svenpetersen1965/PET-Diagnostic-Clip/CBM8296_Harness/CBM8296 Diagnostic J4 Breakout Board/Rev. 0/text/210_cover_sheet.docx

Project Documentation

Commodore CBM8296 Diagnostic: J4 Breakout Board

Project number: 210

Revision: 0

Date: 16.05.2023

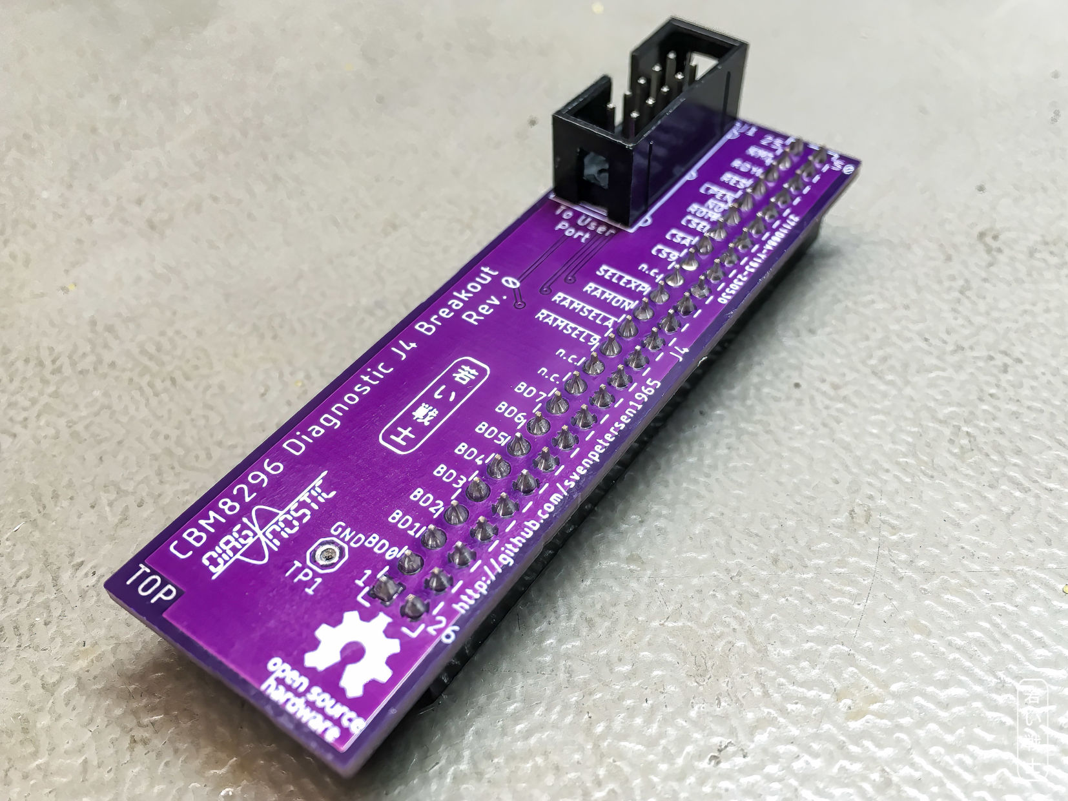
[picture p43: figure]
