svenpetersen1965/PET-Diagnostic-Clip/CBM8296_Harness/CBM8296 Diagnostic Keyboard Dongle/Rev. 0/text/212_cover_sheet.docx

Project Documentation

Commodore CBM8296 Diagnostic: Keyboard Dongle

Project number: 212

Revision: 0

Date: 16.05.2023

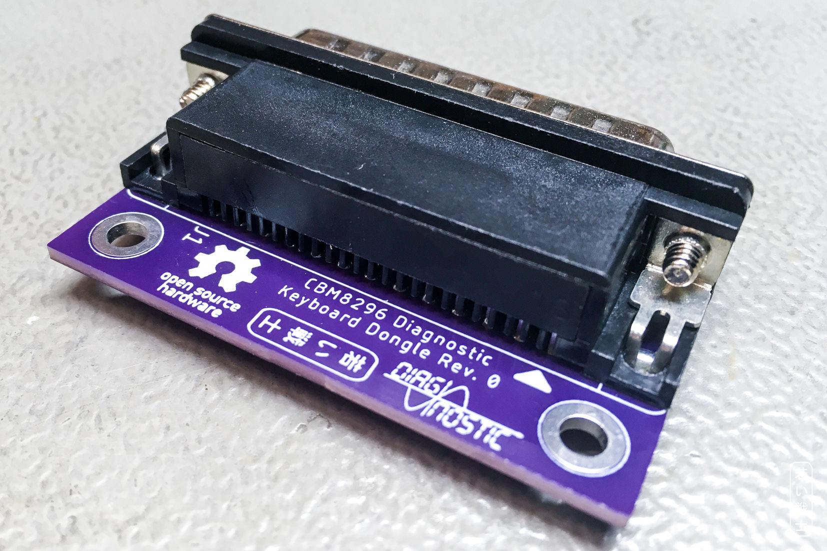
[picture p90: figure]
