svenpetersen1965/PET-Diagnostic-Clip/CBM8296_Harness/CBM8296 Diagnostic Cassette Dongle/Rev. 0/text/211_cover_sheet.docx

Project Documentation

Commodore CBM8296 Diagnostic: Cassette Dongle

Project number: 211

Revision: 0

Date: 16.05.2023

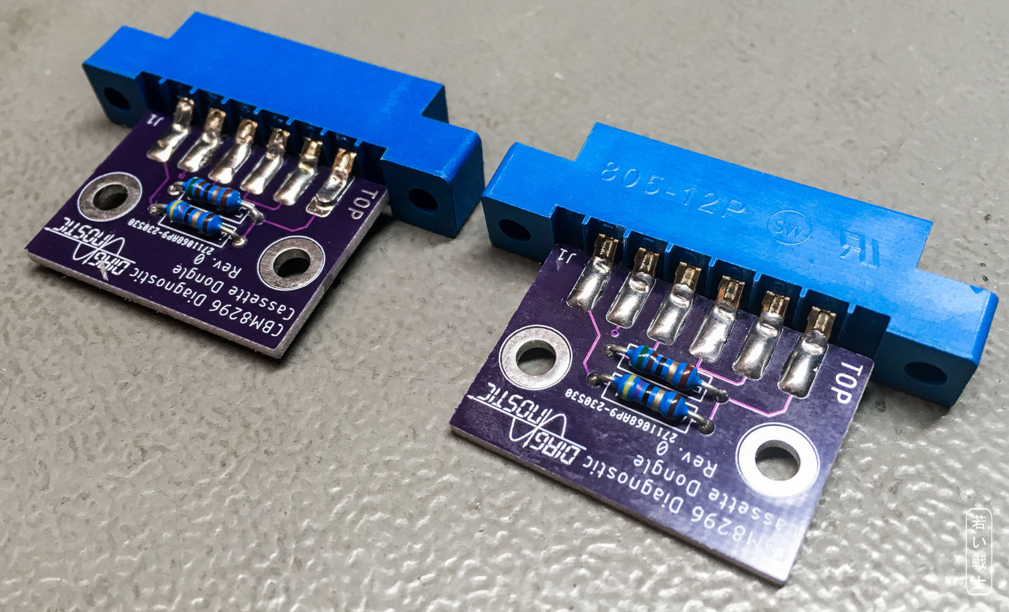
[picture p91: figure]
