svenpetersen1965/PET-Diagnostic-Clip/CBM8296_Harness/CBM8296 Diagnostic J4 Breakout Board/Rev. 0/pictures/dimensions.png

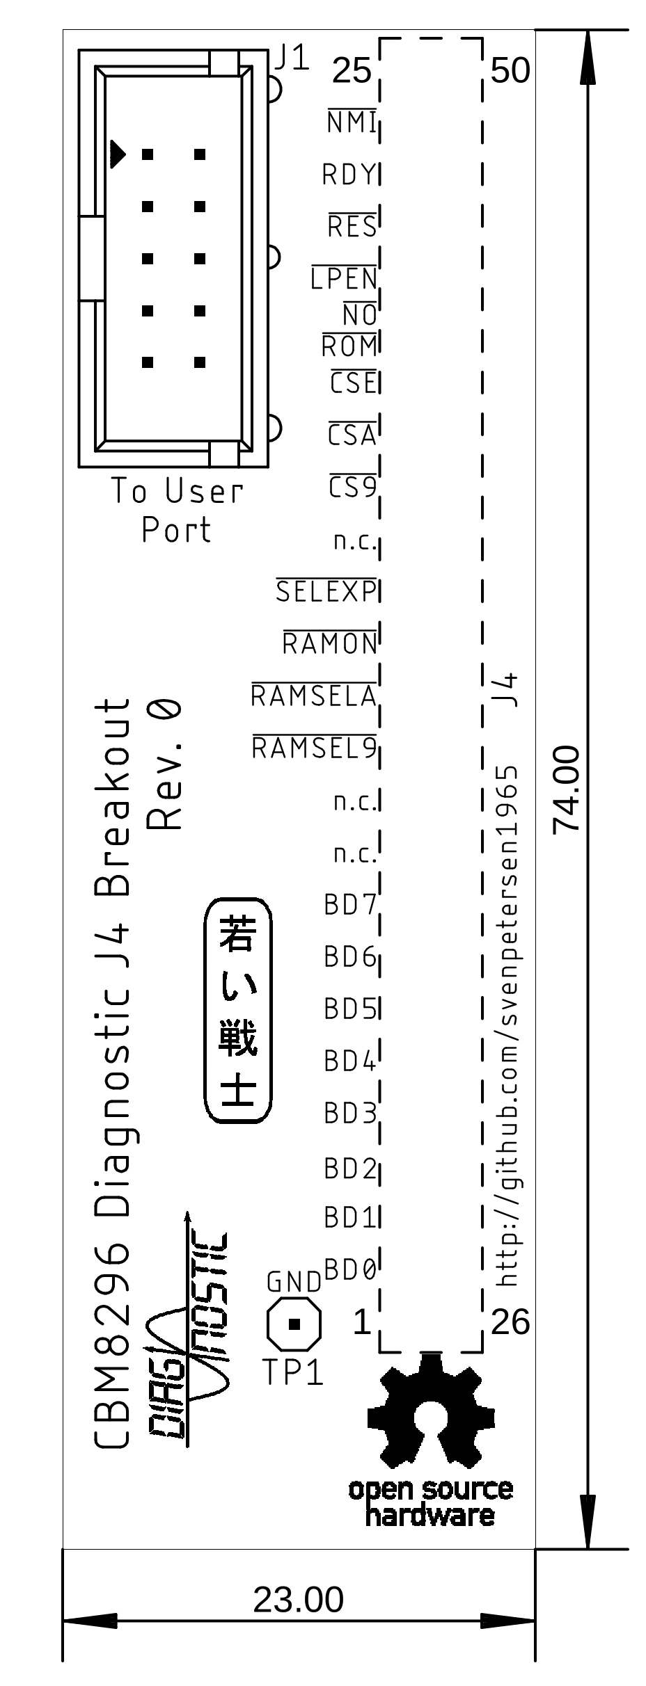
CBM8296_Harness/CBM8296 Diagnostic J4 Breakout Board/Rev. 0/pictures/dimensions.png
