svenpetersen1965/PET-Diagnostic-Clip/Diagnostic Software/40_col_diagnostic_v2.0.BIN.png

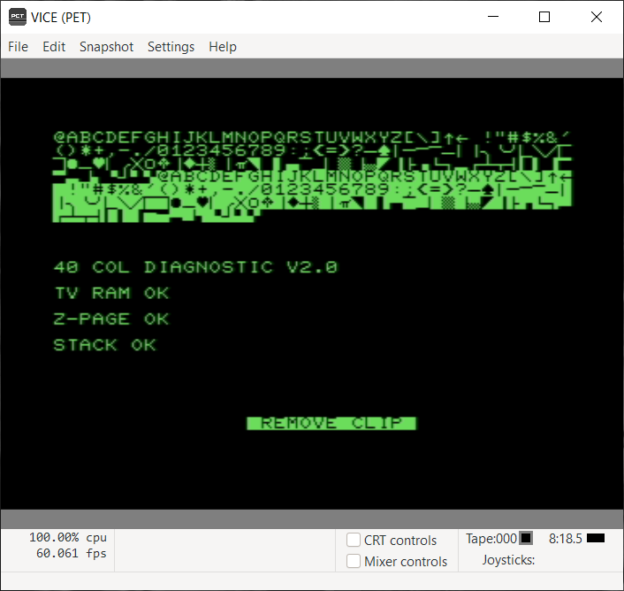
Diagnostic Software/40_col_diagnostic_v2.0.BIN.png
