svenpetersen1965/PET-Diagnostic-Clip/Diagnostic Software/80_col_diagnostic_v1.1.bin.png

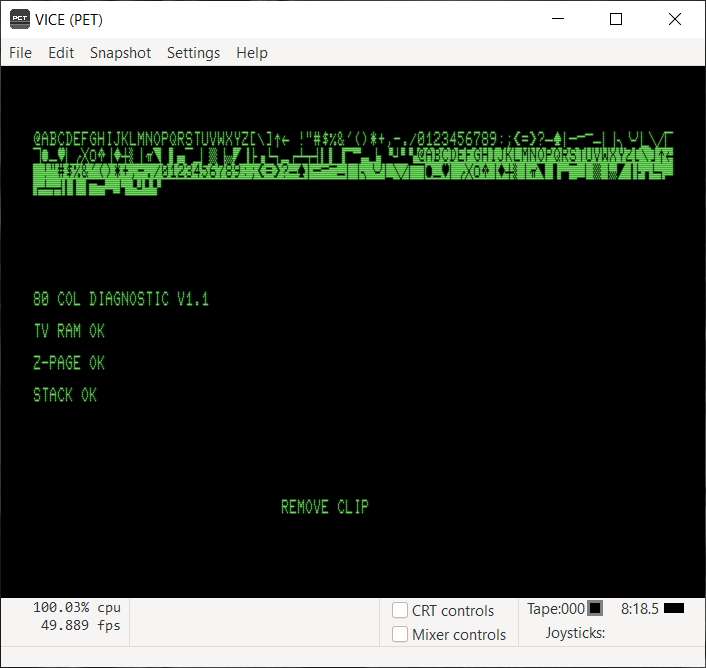
Diagnostic Software/80_col_diagnostic_v1.1.bin.png
