svenpetersen1965/PET-Diagnostic-Clip/Diagnostic Software/901447-30_diagnostic_320350g.bin.png

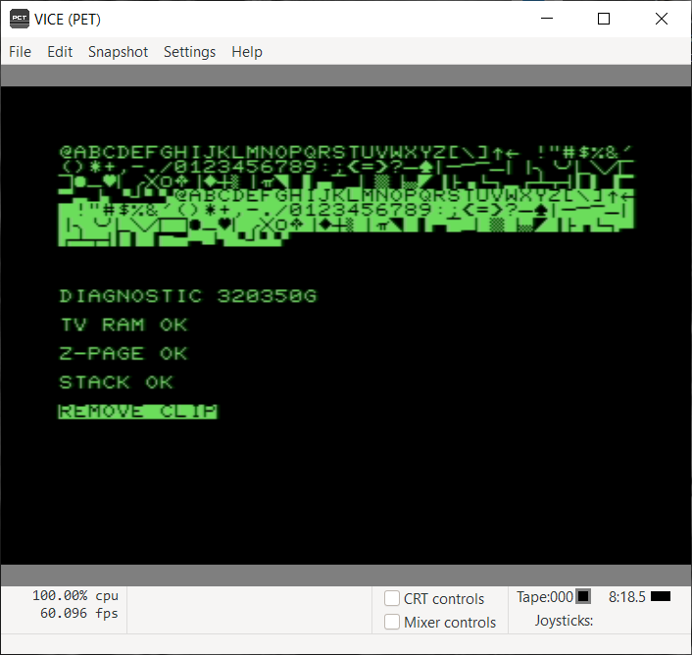
Diagnostic Software/901447-30_diagnostic_320350g.bin.png
