svenpetersen1965/PET-Diagnostic-Clip/PET-Diagnostic_Keyboard_PCB/Rev. 0/Pictures/Keyboard Connector.png

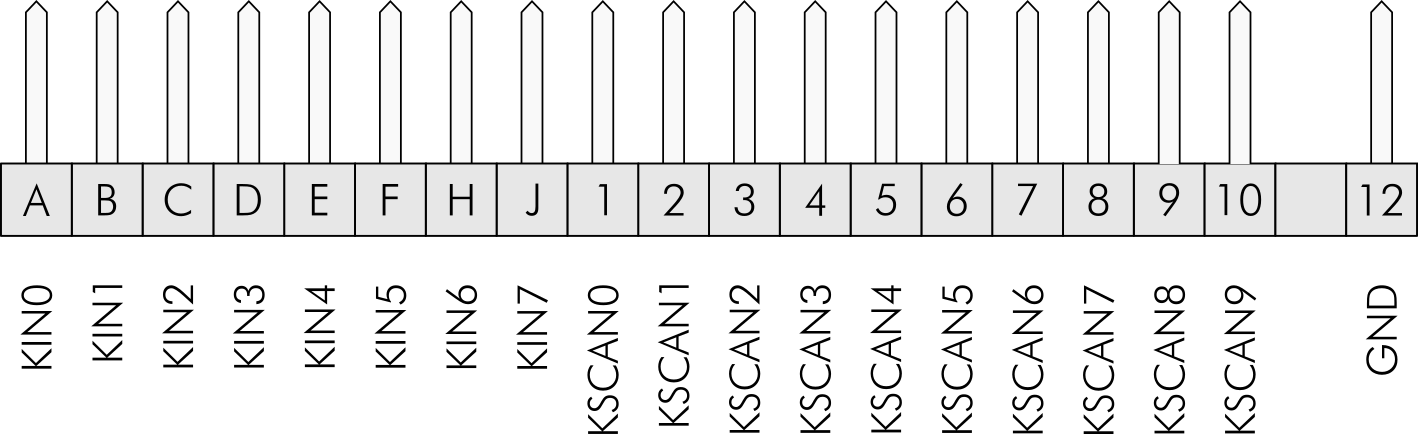
PET-Diagnostic_Keyboard_PCB/Rev. 0/Pictures/Keyboard Connector.png
