svenpetersen1965/PET-Diagnostic-Clip/PET_Diagnostic_Clip/case/Rev. 3/Label/clip_label.png

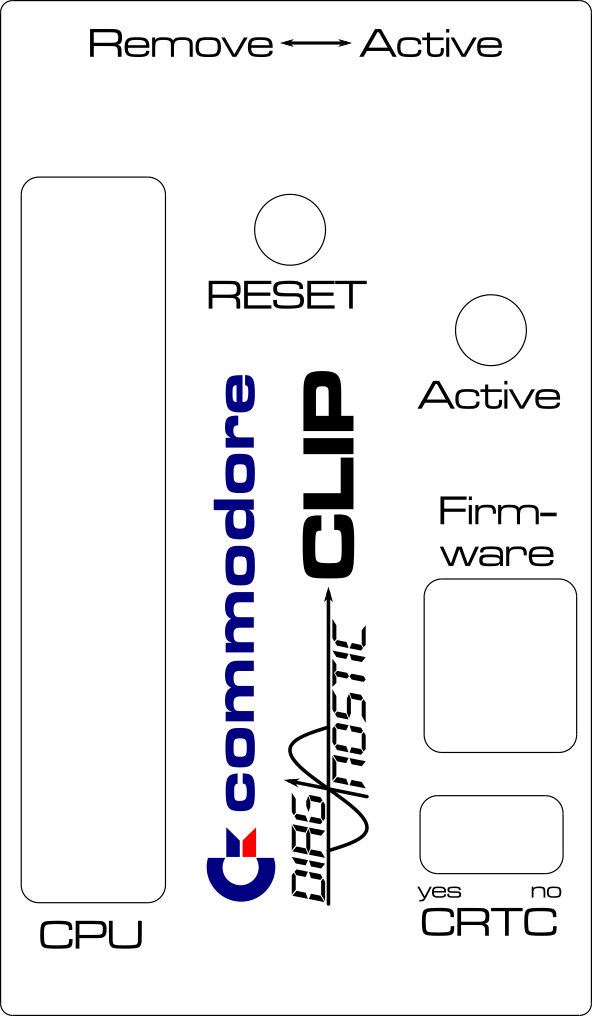
PET_Diagnostic_Clip/case/Rev. 3/Label/clip_label.png
