svenpetersen1965/PET-Diagnostic-Clip/PET_Diagnostic_Clip/Rev. 0/Pictures/0340_-_CPUada_Clip.JPG

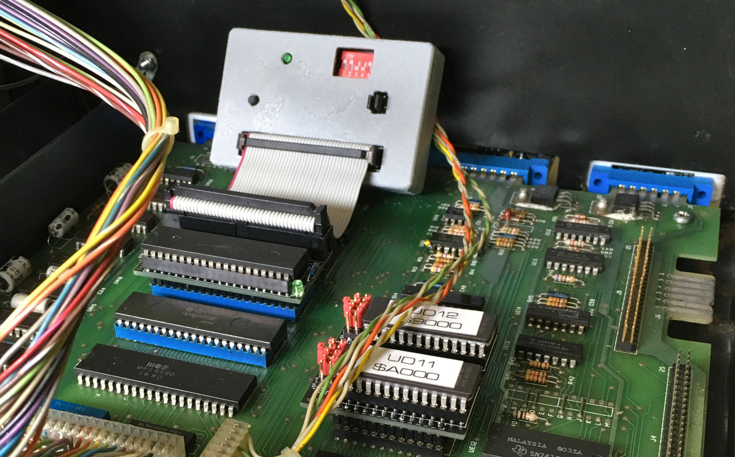
PET_Diagnostic_Clip/Rev. 0/Pictures/0340_-_CPUada_Clip.JPG
