svenpetersen1965/PET-Diagnostic-Clip/PET_Diagnostic_Clip/Rev. 0/Pictures/3843_-_Diag_Clip_PCB_v0.JPG

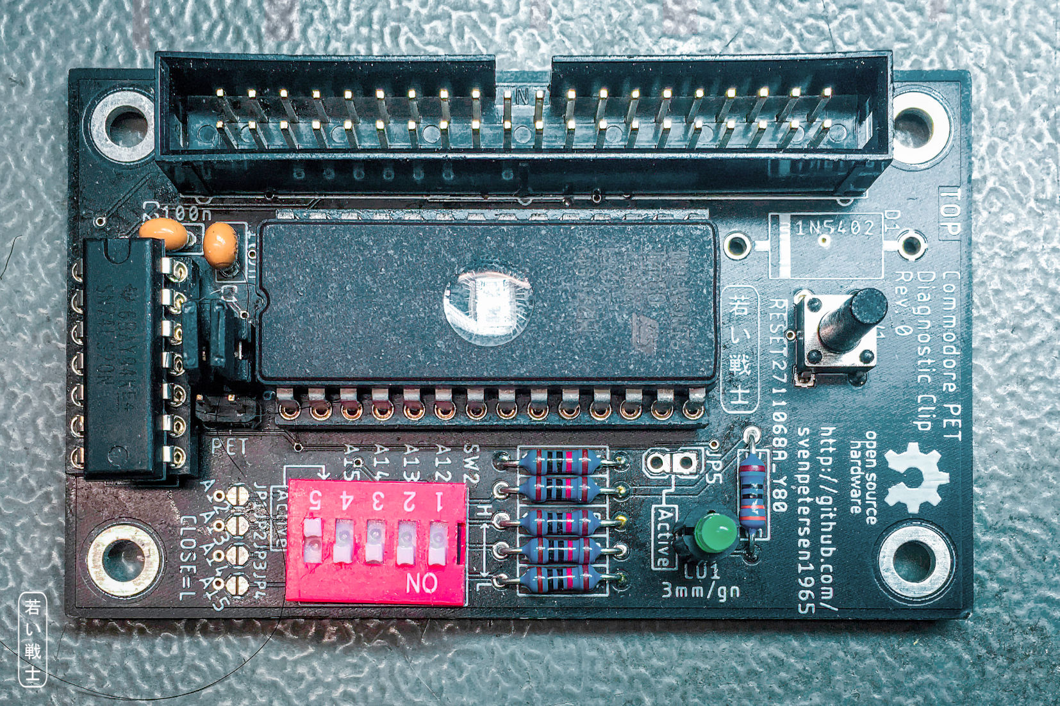
PET_Diagnostic_Clip/Rev. 0/Pictures/3843_-_Diag_Clip_PCB_v0.JPG
