svenpetersen1965/PET-Diagnostic-Clip/PET_Diagnostic_Clip/Rev. 0/Pictures/7300_-_cbm_diag_pcbs.JPG

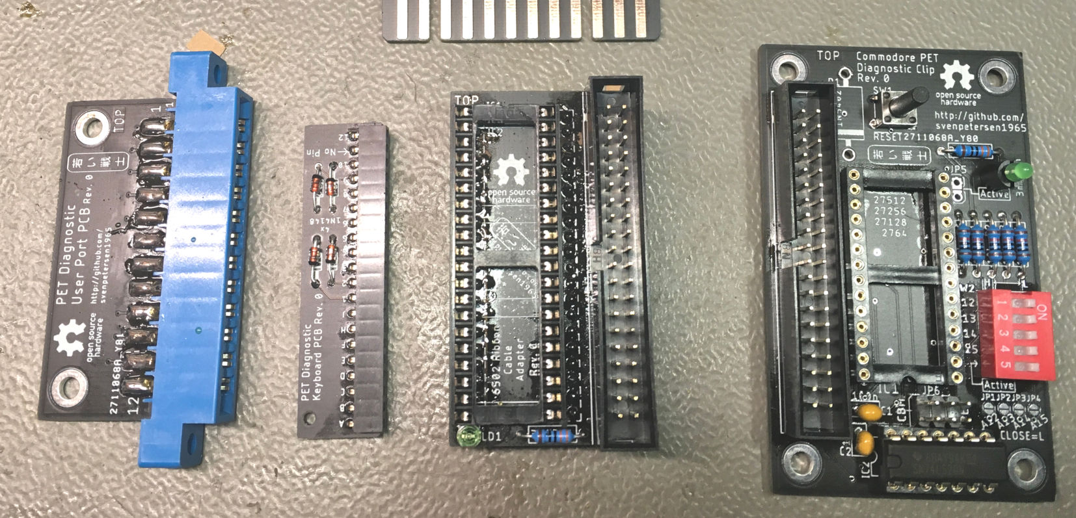
PET_Diagnostic_Clip/Rev. 0/Pictures/7300_-_cbm_diag_pcbs.JPG
