svenpetersen1965/PET-Diagnostic-Clip/PET_Diagnostic_Clip/Rev. 0/Pictures/7304_-_clip_kb_up.JPG

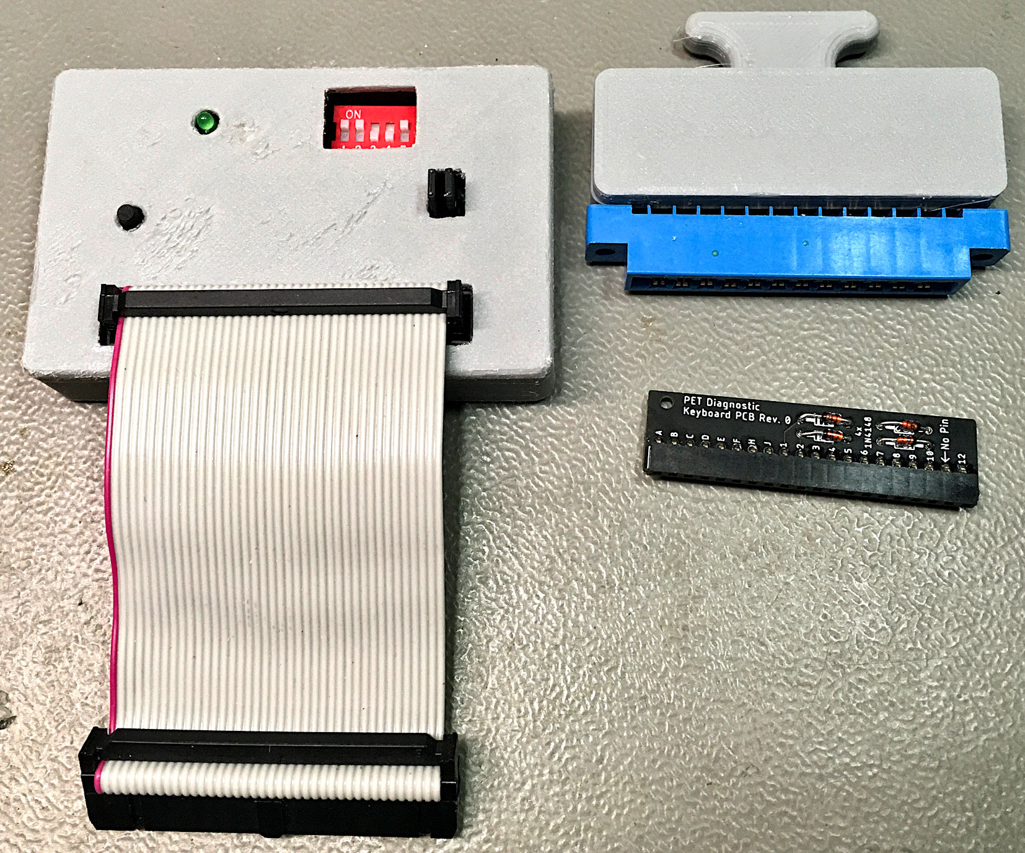
PET_Diagnostic_Clip/Rev. 0/Pictures/7304_-_clip_kb_up.JPG
