svenpetersen1965/PET-Diagnostic-Clip/PET_Diagnostic_Clip/Rev. 0/Pictures/dimensions.png

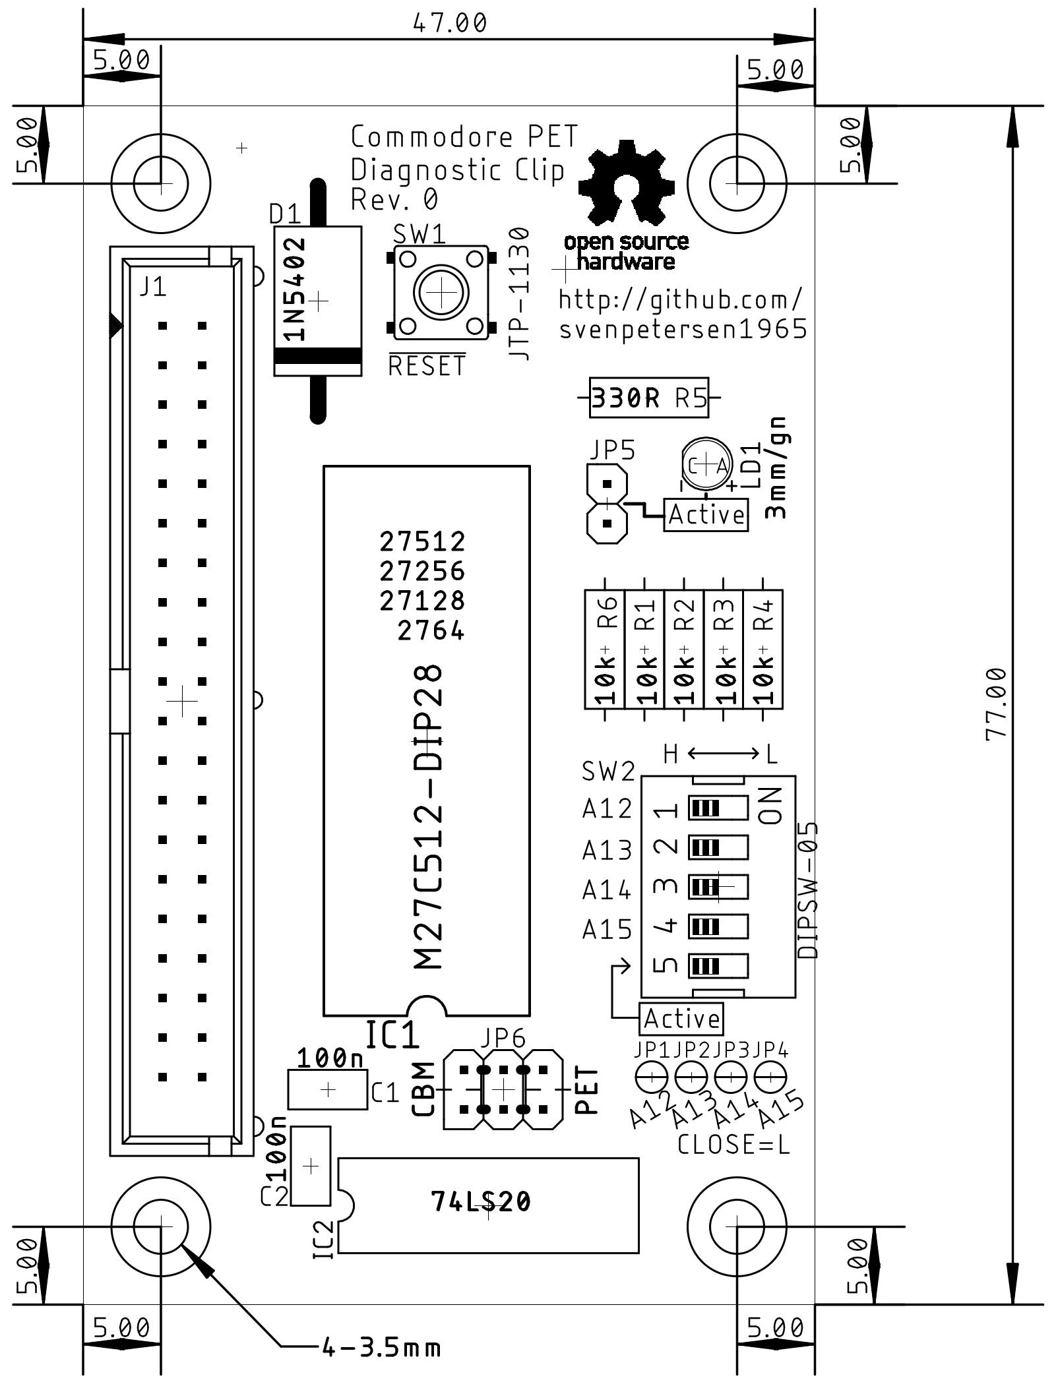
PET_Diagnostic_Clip/Rev. 0/Pictures/dimensions.png
