svenpetersen1965/PET-Diagnostic-Clip/PET_Diagnostic_Clip/Rev. 1/Pictures/0342_-_Diag_80cl_v1_1.JPG

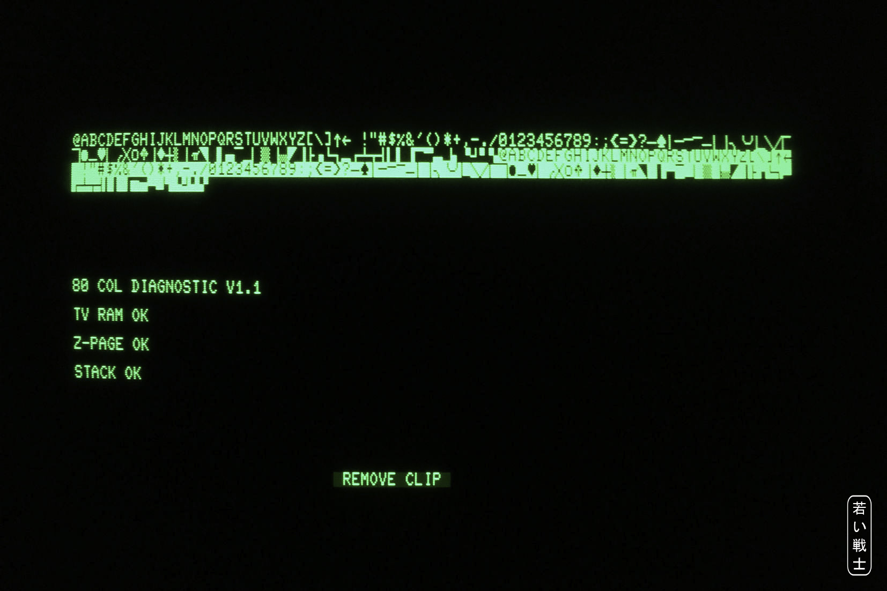
PET_Diagnostic_Clip/Rev. 1/Pictures/0342_-_Diag_80cl_v1_1.JPG
