svenpetersen1965/PET-Diagnostic-Clip/PET_Diagnostic_Clip/Rev. 1/Pictures/0711_-_Clip_rev1.JPG

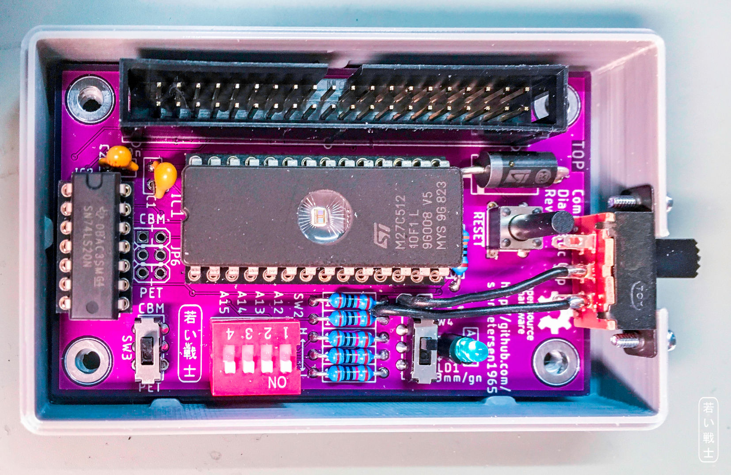
PET_Diagnostic_Clip/Rev. 1/Pictures/0711_-_Clip_rev1.JPG
