svenpetersen1965/PET-Diagnostic-Clip/PET_Diagnostic_Clip/Rev. 1/Pictures/0712_-_clip_rev.1.JPG

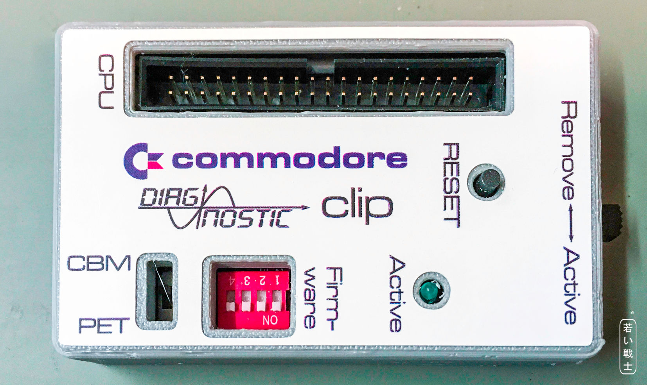
PET_Diagnostic_Clip/Rev. 1/Pictures/0712_-_clip_rev.1.JPG
