svenpetersen1965/PET-Diagnostic-Clip/PET_Diagnostic_Clip/Rev. 1/Pictures/0728_-_clip_complete.JPG

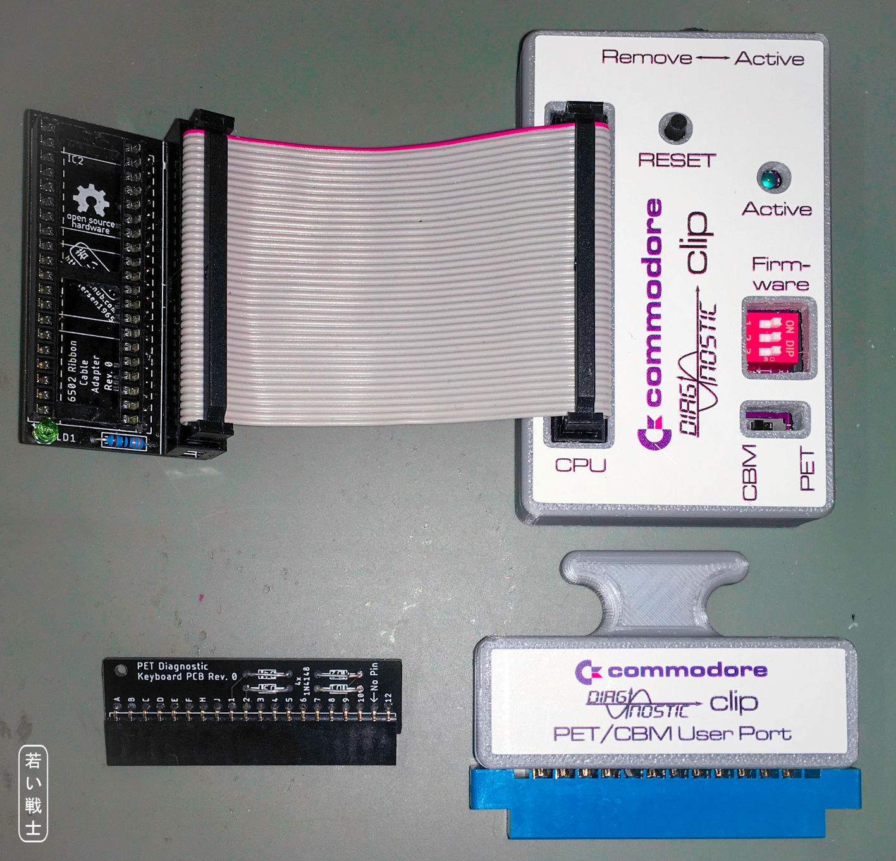
PET_Diagnostic_Clip/Rev. 1/Pictures/0728_-_clip_complete.JPG
