svenpetersen1965/PET-Diagnostic-Clip/PET_Diagnostic_Clip/Rev. 1/Pictures/3514_-_diag_80col_8032_loop.JPG

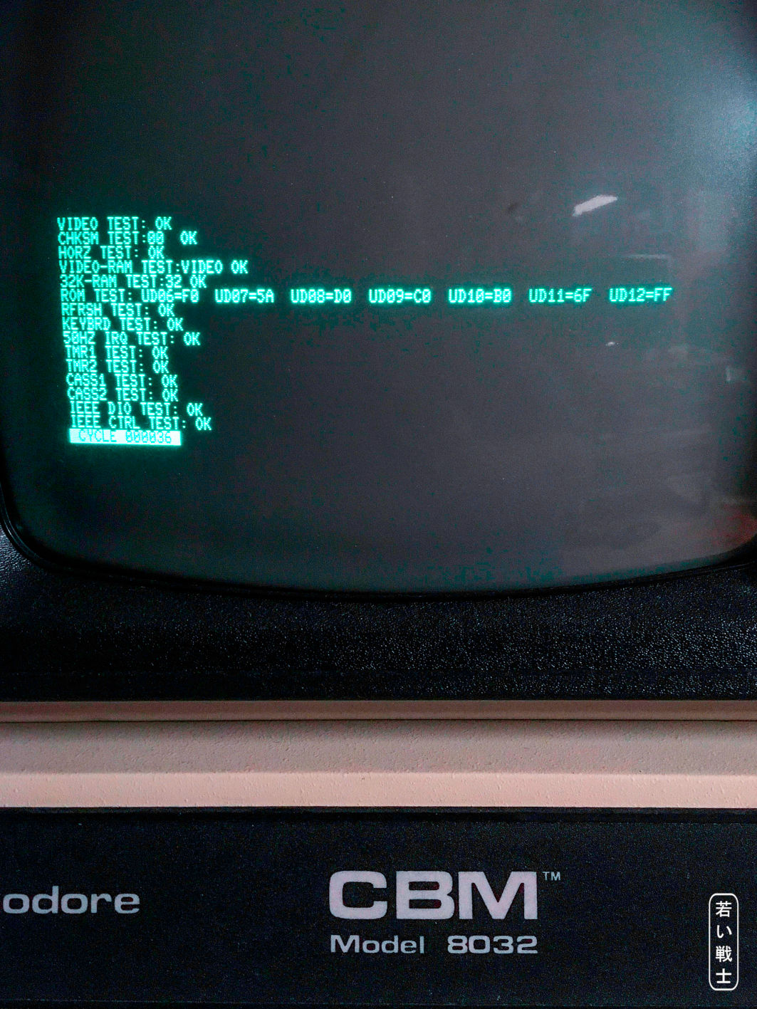
PET_Diagnostic_Clip/Rev. 1/Pictures/3514_-_diag_80col_8032_loop.JPG
