svenpetersen1965/PET-Diagnostic-Clip/PET_Diagnostic_Clip/Rev. 2/Pictures/3821_-_clipv2_open.JPG

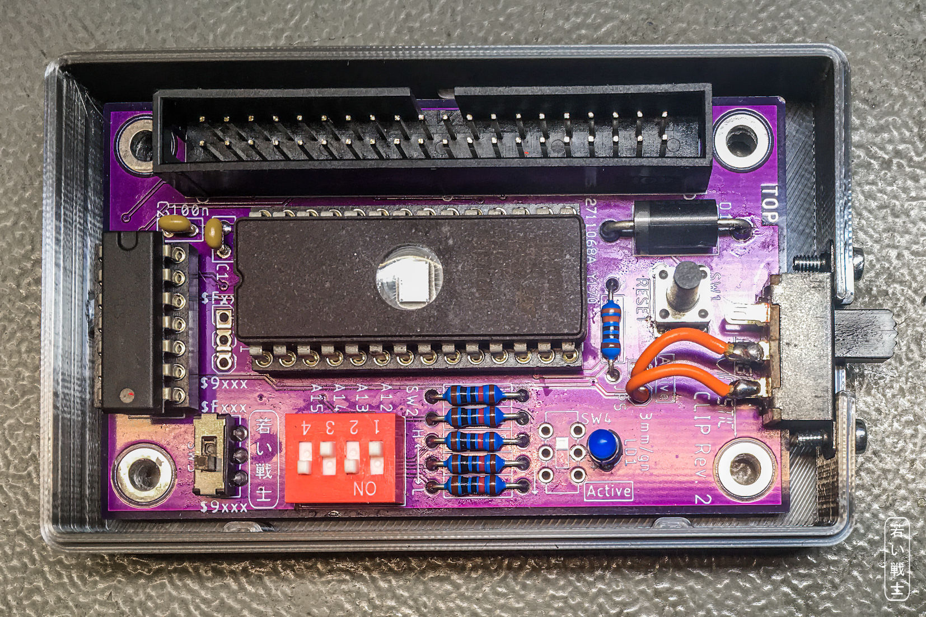
PET_Diagnostic_Clip/Rev. 2/Pictures/3821_-_clipv2_open.JPG
