svenpetersen1965/PET-Diagnostic-Clip/PET_Diagnostic_Clip/Rev. 3/Pictures/2621_-_clip_v3.JPG

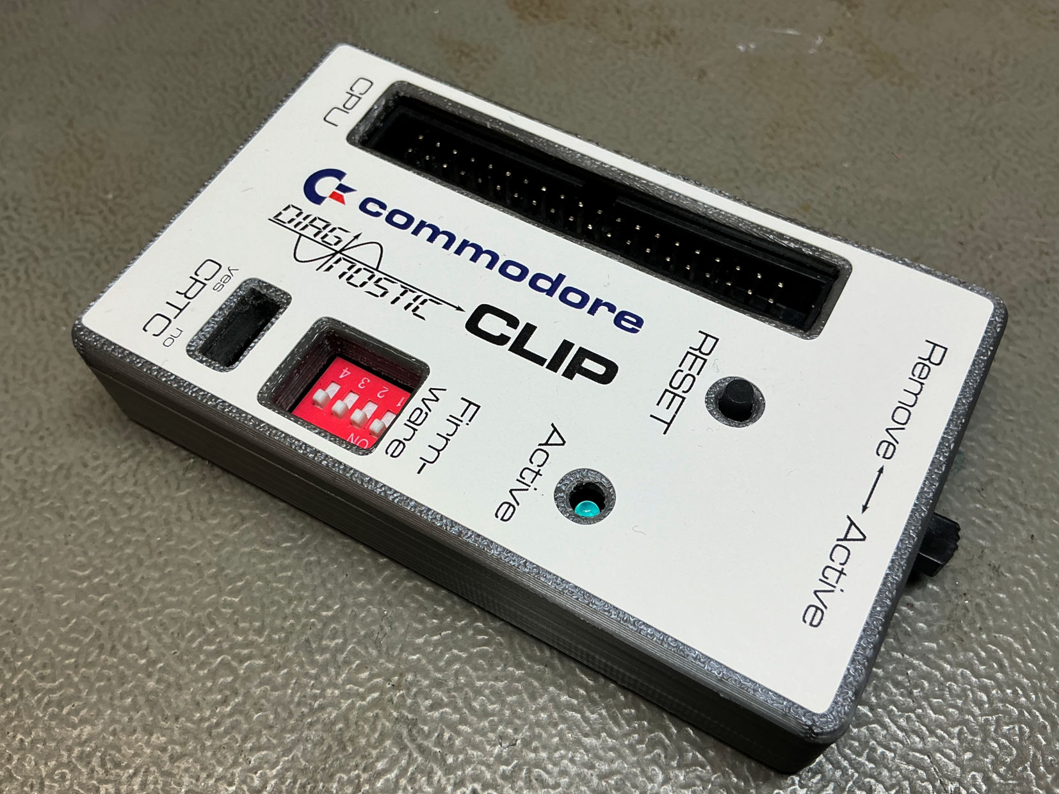
PET_Diagnostic_Clip/Rev. 3/Pictures/2621_-_clip_v3.JPG
