svenpetersen1965/PET-Diagnostic-Clip/PET_Diagnostic_Clip/Rev. 3/Pictures/4428_-_3016_diag320350g_start.JPG

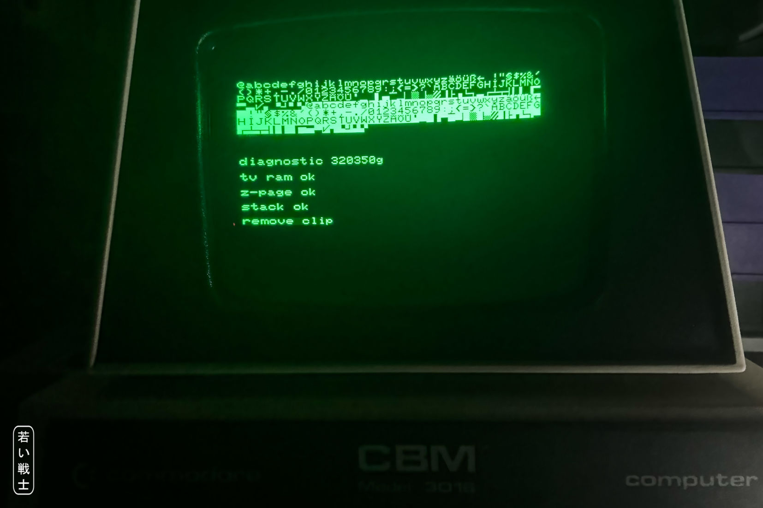
PET_Diagnostic_Clip/Rev. 3/Pictures/4428_-_3016_diag320350g_start.JPG
