svenpetersen1965/PET-Diagnostic-Clip/PET_Diagnostic_Clip/Rev. 3/Pictures/4429_-_3016_diag320350g_loop1.JPG

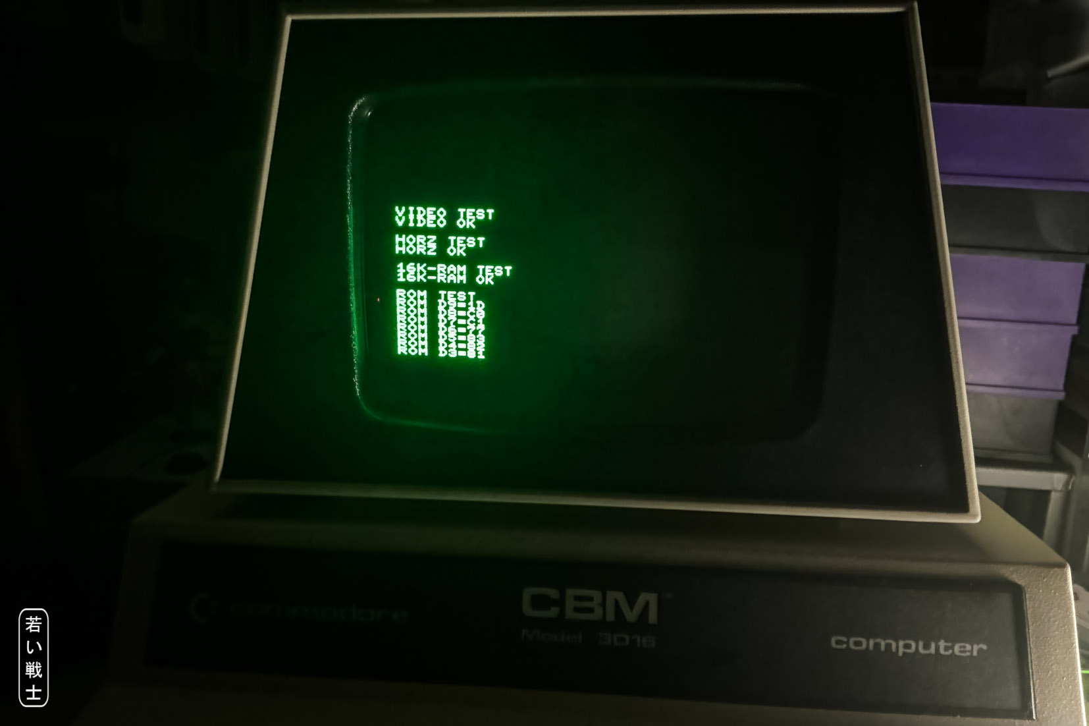
PET_Diagnostic_Clip/Rev. 3/Pictures/4429_-_3016_diag320350g_loop1.JPG
