svenpetersen1965/PET-Diagnostic-Clip/PET-Diagnostic_Keyboard_PCB/Rev. 0/Excel/PETDiag_KBDongle_calc_v0_0.xlsx

Commodore PET Diagnostic Clip: Keyboard Dongle Rev. 0
Calculation (of 13.12.2022) Rev. 0.0
Pos. | Qty | Value | €/ea | € | Comment
1 | 1 | 166-2-01-00 | 1.00 € | 1.00 € | 2 layer, Cu 35µ, HASL, 53.0mm x 14.0mm, 1.6mm FR4
2 | 4 | 1N4148 | 0.03 € | 0.12 € | Diode 1N4148
3 | 1 | BL1-85AXX-20U | 0.50 € | 0.50 € | e.g. MPE Garry, Reichelt BL 1x20W8 2,54
4 |  |  | total | 1.62 €
