svenpetersen1965/PET-Diagnostic-Clip/PET_Diagnostic_User_Port_PCB/Rev. 0/Excel/PET_Diag_UP.csv

Qty | Value | Device | Package | Parts | Description
2 |  | BOHR3,5 | BOHR3,5 | DRL1, DRL2
1 | OPEN_SOURCE_HW | OPEN_SOURCE_HW | OPENHW | U$13
1 | PET-USERPORT | PET-USERPORT | USERPORT | J1
