svenpetersen1965/PET-Diagnostic-Clip/PET_Diagnostic_User_Port_PCB/Rev. 0/Excel/PETDiag_UPDongle_calc_v0_0.xlsx

Commodore PET Diagnostic Clip: User Port Dongle Rev. 0
Calculation of 13.12.2022 Rev. 0.0
Pos. | Qty | Value | €/ea | € | Comment
1 | 1 | 165-2-01-00 | 1.00 € | 1.00 € | 2 layer, Cu 35µ, HASL, 54.0mm x 20.0mm, 1.6mm FR4
2 | 1 | 2x12, 3.96mm pitch | 3.00 € | 3.00 € | edge connector, C64 user port, Ali Express: Series 805
3 |  |  | Total | 4.00 €
