svenpetersen1965/PET-Diagnostic-Clip/6502_Ribbon_Cable_Adapter/Rev. 0/Excel/PETDiag_6502Ada_calc_v0_0.xlsx

Commodore PET Diagnostic Clip: 6502 Ribbon Cable Adapter Rev. 0
Calculation Rev. 0.0
Pos. | Qty | Value | Spalte1 | Spalte2 | Comment
1 | 1 | 162-2-01-00 | 1.00 € | 1.00 € | 2 layer, Cu 35µ, HASL, 58.8mm x 32.0mm, 1.6mm FR4
2 | 1 | 2x20 box header, 2.54mm pitch | 0.23 € | 0.23 € | 2x20, box pin header or standard pin header, e.g. reichelt.de WSL 40G
3 | 1 | 330R | 0.10 € | 0.10 € | 1/4W, 5%
4 | 1 | 3mm/gn | 0.15 € | 0.15 € | standard LED 3mm/green
5 | 1 | 6502PINS | 2.60 € | 2.60 € | Precision round pin header, e.G. bkl-electronic.de Art.-Nr. 10120540, Reichelt BKL 10120540
6 | 2 | DIP40 socket | 0.69 € | 1.38 € | Socket for 6502
7 | 2 | IDC Socket | 0.27 € | 0.54 €
8 | 1 | 10cm ribbon cable, 40p, 1.27mm | 0.23 € | 0.23 €
 |  |  | total | 6.23 €
