svenpetersen1965/PET-Diagnostic-Clip/PET_Diagnostic_Clip/Rev. 1/Excel/PETDiag_Clip_calc_v1_0.xlsx

Commodore PET Diagnostic: Diagnostic Clip Rev. 1
Calculation (13.12.2022) Rev. 1.0
Pos. | Qty | Value | €/ea | € | Comment
1 | 1 | 163-2-01-01 | 1.00 € | 1.00 € | 2 layer, Cu 35µ, HASL, 77.0mm x 47.0mm, 1.6mm FR4
2 | 1 | external DPDT switch wired up | 0.45 € | 0.45 € | Reichelt.de: T217 or AliExpress SS22F25-G7 + 10cm AWG24 cable
3 | 1 | 2x20 box header, 2.54mm pitch | 0.23 € | 0.23 € | 2x20, box pin header or standard pin header, e.g. reichelt.de WSL 40G
4 | 2 | 100n/50V | 0.10 € | 0.20 € | cer. cap, 2.5mm pitch
5 | 5 | 10k | 0.10 € | 0.50 € | 1/4W, 5%
6 | 1 | 1N5402 | 0.08 € | 0.08 € | 5V TVS diode. ST Micro. E.g. Reichelt: 1N 5908, tme.eu: 1N5908
7 | 1 | 330R | 0.10 € | 0.10 € | 1/4W, 5%
8 | 1 | 3mm/gn | 0.15 € | 0.15 € | standard LED 3mm/green
9 | 1 | 74LS20 | 1.06 € | 1.06 € | e.G. RENESAS, e.G. Reichelt LS 20
10 | 1 | DIPSW-04 | 0.35 € | 0.35 € | Standard DIP-Switch with 4 switches (switch side facing up) The DIP-Switch can be replaced with a 2 switch DIP Switch and hardwire switch 3 and 4. Reichelt NT 04 or NT 02
11 | 1 | mini slide switch, 2.54mm, DPDT, through hole | 0.15 € | 0.15 € | Ali Express, ebay, Amazon, search term "MSS22D18"
12 | 0 | mini slide switch, 2.54mm, DPDT, through hole | 0.15 € | 0.00 € | do not place
13 | 1 | JTP-1130 | 0.16 € | 0.16 € | standard TACT switch 6mm x 6mm, height = 13mm
14 | 0 | JUMPER2X3 | 0.00 € | 0.00 € | do not place
15 | 1 | M27C512-DIP28 | 6.70 € | 6.70 € | M27C512 EPROM (or M27C256 or M27C128)
 |  |  | total | 11.13 €
