svenpetersen1965/PET-Diagnostic-Clip/PET_Diagnostic_Clip/case/Rev. 1/stl/Diag_clip_top_shell.stl

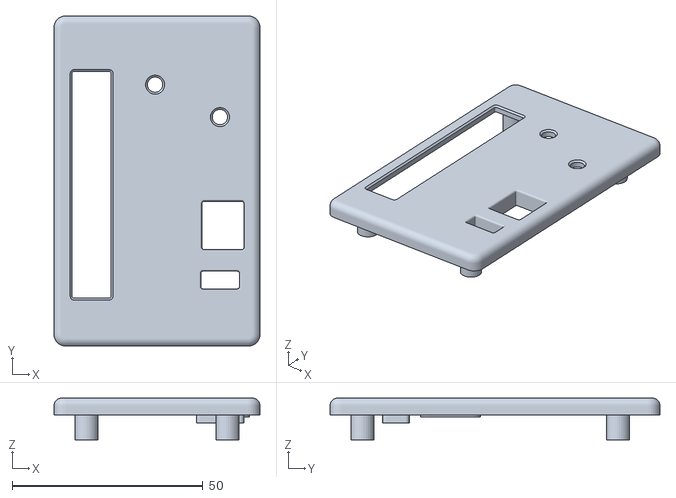
[picture p128: CAD file, 2023-02-27]
PET_Diagnostic_Clip/case/Rev. 1/stl/Diag_clip_top_shell.stl
54.0 x 86.5 x 11.0
