svenpetersen1965/PET-Diagnostic-Clip/PET_Diagnostic_Clip/Rev. 0/dxf/PET_Diag_Clip.dxf

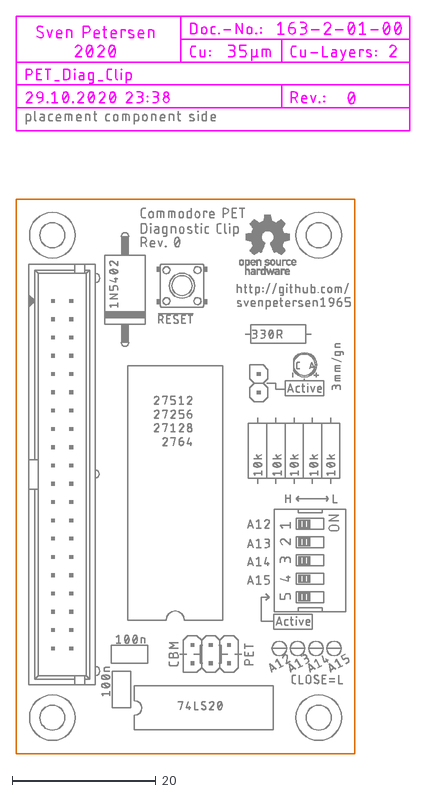
[picture p130: CAD file, 2023-02-27]
PET_Diagnostic_Clip/Rev. 0/dxf/PET_Diag_Clip.dxf
54.6 x 102.4
