svenpetersen1965/PET-Diagnostic-Clip/PET_Diagnostic_Clip/Rev. 1/dxf/PET_Diag_Clip.dxf

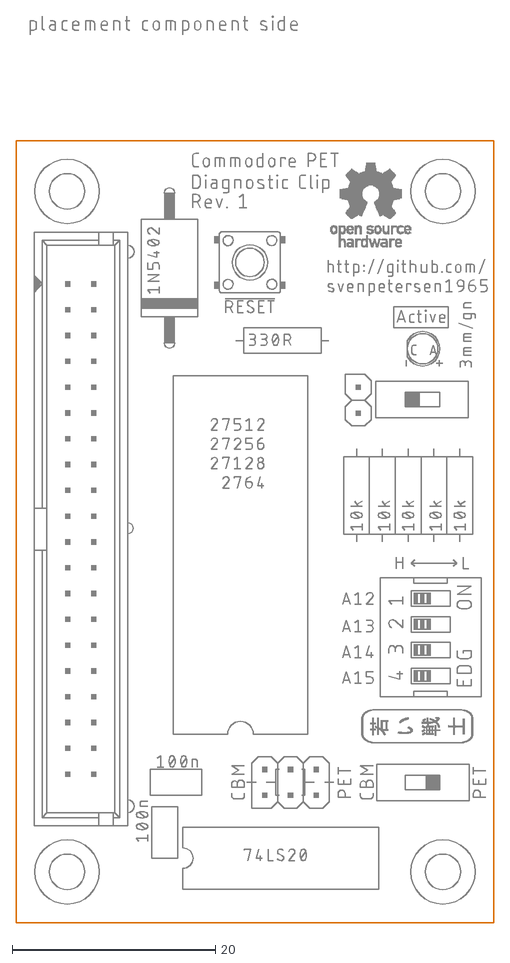
[picture p131: CAD file, 2023-02-27]
PET_Diagnostic_Clip/Rev. 1/dxf/PET_Diag_Clip.dxf
47.0 x 89.2
