svenpetersen1965/PET-Diagnostic-Clip/PET_Diagnostic_Clip/Rev. 3/dxf/PET_Diag_Clip.dxf

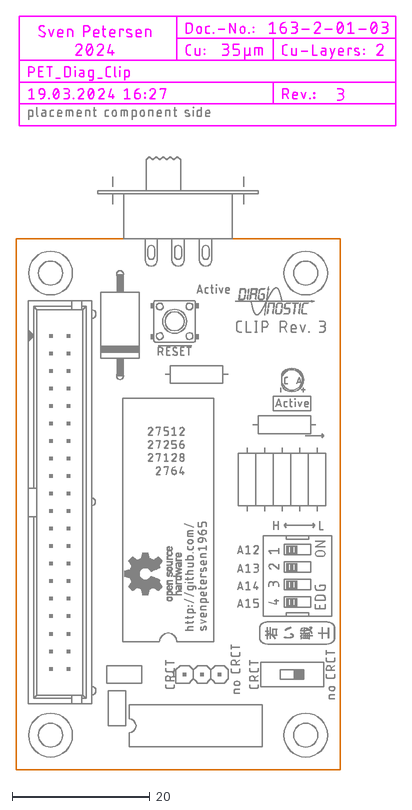
[picture p133: CAD file, 2026-01-05]
PET_Diagnostic_Clip/Rev. 3/dxf/PET_Diag_Clip.dxf
55.1 x 109.2
