svenpetersen1965/PET-Diagnostic-Clip/PET_Diagnostic_User_Port_PCB/case/stl/PETDiag_UP_bottom_shell.stl

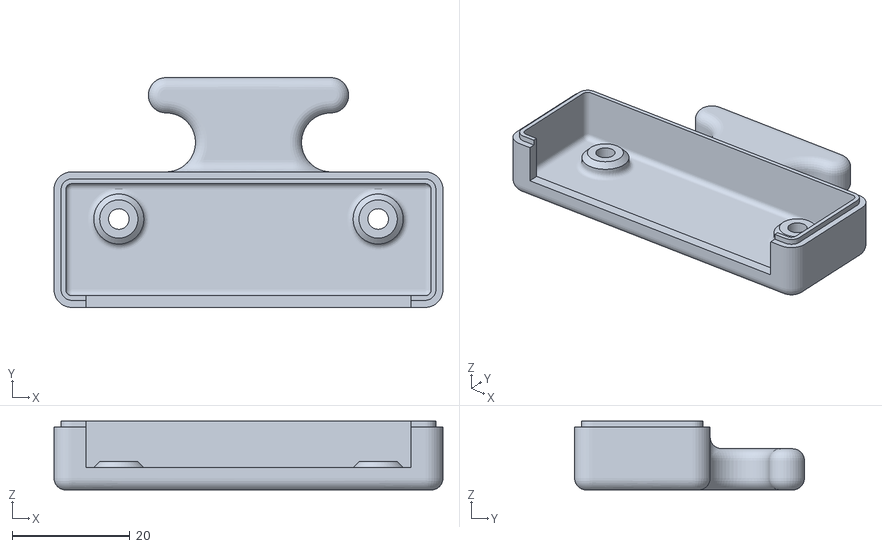
[picture p134: CAD file, 2023-02-27]
PET_Diagnostic_User_Port_PCB/case/stl/PETDiag_UP_bottom_shell.stl
66.0 x 39.0 x 11.7
