svenpetersen1965/PET-Diagnostic-Clip/PET_Diagnostic_User_Port_PCB/Rev. 0/dxf/PET_Diag_UP.dxf

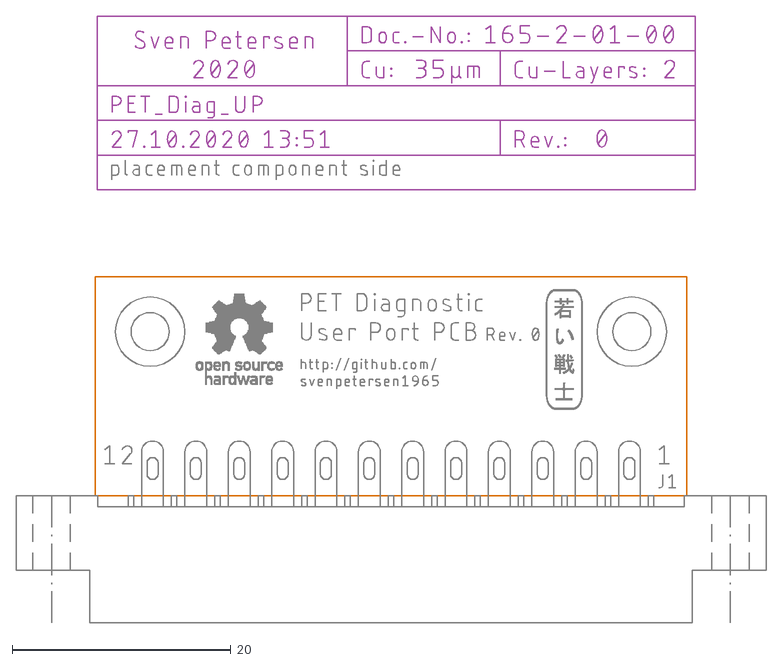
[picture p135: CAD file, 2023-02-27]
PET_Diagnostic_User_Port_PCB/Rev. 0/dxf/PET_Diag_UP.dxf
68.5 x 55.4
