svenpetersen1965/PET-Diagnostic-Clip/CBM8296_Harness/CBM8296 Diagnostic Cassette Dongle/3D printed case/Rev. 0/STL/8296_CP_top_shell.stl

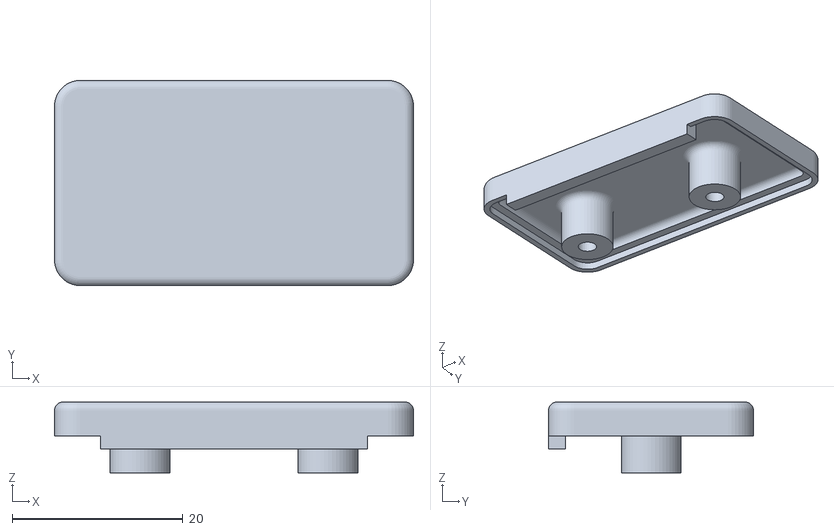
[picture p136: CAD file, 2023-06-11]
CBM8296_Harness/CBM8296 Diagnostic Cassette Dongle/3D printed case/Rev. 0/STL/8296_CP_top_shell.stl
42.0 x 24.0 x 8.30
