svenpetersen1965/PET-Diagnostic-Clip/CBM8296_Harness/CBM8296 Diagnostic Keyboard Dongle/3D printed case/Rev. 0/STL/8296KB_bottom_shell.stl

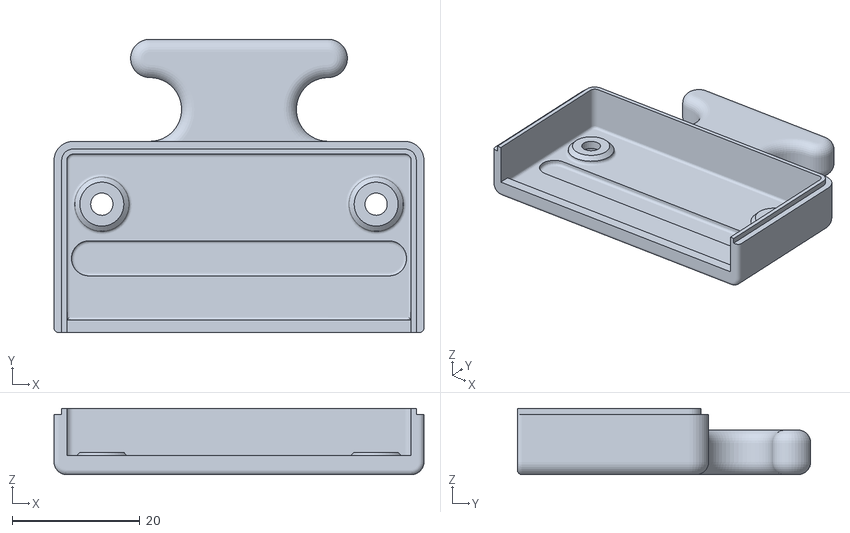
[picture p137: CAD file, 2023-06-11]
CBM8296_Harness/CBM8296 Diagnostic Keyboard Dongle/3D printed case/Rev. 0/STL/8296KB_bottom_shell.stl
58.0 x 46.0 x 10.4
