svenpetersen1965/PET-Diagnostic-Clip/PET_Diagnostic_Clip/case/Rev. 0/stl/PETDiag_Clip_bottom_shell.stl

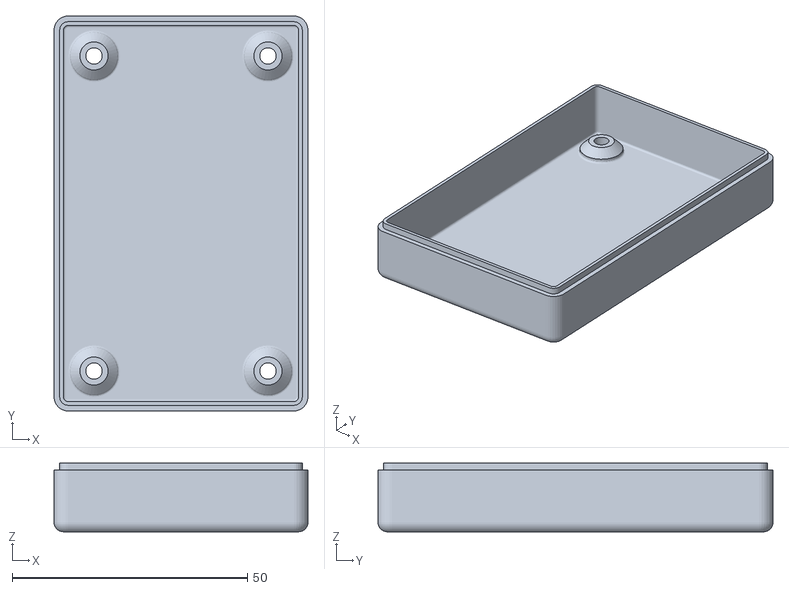
[picture p138: CAD file, 2023-02-27]
PET_Diagnostic_Clip/case/Rev. 0/stl/PETDiag_Clip_bottom_shell.stl
54.0 x 84.0 x 14.6
