svenpetersen1965/PET-Diagnostic-Clip/PET_Diagnostic_Clip/case/Rev. 3/stl/clip_top_shell.stl

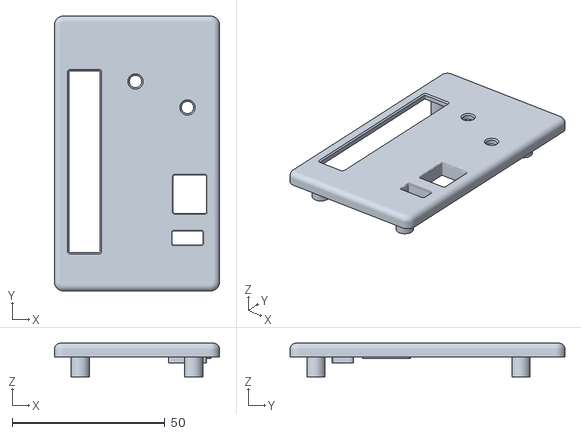
[picture p140: CAD file, 2026-01-05]
PET_Diagnostic_Clip/case/Rev. 3/stl/clip_top_shell.stl
54.0 x 89.9 x 11.0
