svenpetersen1965/PET-Diagnostic-Clip/PET_Diagnostic_User_Port_PCB/case/stl/PETDiag_UP_top_shell.stl

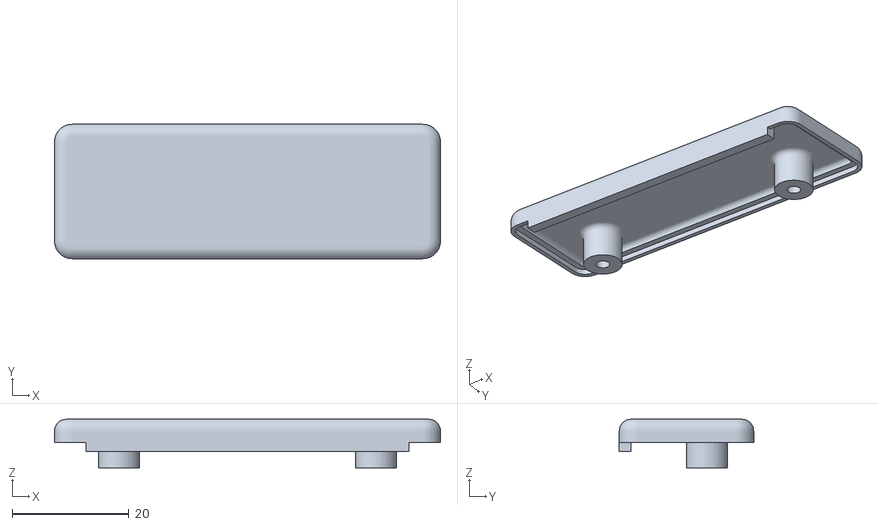
[picture p141: CAD file, 2023-02-27]
PET_Diagnostic_User_Port_PCB/case/stl/PETDiag_UP_top_shell.stl
66.0 x 23.0 x 8.30
