svenpetersen1965/PET-Diagnostic-Clip/CBM8296_Harness/CBM8296 Diagnostic Firmware/pictures/5140_-_Test on a CBM8032.JPG

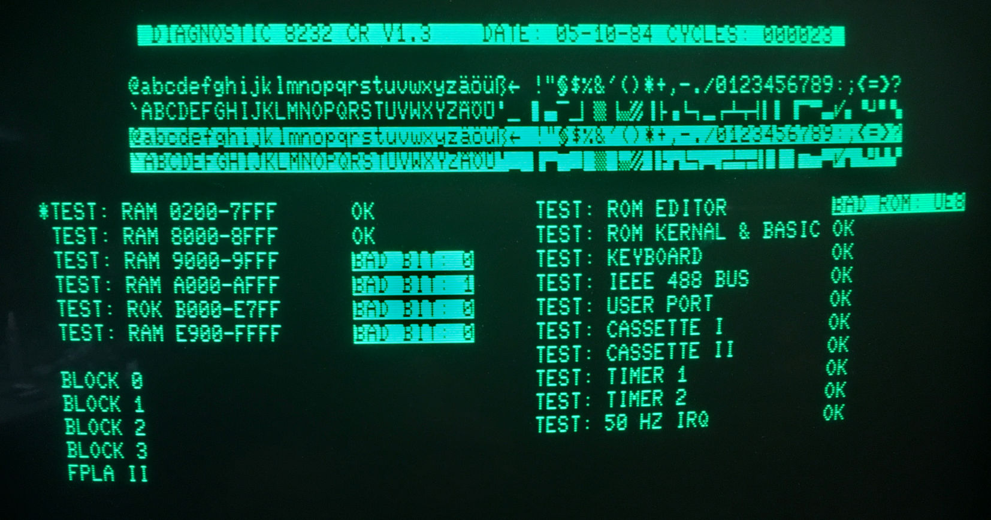
CBM8296_Harness/CBM8296 Diagnostic Firmware/pictures/5140_-_Test on a CBM8032.JPG
