svenpetersen1965/PET-Diagnostic-Clip/Diagnostic Software/PET_Tester/petester_noCRTC.bin.png

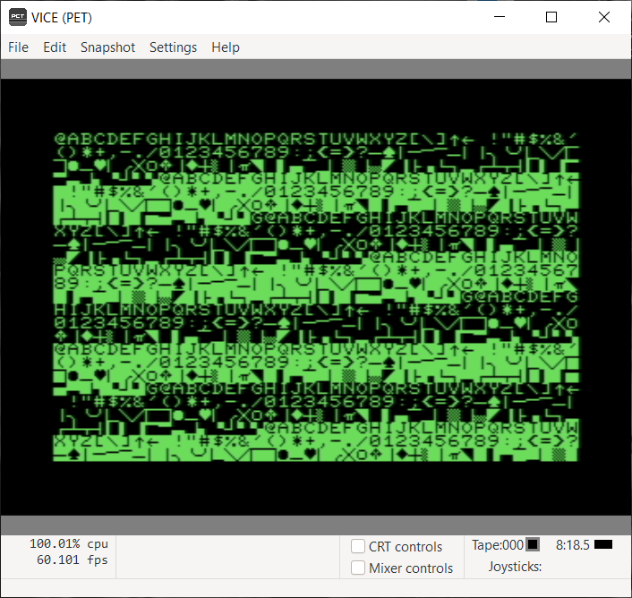
Diagnostic Software/PET_Tester/petester_noCRTC.bin.png
