svenpetersen1965/PET-Diagnostic-Clip/Diagnostic Software/PET_Tester/pettest2_40col_CRTC.bin.png

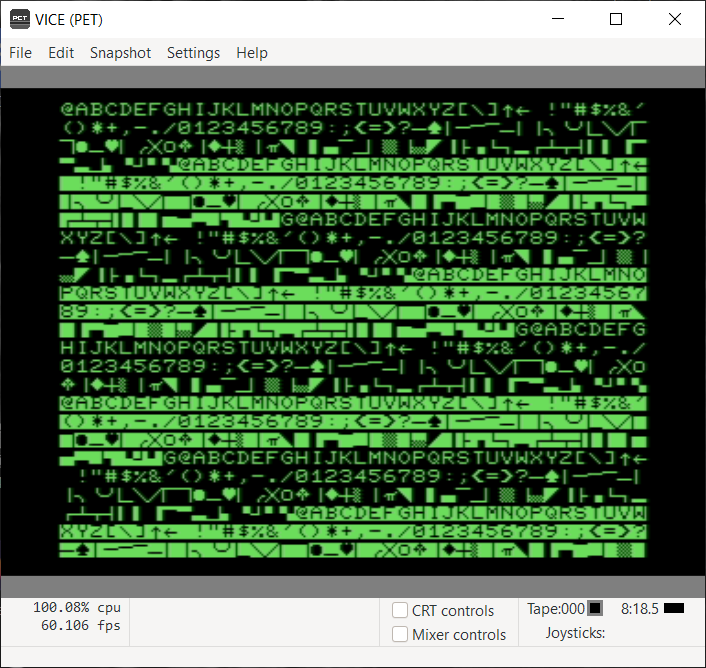
Diagnostic Software/PET_Tester/pettest2_40col_CRTC.bin.png
