svenpetersen1965/PET-Diagnostic-Clip/Diagnostic Software/PET_Tester/pettester8032.bin.png

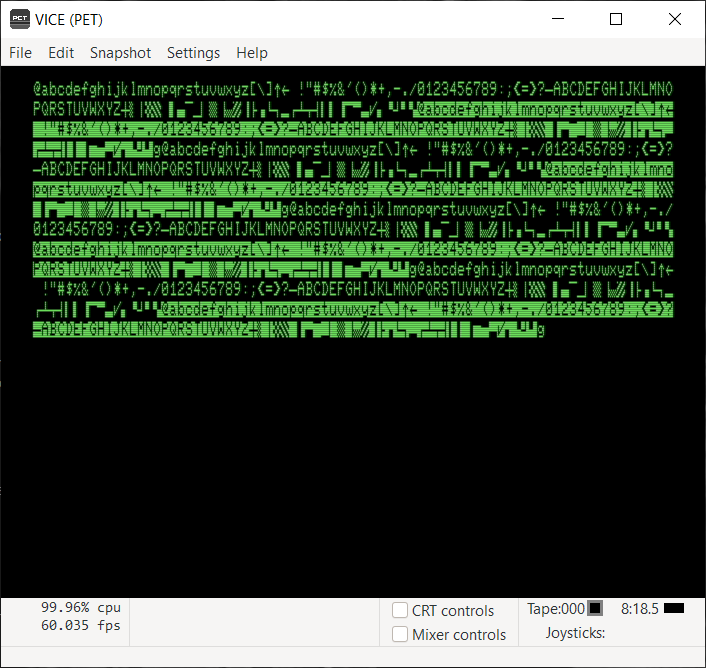
Diagnostic Software/PET_Tester/pettester8032.bin.png
