svenpetersen1965/PET-Diagnostic-Clip/PET_Diagnostic_Clip/Rev. 0/Pictures/0342_-_Test_page1.JPG

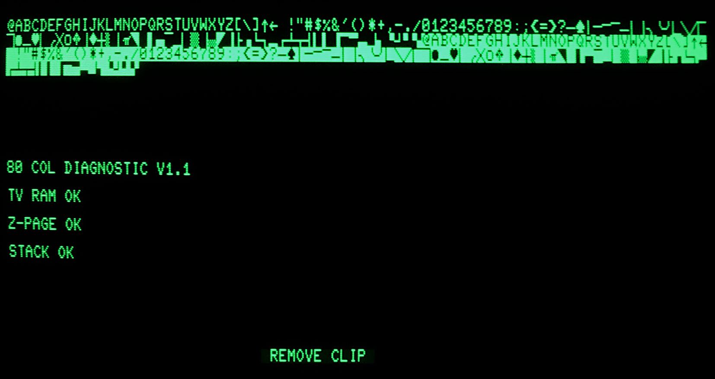
PET_Diagnostic_Clip/Rev. 0/Pictures/0342_-_Test_page1.JPG
