svenpetersen1965/PET-Diagnostic-Clip/PET_Diagnostic_Clip/Rev. 0/Pictures/0349_-_Test_page2.JPG

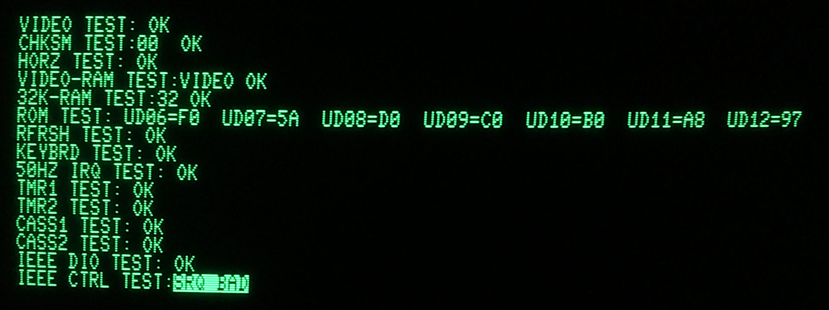
PET_Diagnostic_Clip/Rev. 0/Pictures/0349_-_Test_page2.JPG
