svenpetersen1965/PET-Diagnostic-Clip/CBM8296_Harness/CBM8296 Diagnostic User Port Dongle/Rev. 0/pdf/8296diag_UP_v0_prelim.pdf

# Project Documentation

## Commodore CBM8296 Diagnostic: User Port Dongle

## Project number: 209

## Revision: 0

## Date: 16.05.2023

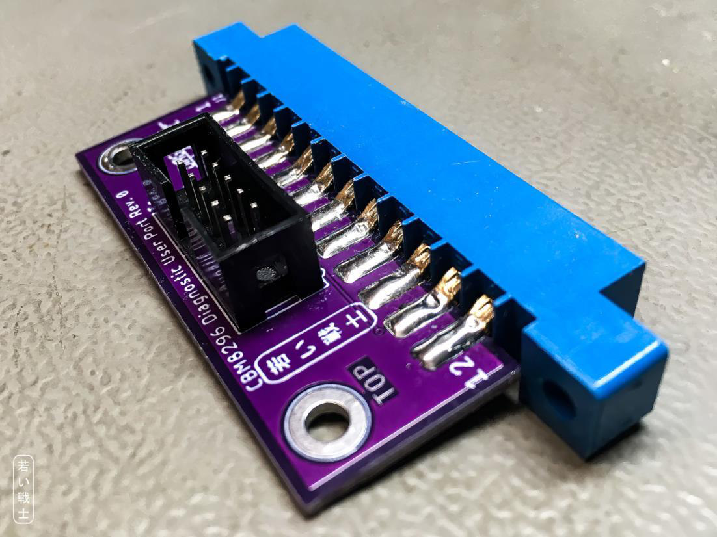
[picture p199: figure]

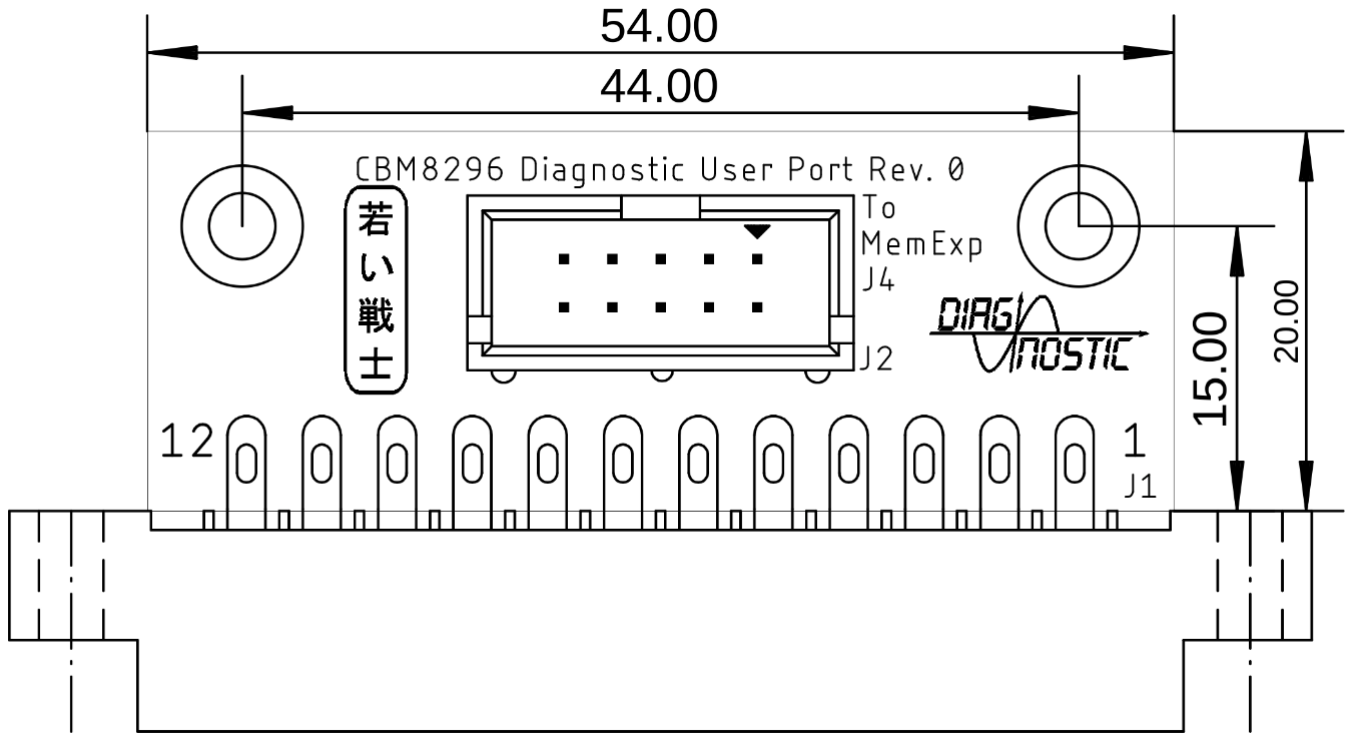
[picture p200: figure]

8296diag_UP_ModD.docx | | 11.06.2023 20:48
Drafted by Sven Petersen | Page 1 of 4 | Doc.-No.: 209-6-01-00

### Commodore CBM8296 Diagnostic: User Port Dongle Rev. 0

### Module Description

## Introduction

This User Port Dongle is part of the diagnostic clip set for the Commodore CBM8296. The original 324805-01 part incorporated a connector for the J4 memory expansion pin header. This dongle has a 2x5 box connector, which attaches to the J4 breakout board (project number 210) via a ribbon cable.

Figure 1: Dimensions of the User Port Dongle

## Connections

Connection Signals
B - M | CA1 - CB2
C - J4.13 | PA0 - RAMSELA
D - J4.14 | PA1 - RAMON
E - J4.12 | PA2 - RAMSEL9

## Soldering The Edge Connector

To provide a defined position of the edge connector, it is recommended to solder it flat on the bottom side of the PCB. Then bending the top solder latches towards the board on the top side, so that a part lays flat. A suitable tool for this is a screw driver or tweezers. Finally soldering the latches to the top solder pads while holding them down until the solder joint has cooled down. It is best to do this before any through hole component is installed.

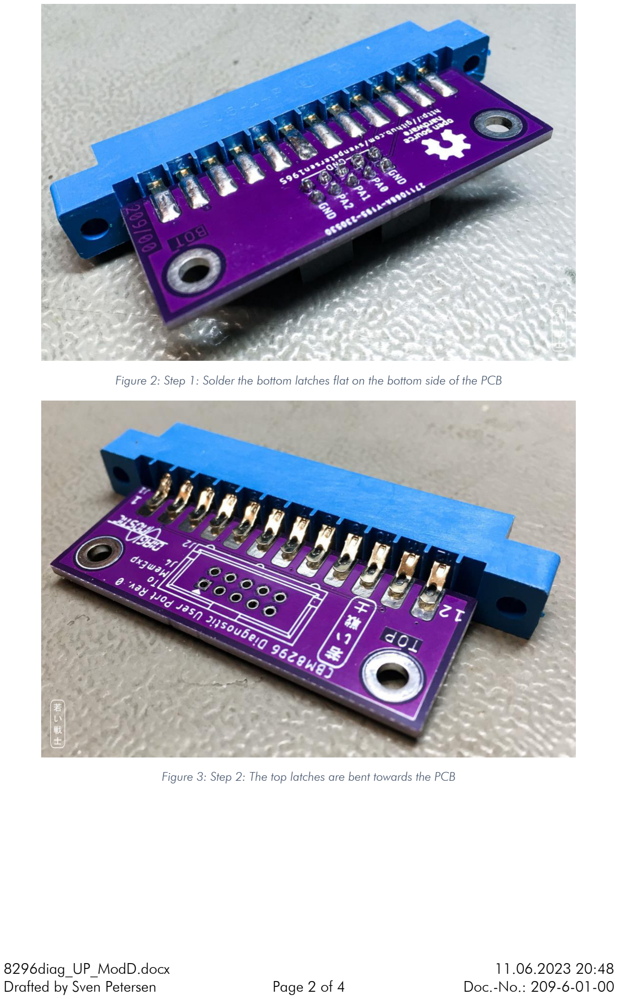
[picture p201: page 3]

8296diag_UP_ModD.docx | | 11.06.2023 20:48
Drafted by Sven Petersen | Page 2 of 4 | Doc.-No.: 209-6-01-00

Figure 2: Step 1: Solder the bottom latches flat on the bottom side of the PCB

Figure 3: Step 2: The top latches are bent towards the PCB

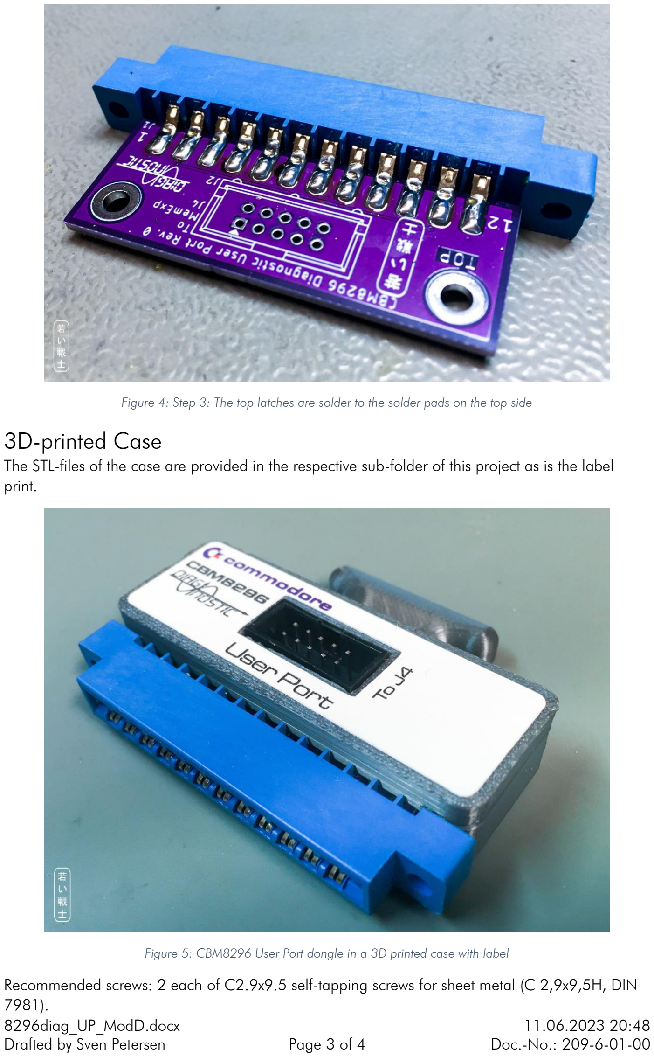
[picture p202: page 4]

8296diag_UP_ModD.docx | | 11.06.2023 20:48
Drafted by Sven Petersen | Page 3 of 4 | Doc.-No.: 209-6-01-00

Figure 4: Step 3: The top latches are solder to the solder pads on the top side

## 3D-printed Case

The STL-files of the case are provided in the respective sub-folder of this project as is the label print.

Figure 5: CBM8296 User Port dongle in a 3D printed case with label

Recommended screws: 2 each of C2.9x9.5 self-tapping screws for sheet metal (C 2,9x9,5H, DIN 7981).

8296diag_UP_ModD.docx | | 11.06.2023 20:48
Drafted by Sven Petersen | Page 4 of 4 | Doc.-No.: 209-6-01-00

## Revision History

### Rev. 0

- Prototype, not yet tested.

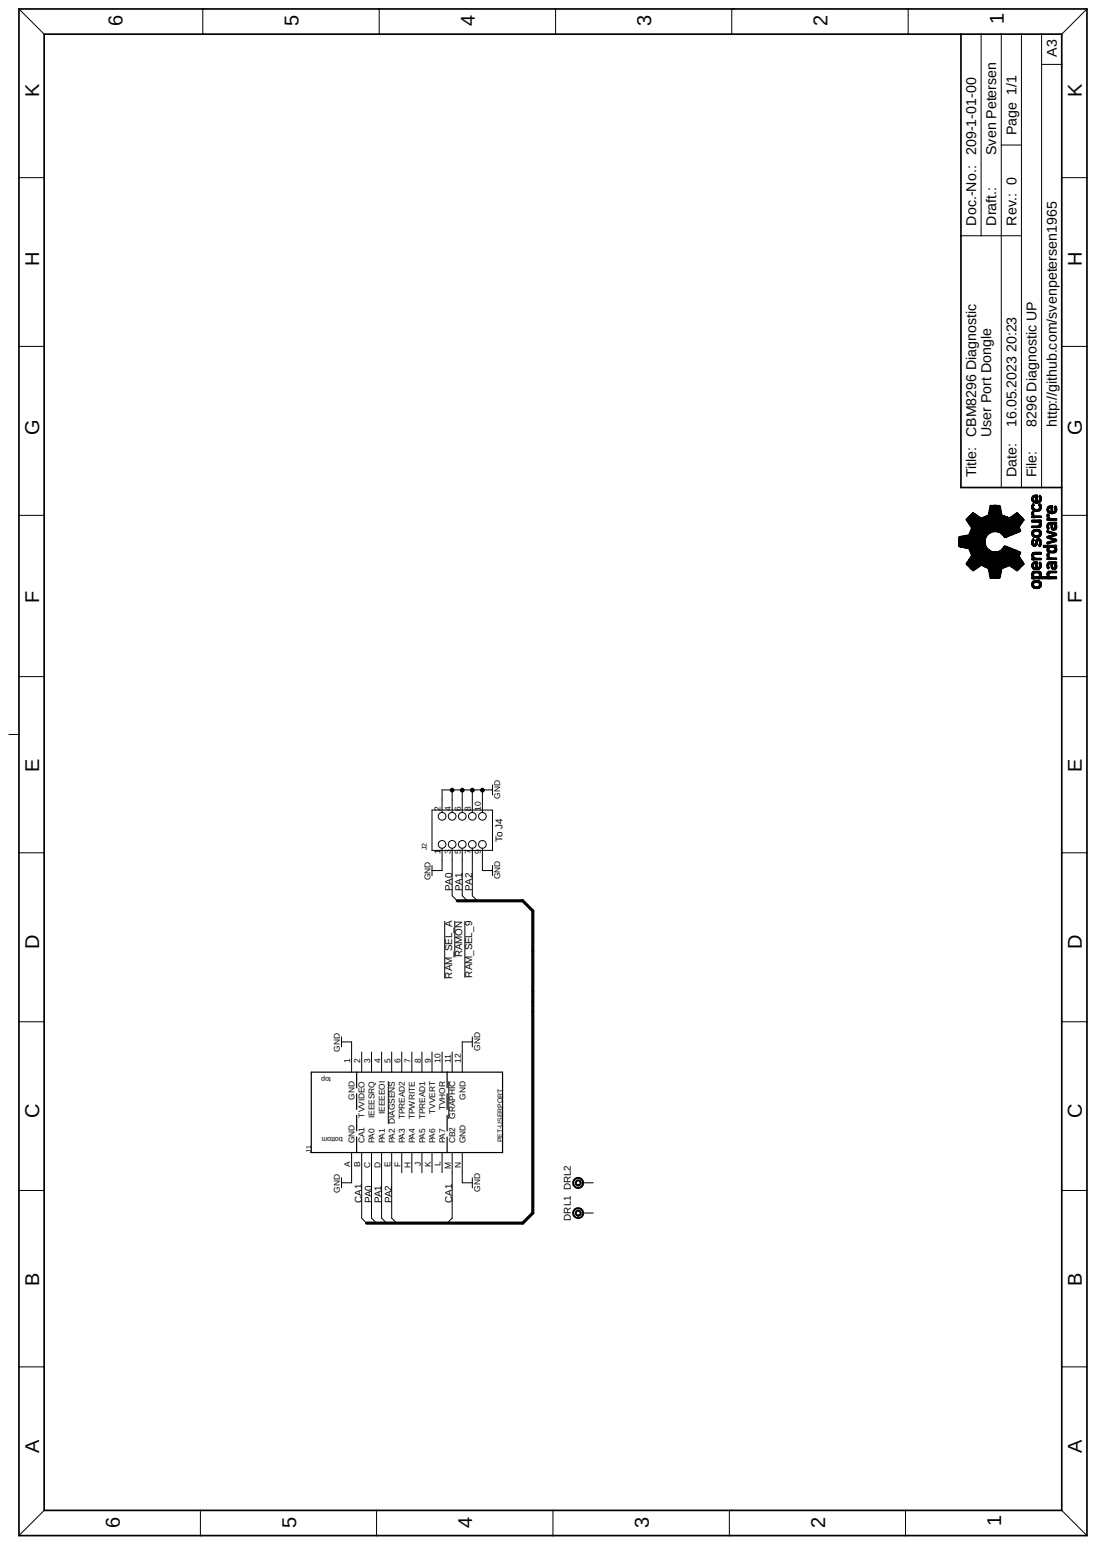
[picture p203: page 6]
PET-USERPORT; GND GND; GNDGND; GND; CBM8296 Diagnostic; Sven Petersen; RAM_SEL_A; RAMON; RAM_SEL_9; GND 1; TVVIDEO 2; IEEESRQ 3; IEEEEOI 4; TPREAD2 6; TPWRITE 7; TVVERT 9; TVHOR 10; DIAGSENS 5; GRAPHIC 11; GND 12; GND A CA1 B PA0 C; GND N; TPREAD1 8; DRL1 DRL2; Title:; Date:; Draft.:; Page; KHGFEDCBA; File:; Doc.-No.:; Rev.: 1/1 16.05.2023 20:23; 8296 Diagnostic UP

http://github.com/svenpetersen1965

User Port Dongle

## Sven Petersen 2023

209-2-01-00

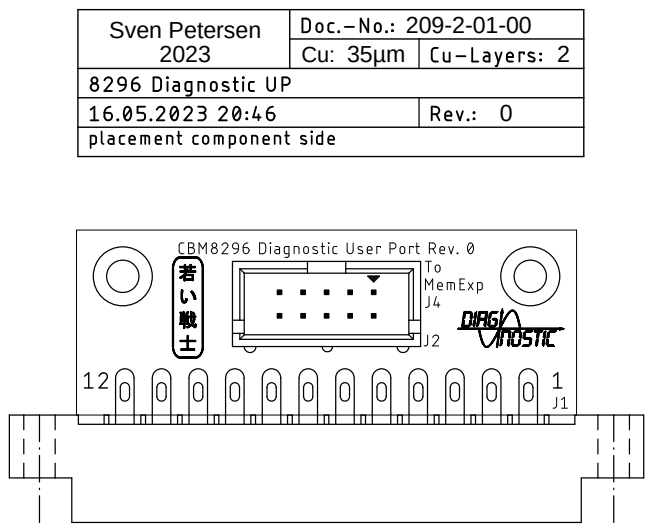
[picture p204: page 7]

2023

35µm | 2

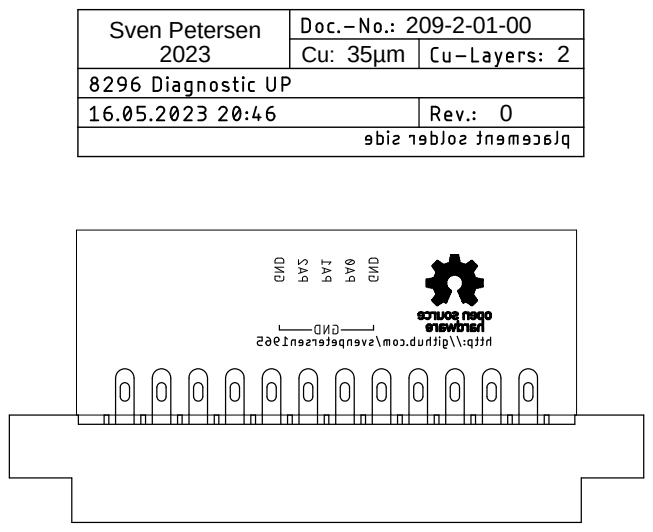
[picture p205: page 8]

2023

35µm | 2

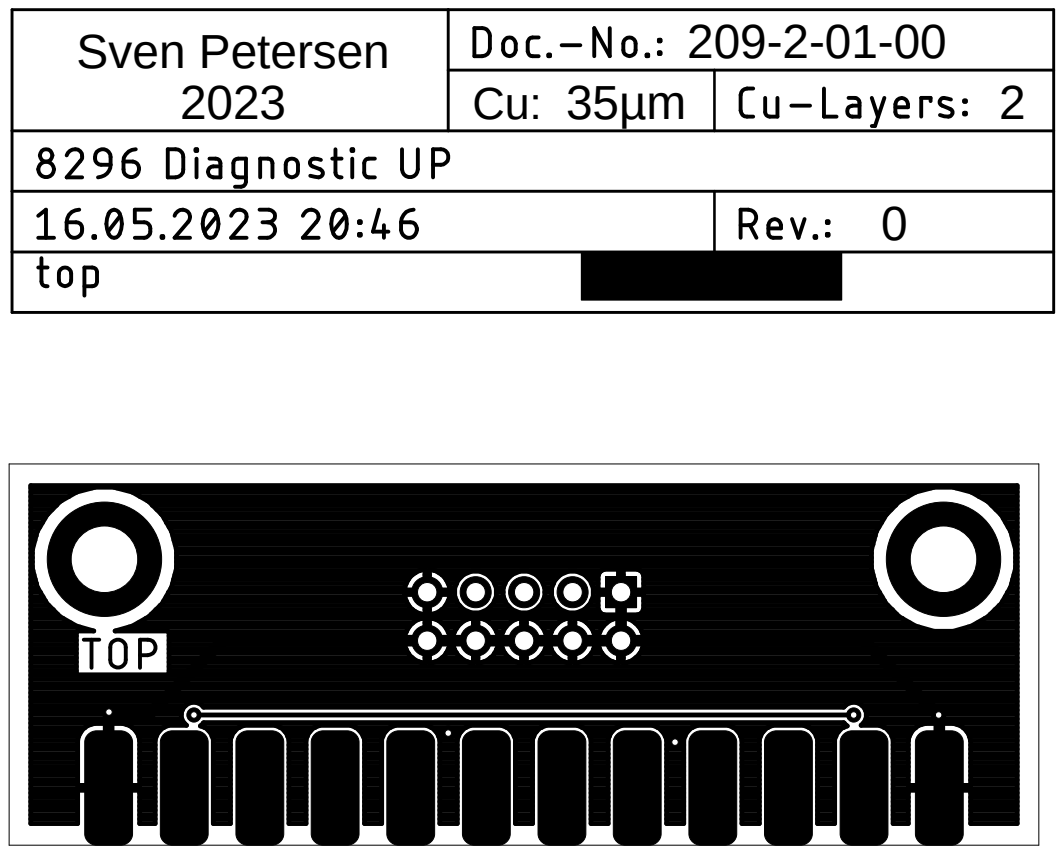
[picture p206: page 9]

2023

35µm | 2

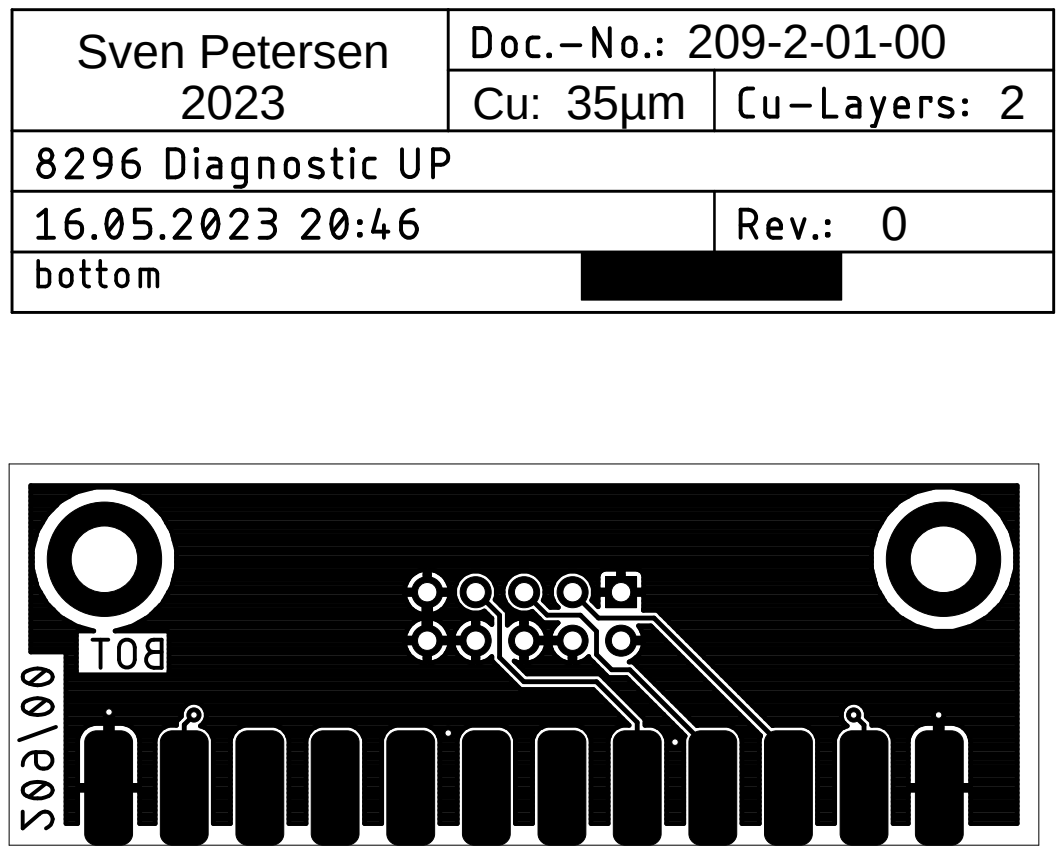
[picture p207: page 10]

2023

35µm | 2

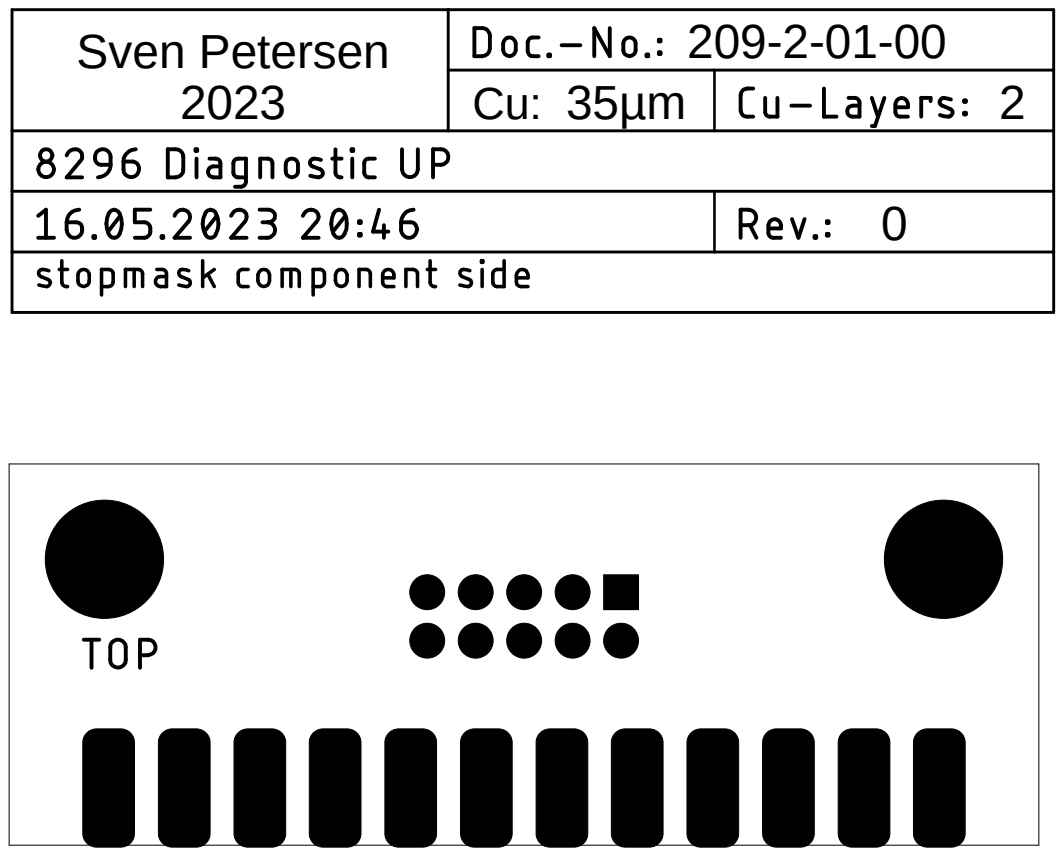
[picture p208: page 11]

2023

35µm | 2

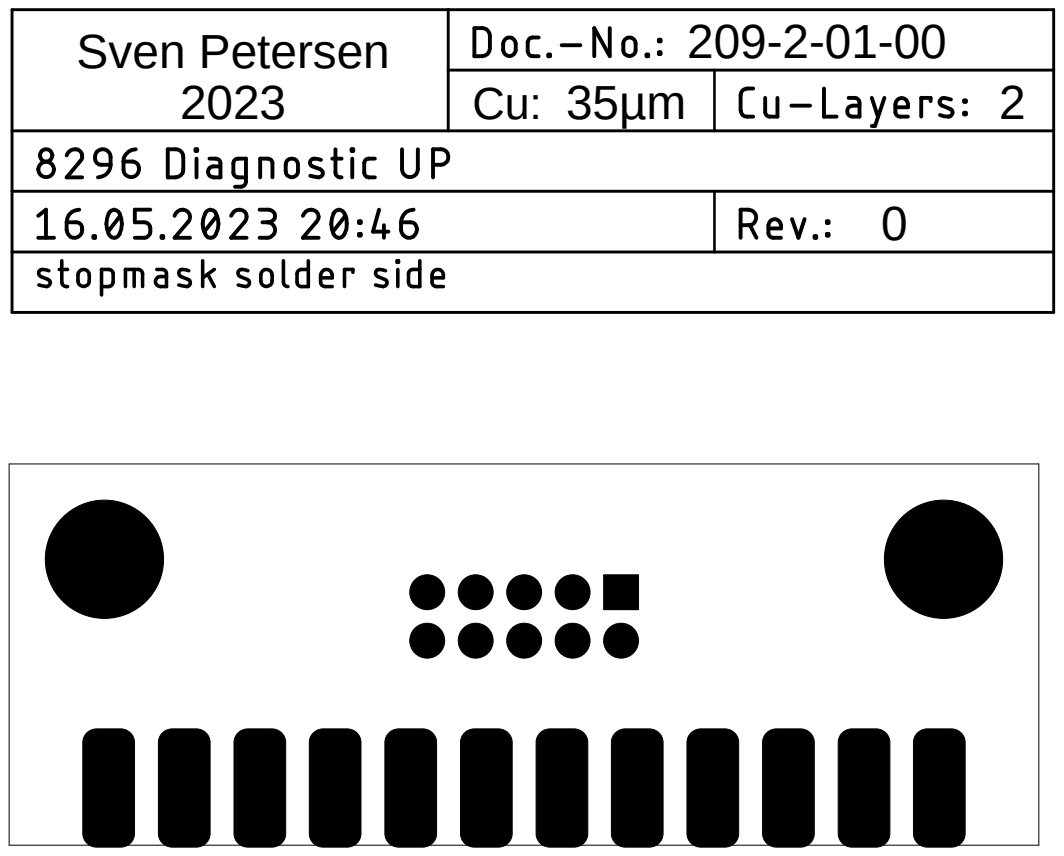
[picture p209: page 12]

54.00
44.00

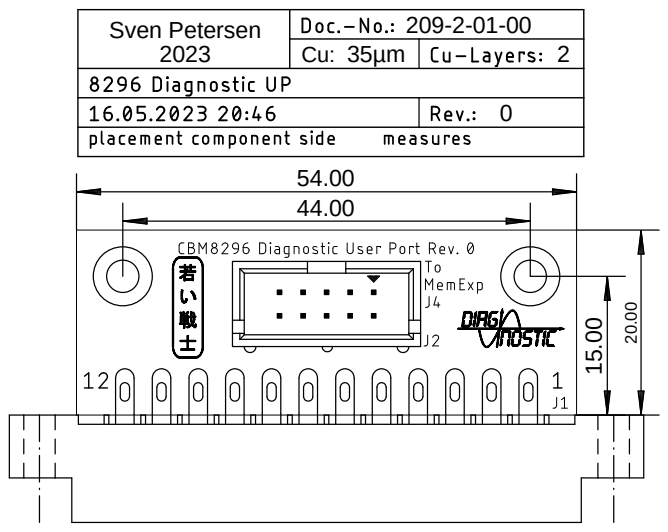
[picture p210: page 13]

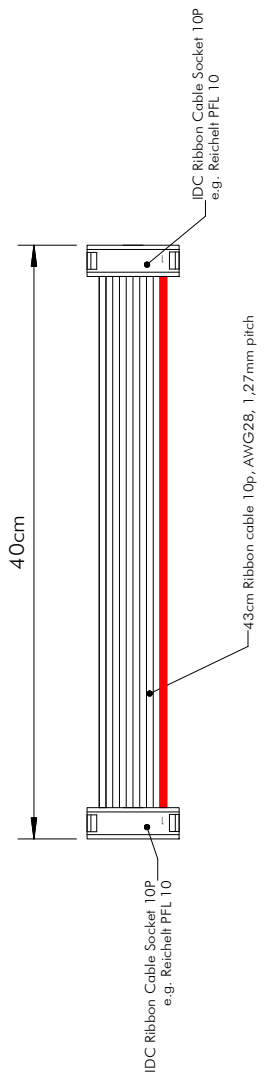
[picture p211: page 14]
e.g. Reichelt PFL 10; UP-J4.SKF; User Port - J4; File:; Titel:; Doc.-No.: 209-3-01-00; Date: 18.05.2023 12:42; Diagnostic 586220; Harness; Rev.: 0

Draft.: Sven Petersen

IDC Ribbon Cable Socket 10P

Breakout Board Cable

43cm Ribbon cable 10p, AWG28, 1,27mm pitch

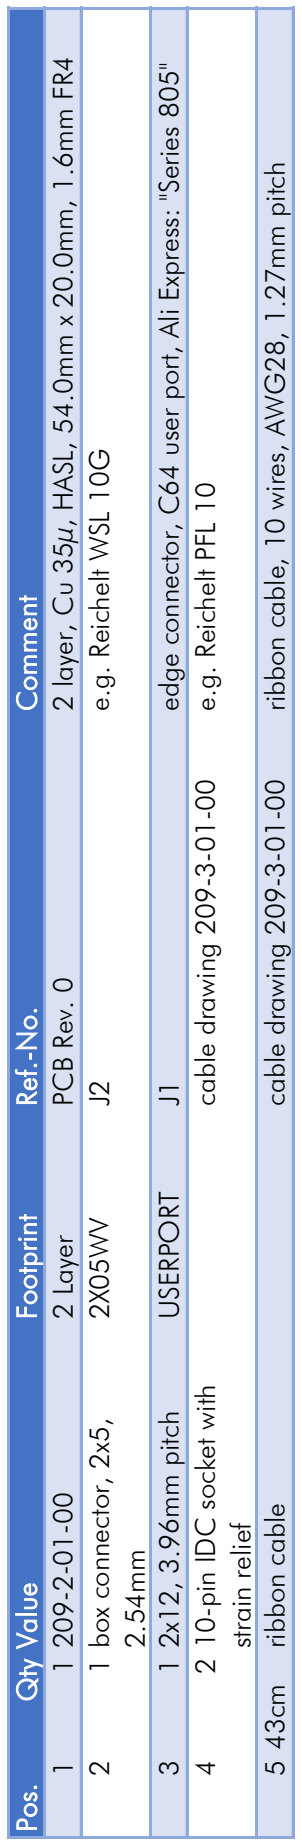
[picture p212: figure]
2 1 box connector, 2x5,; 2X05WV J2 e.g. Reichelt WSL 10G; 4 2 10-pin IDC socket with; strain relief

Pos. Qty Value Footprint Ref.-No. Comment

1 1 209-2-01-00 2 Layer PCB Rev. 0 2 layer, Cu 35µ, HASL, 54.0mm x 20.0mm, 1.6mm FR4 3 1 2x12, 3.96mm pitch USERPORT J1 edge connector, C64 user port, Ali Express: "Series 805"

cable drawing 209-3-01-00 e.g. Reichelt PFL 10

5 43cm ribbon cable cable drawing 209-3-01-00 ribbon cable, 10 wires, AWG28, 1.27mm pitch

## Commodore CBM8296 Diagnostic: User Port Dongle Rev. 0

## Bill of Material Rev. 0.0

8296diag_UP_BOM_v0_0.xlsx

Drafted by Sven Petersen Page 1 of 1

18.05.2023 12:47
Doc.No.: 209-5-01-00.0
