svenpetersen1965/PET-Diagnostic-Clip/CBM8296_Harness/CBM8296 Diagnostic User Port Dongle/Rev. 0/pdf/UP-J4.pdf

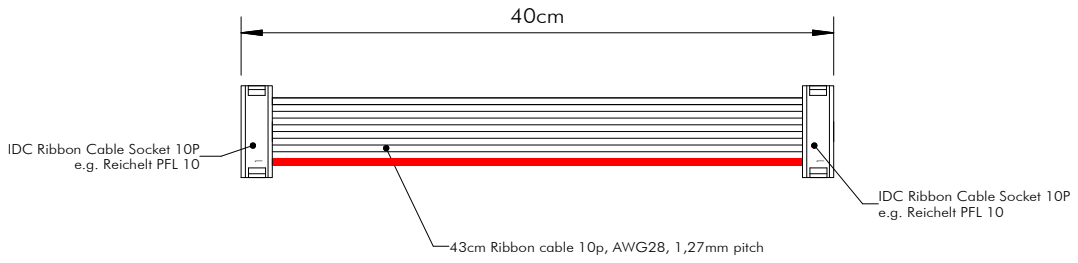
[picture p213: page 1]
e.g. Reichelt PFL 10; File:; Titel:; Doc.-No.: 209-3-01-00; Date: 18.05.2023 12:42; Diagnostic 586220 Harness

IDC Ribbon Cable Socket 10P

e.g. Reichelt PFL 10

43cm Ribbon cable 10p, AWG28, 1,27mm pitch

User Port - J4
Breakout Board Cable

Draft.: Sven Petersen
UP-J4.SKF
Rev.: 0
