svenpetersen1965/PET-Diagnostic-Clip/CBM8296_Harness/CBM8296 Diagnostic Keyboard Dongle/Rev. 0/pdf/8296diag_KB_v0_prelim.pdf

# Project Documentation

## Commodore CBM8296 Diagnostic: Keyboard Dongle

## Project number: 212

## Revision: 0

## Date: 16.05.2023

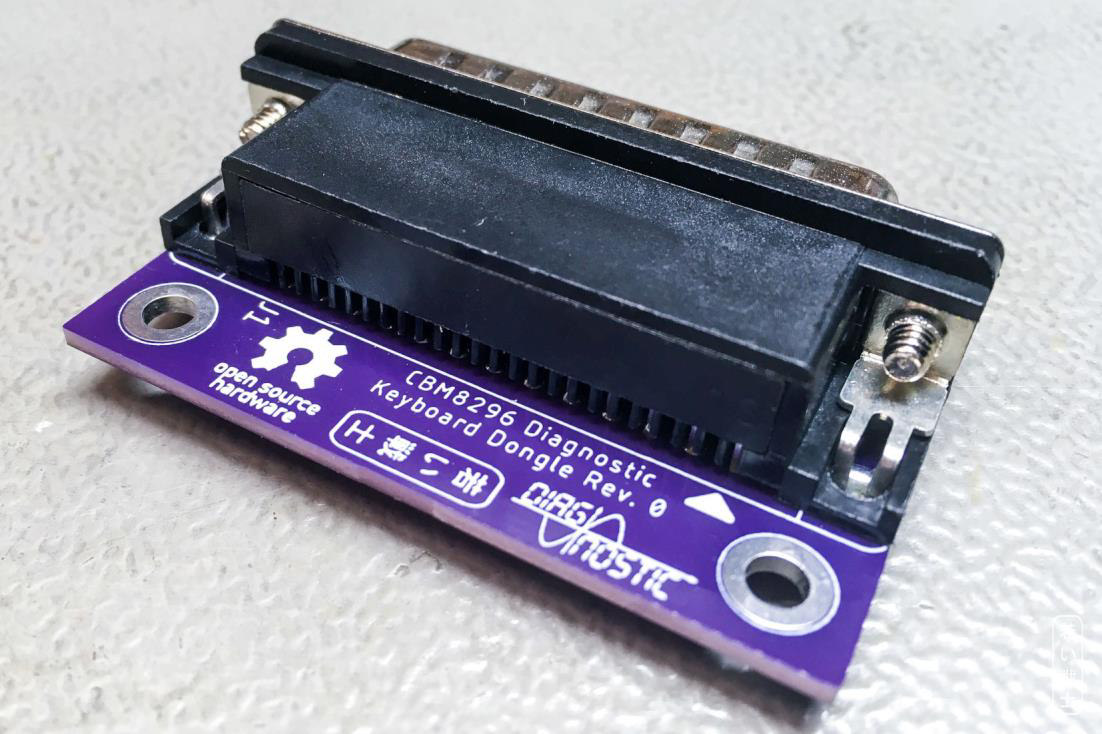
[picture p214: figure]

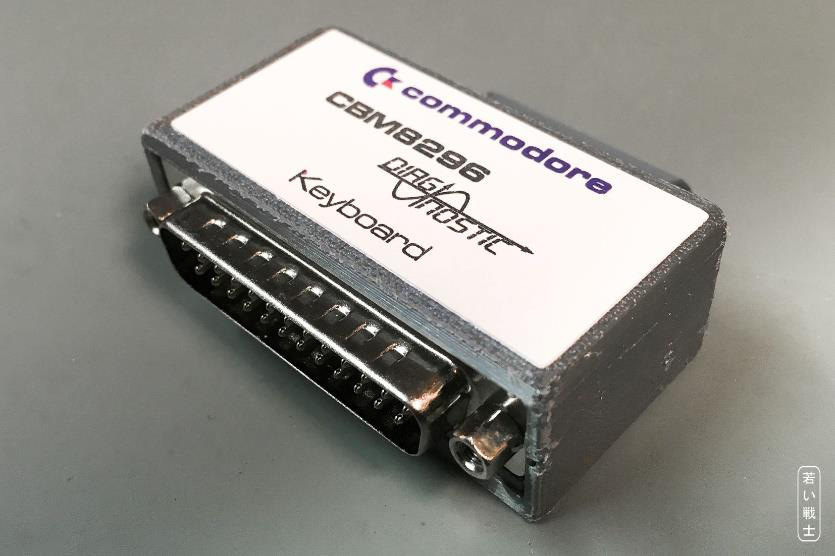
[picture p215: figure]

8296diag_KB_ModD.docx | | 11.06.2023 21:02
Drafted by Sven Petersen | Page 1 of 2 | Doc.-No.: 212-6-01-00

### Commodore CBM8296 Diagnostic: Keyboard Dongle Rev. 0

### Module Description

## Introduction

This Keyboard Dongle is part of the diagnostic clip set for the Commodore CBM8296. The original Commodore part number is 324803-01. The feedback signals are directly wired to a D-Sub connector (25 pins, male). This Keyboard Dongle is based on a PCB.

Figure 1: Dimensions of the Keyboard Dongle

## 3D-printed Case

The STL-files of the case are provided in the respective sub-folder of this project as is the label print.

Figure 2: CBM8296 User Port dongle in a 3D printed case with label

Recommended screws: 2 each of C2.9x6.5 self-tapping screws for sheet metal (C 2,9x6,5H, DIN 7981).

8296diag_KB_ModD.docx | | 11.06.2023 21:02
Drafted by Sven Petersen | Page 2 of 2 | Doc.-No.: 212-6-01-00

## Connections

Connection Signals
1-9-14 | DEC0 – DEC8 – KIN0
2-10-15 | DEC1 – DEC9 – KIN1
3-16 | DEC2 – KIN2
4-17 | DEC3 – KIN3
5-18 | DEC4 – KIN4
6-19 | DEC5 – KIN5
7-20 | DEC6 – KIN6
8-21 | DEC7 - KIN7

## Revision History

### Rev. 0

- Prototype, not yet tested.

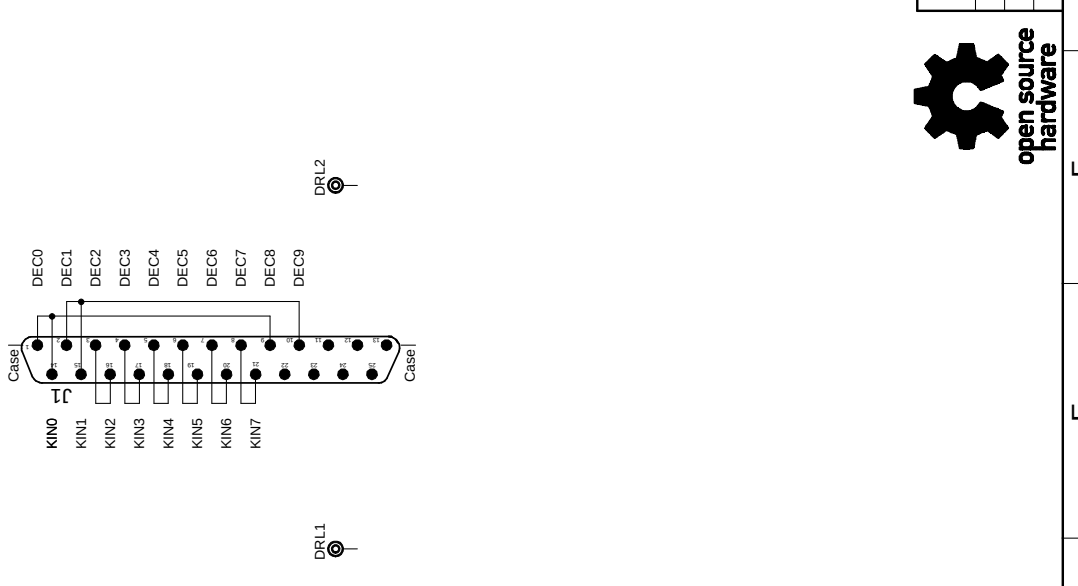
[picture p216: page 4]
CBM8296 Diagnostic; Keyboard Dongle; Sven Petersen; DEC0; DEC1; DEC2; DEC3; DEC4; DEC5; DEC6; DEC7; DEC8; DEC9; KIN0; KIN1; KIN2; KIN3; KIN4; KIN5; KIN6; KIN7; DRL1 DRL2; Title:; Date:; Draft.:; Page; KHGFEDCBA; File:; Doc.-No.:; Rev.: 1/1 19.05.2023 20:11; 8296_diag_KB; Case

http://github.com/svenpetersen1965

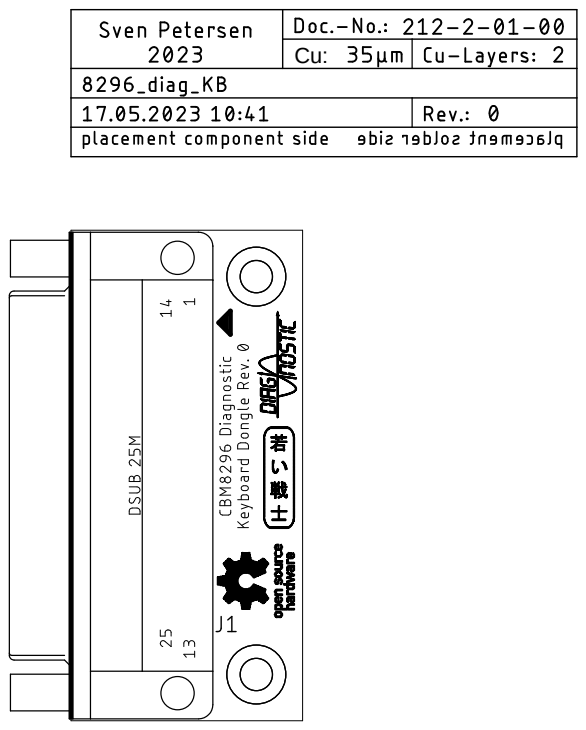
[picture p217: page 5]

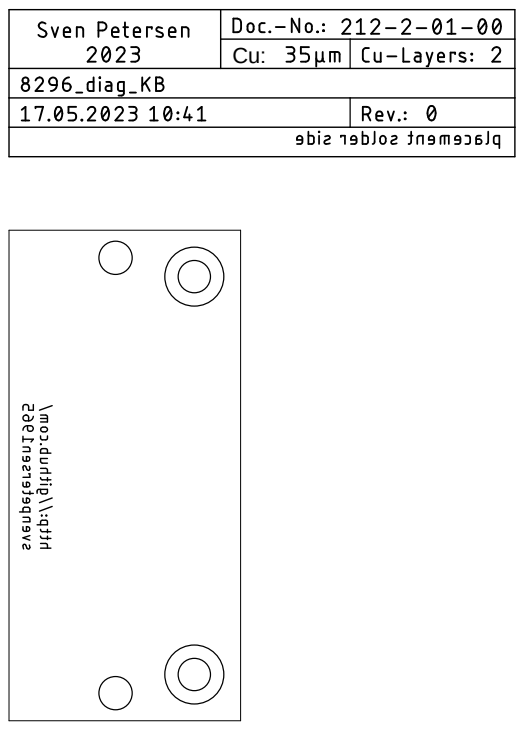
[picture p218: page 6]

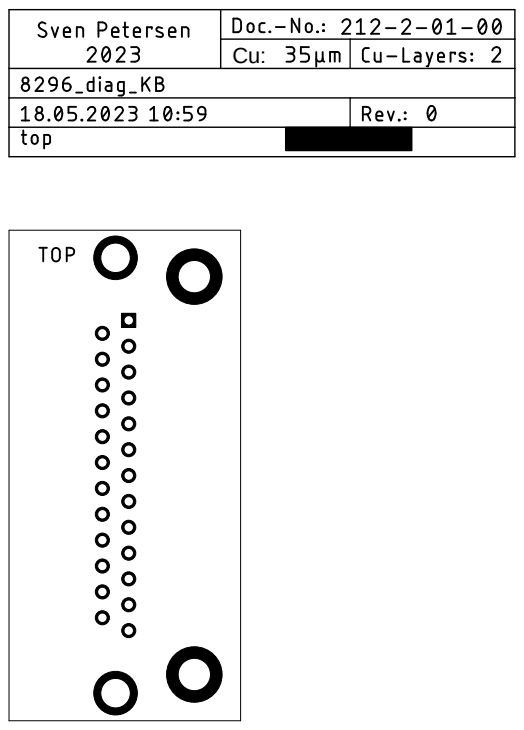
[picture p219: page 7]

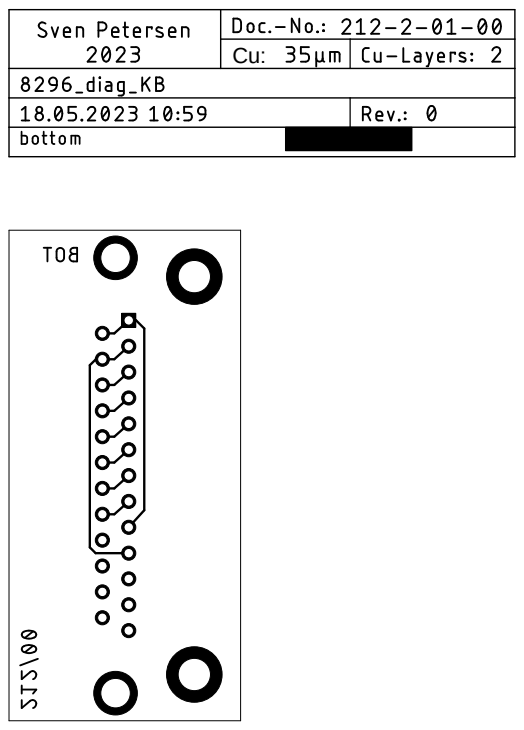
[picture p220: page 8]

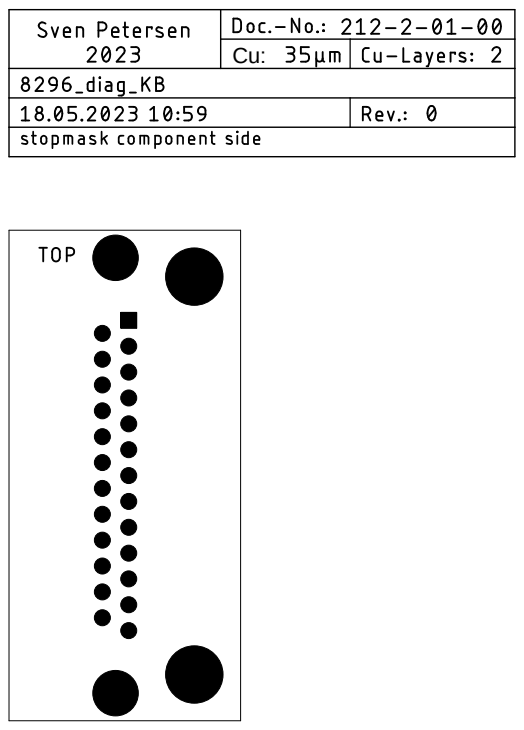
[picture p221: page 9]

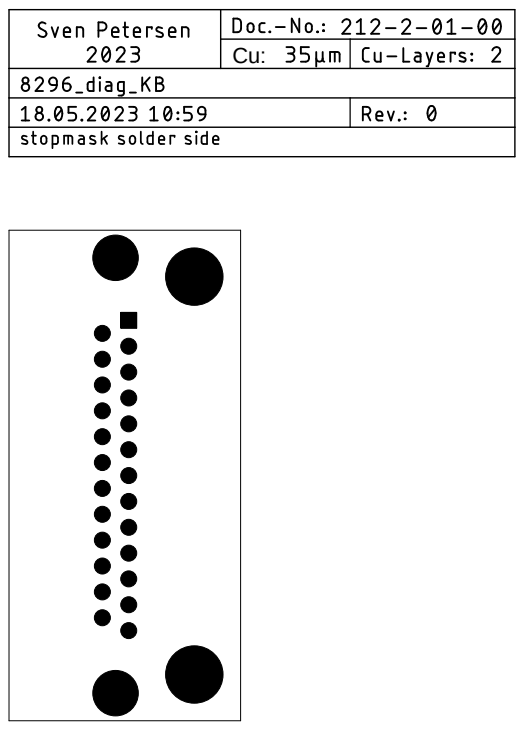
[picture p222: page 10]

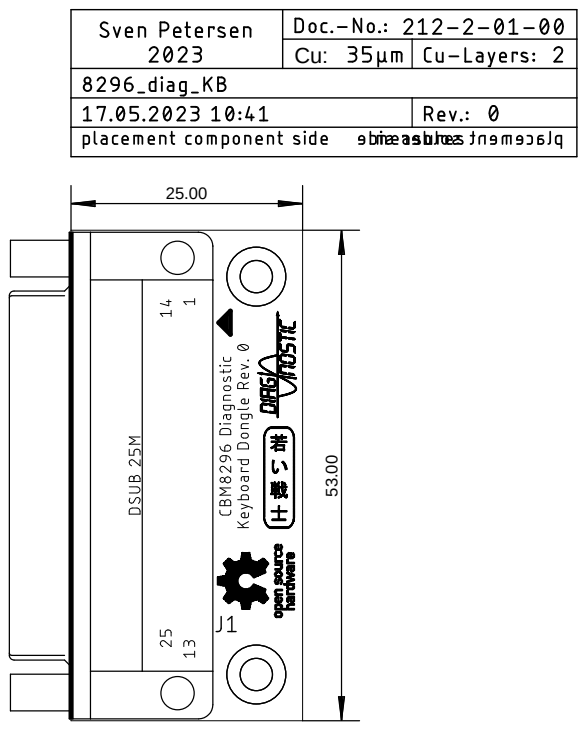
[picture p223: page 11]

Pos. Qty Value Footprint Ref.-No. Comment

1 1 212-2-01-00 2 Layer PCB Rev. 0 2 layer, Cu 35µ, HASL, 53.0 x 25.0, 1.6mm FR4

2 1 D-Sub 25 male, 90°, PCB,

European

D25M90CLEU J1 e.g. Reichelt.de D-SUB ST 25EU

## Commodore CBM8296 Diagnostic: Keyboard Dongle Rev. 0

## Bill of Material Rev. 0.0

8296_KB_BOM_v0_0.xlsx

Drafted by Sven Petersen Page 1 of 1

19.05.2023 20:13
Doc.No.: 212-5-01-00.0
