svenpetersen1965/PET-Diagnostic-Clip/CBM8296_Harness/CBM8296 Diagnostic J4 Breakout Board/Rev. 0/pdf/8296diag_J4BrOut_v0_prelim.pdf

# Project Documentation

## Commodore CBM8296 Diagnostic: J4 Breakout Board

## Project number: 210

## Revision: 0

## Date: 16.05.2023

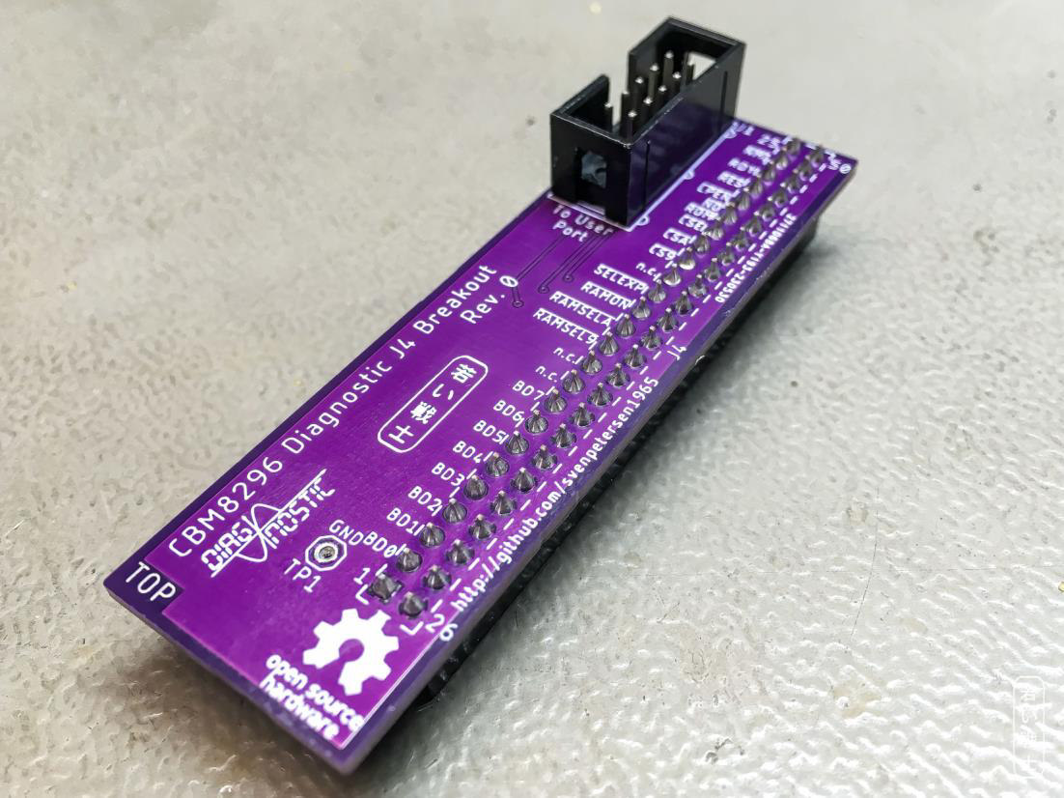
[picture p224: figure]

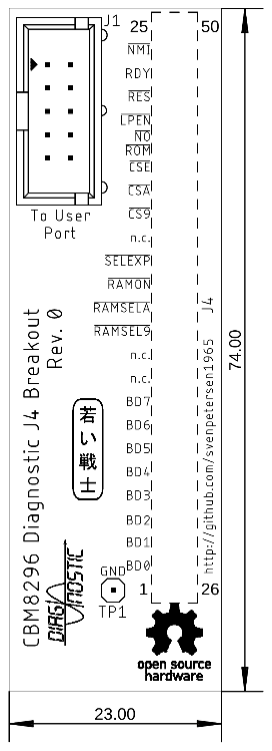
[picture p225: figure]

8296diag_J4BrOut_ModD.docx | | 11.06.2023 20:58
Drafted by Sven Petersen | Page 1 of 3 | Doc.-No.: 210-6-01-00

### Commodore CBM8296 Diagnostic: J4 Breakout Board Rev. 0

### Module Description

## Introduction

This J4 Breakout Board is part of the diagnostic clip set for the Commodore CBM8296. The original 324805-01 User Port Dongle incorporated a connector for the J4 memory expansion pin header. This breakout board has a 2x5 box connector, which attaches to the User Port Dongle (project number 209) of this diagnostic setup via a ribbon cable.

Figure 1: Dimensions of the J4 Breakout Board

TP1 is an optional test point, that could serve as a GND connection for measurements.

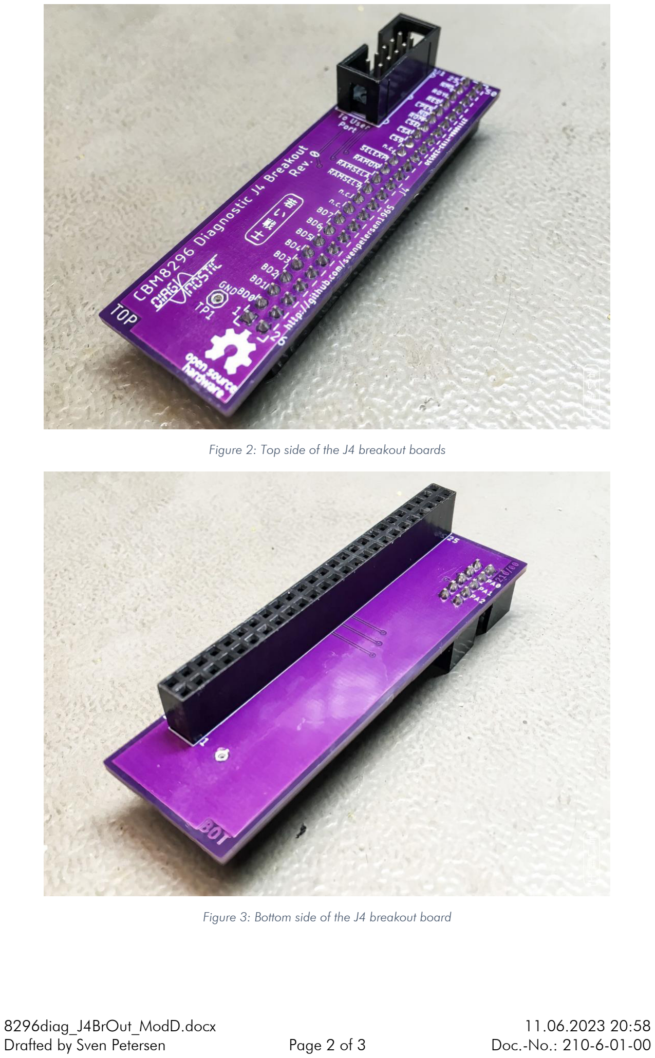
[picture p226: page 3]

8296diag_J4BrOut_ModD.docx | | 11.06.2023 20:58
Drafted by Sven Petersen | Page 2 of 3 | Doc.-No.: 210-6-01-00

Figure 2: Top side of the J4 breakout boards

Figure 3: Bottom side of the J4 breakout board

8296diag_J4BrOut_ModD.docx | | 11.06.2023 20:58
Drafted by Sven Petersen | Page 3 of 3 | Doc.-No.: 210-6-01-00

## Connections

Connection Signals
B - M | CA1 - CB2
C - J4.13 | PA0 - RAMSELA
D - J4.14 | PA1 - RAMON
E - J4.12 | PA2 - RAMSEL9

## Revision History

### Rev. 0

- Prototype, not yet tested.

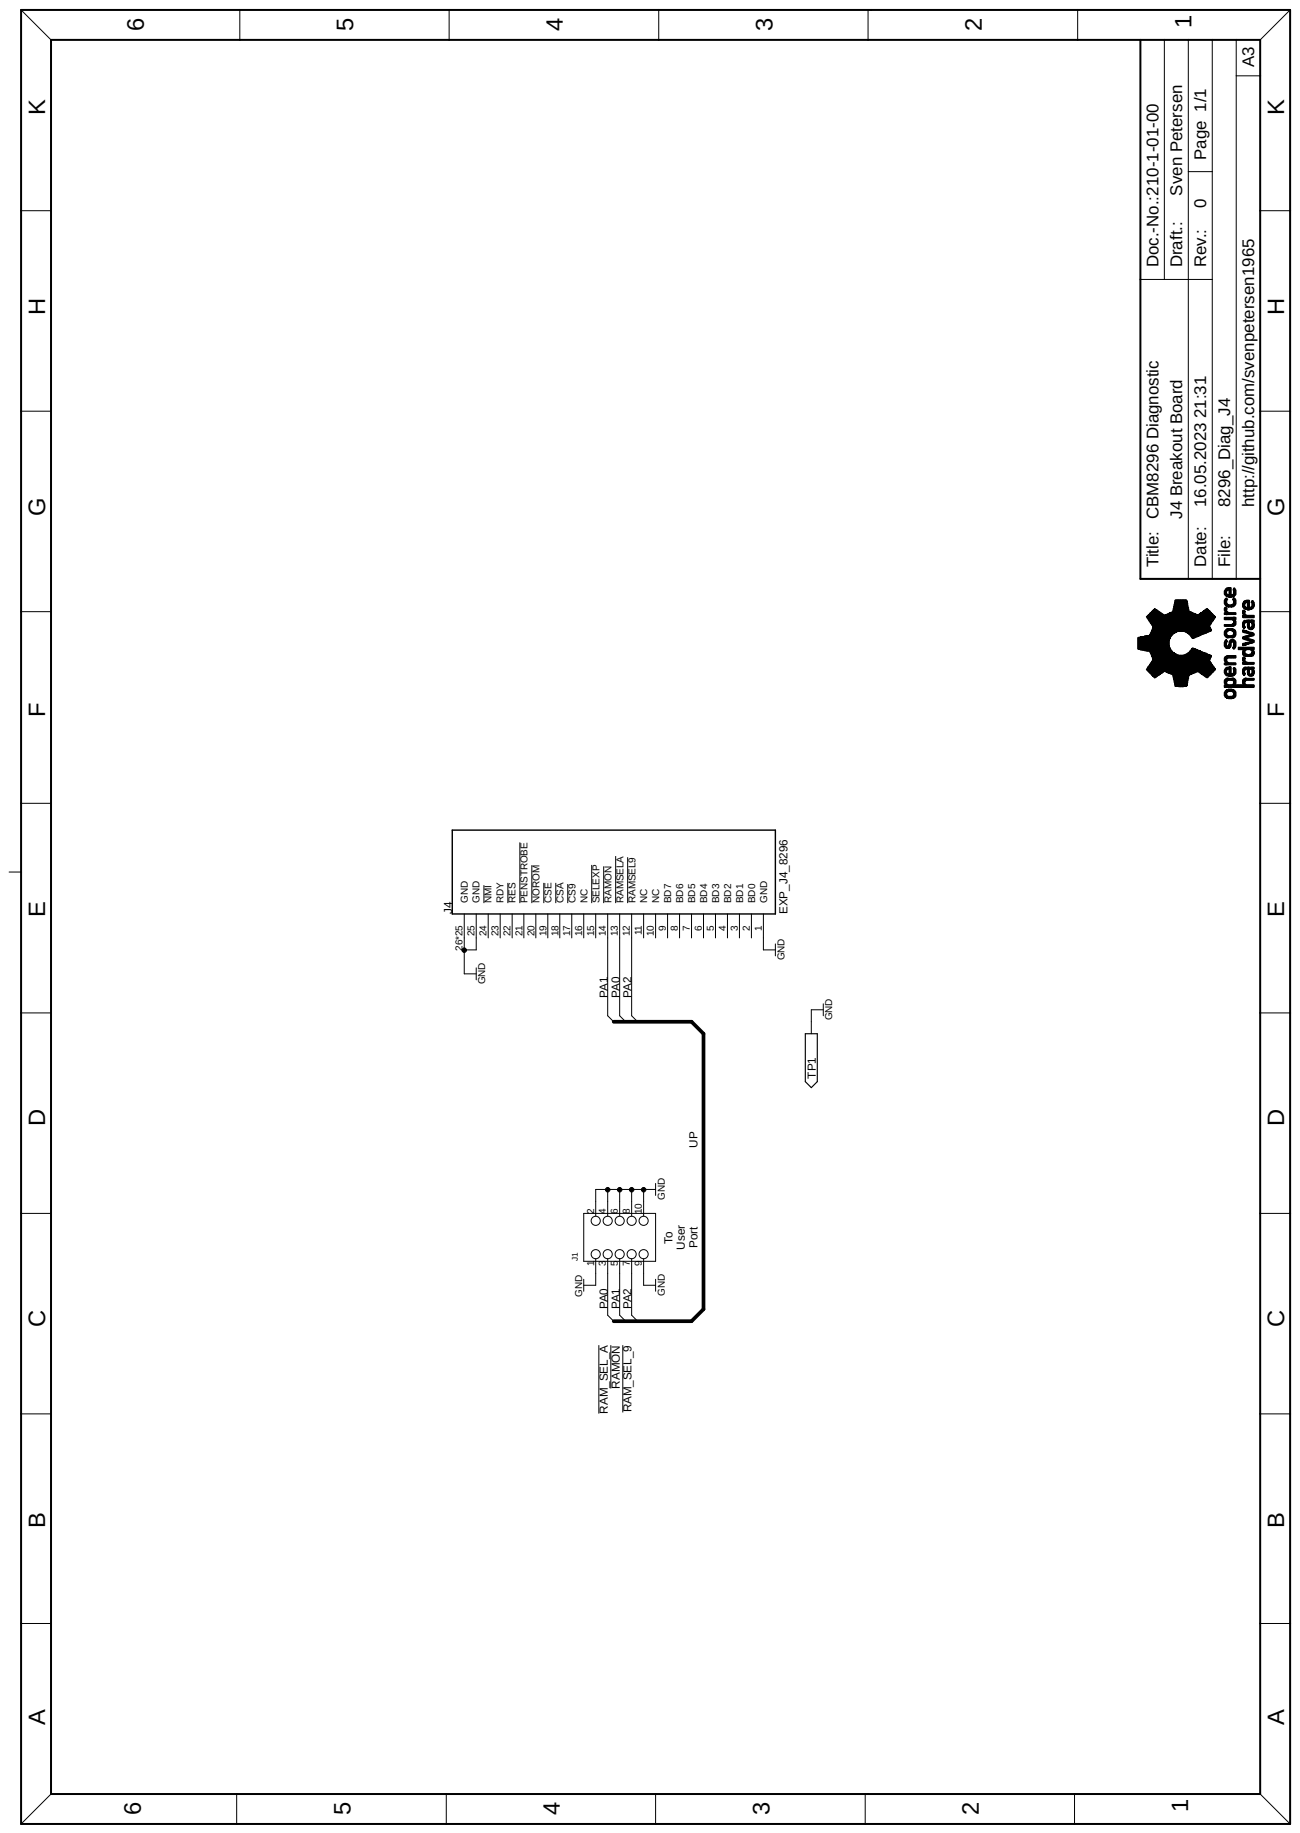
[picture p227: page 5]
GND; GND GND; CBM8296 Diagnostic; J4 Breakout Board; Sven Petersen; User; Port; RAM_SEL_A; RAMON; RAM_SEL_9; EXP_J4_8296; Title:; Date:; Draft.:; Page; KHGFEDCBA; File:; Doc.-No.:; Rev.: 1/1 16.05.2023 21:31; 8296_Diag_J4

http://github.com/svenpetersen1965

GND 1 BD0 2 BD1 3 BD2 4 BD3 5 BD4 6 BD5 7 BD6 8 BD7 9 NC 10 NC 11 RAMSEL9 12 RAMSELA 13 RAMON 14 SELEXP 15 NC 16 CS9 17 CSA 18 CSE 19 NOROM 20 PENSTROBE 21 RES 22 RDY 23 NMI 24 GND 25 GND 26*25

## Sven Petersen

2023

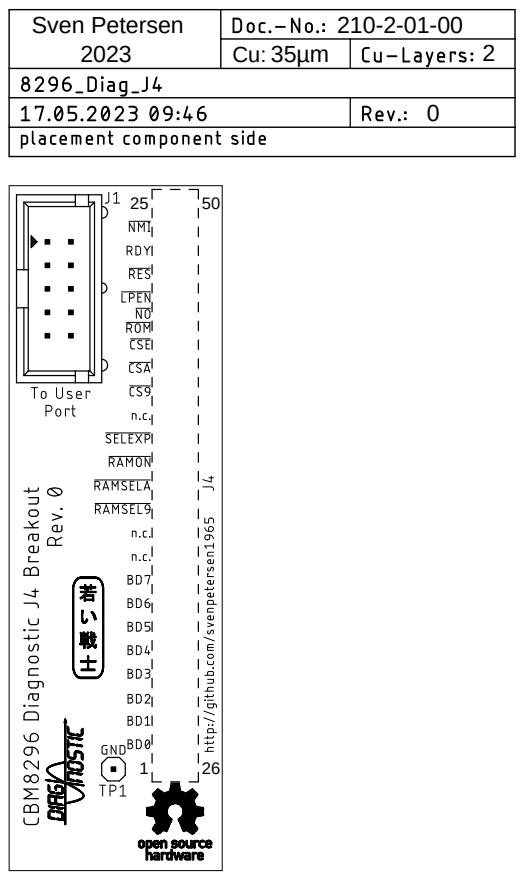
[picture p228: page 6]

2023

35µm | 2

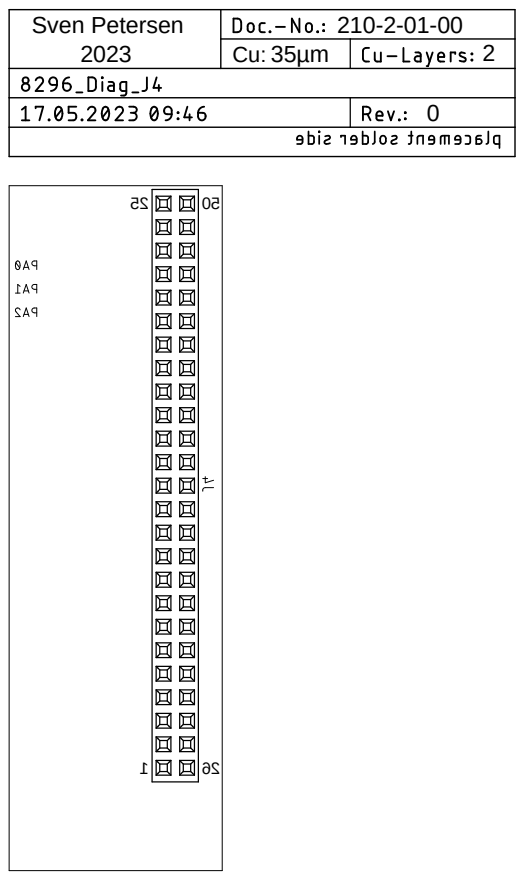
[picture p229: page 7]

2023

35µm | 2

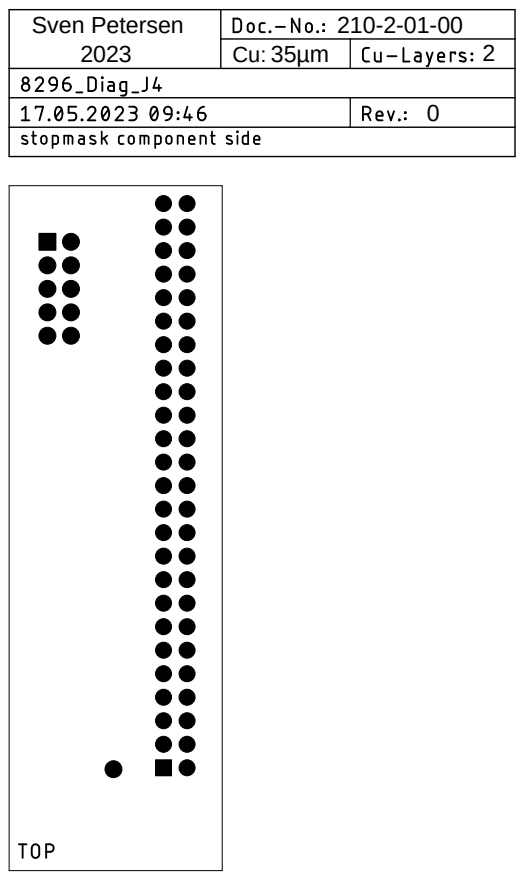
[picture p230: page 8]

2023

35µm | 2

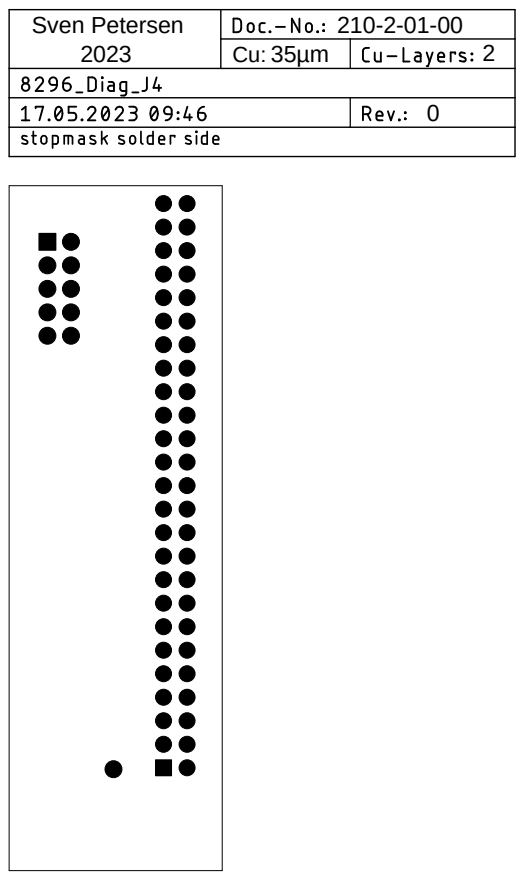
[picture p231: page 9]

2023

35µm | 2

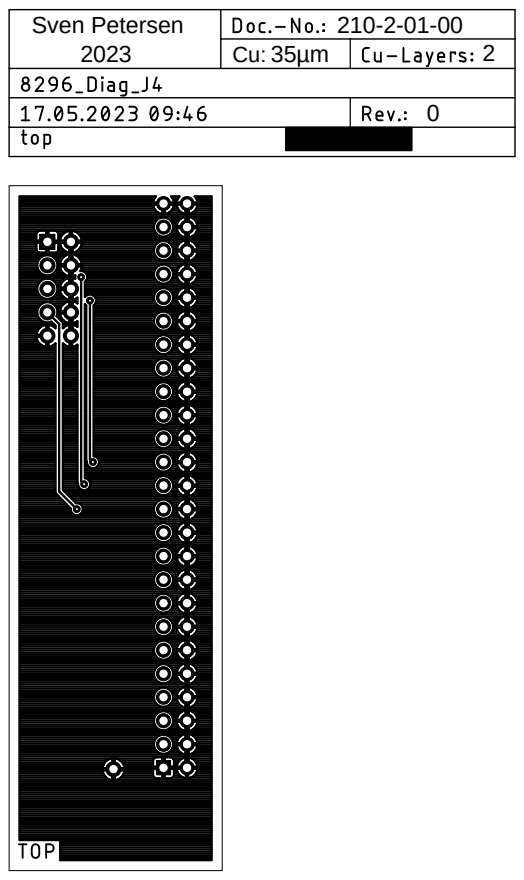
[picture p232: page 10]

2023

35µm | 2

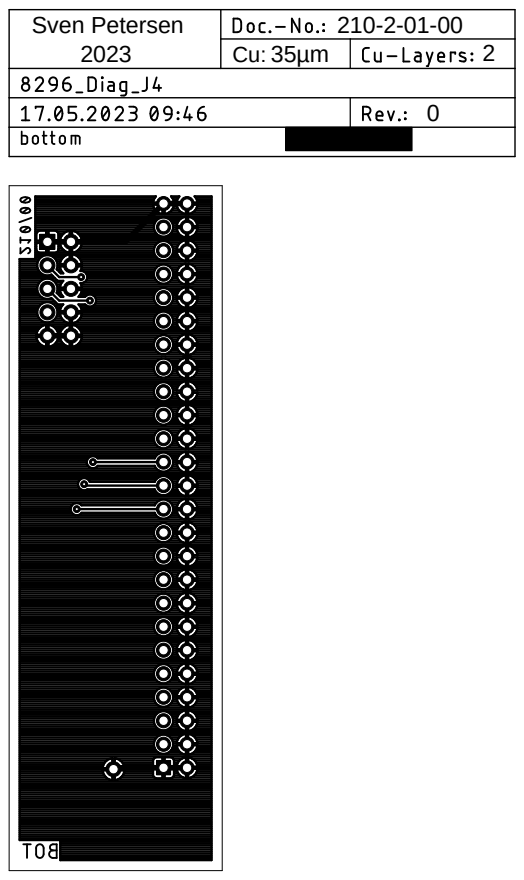
[picture p233: page 11]

2023

35µm | 2

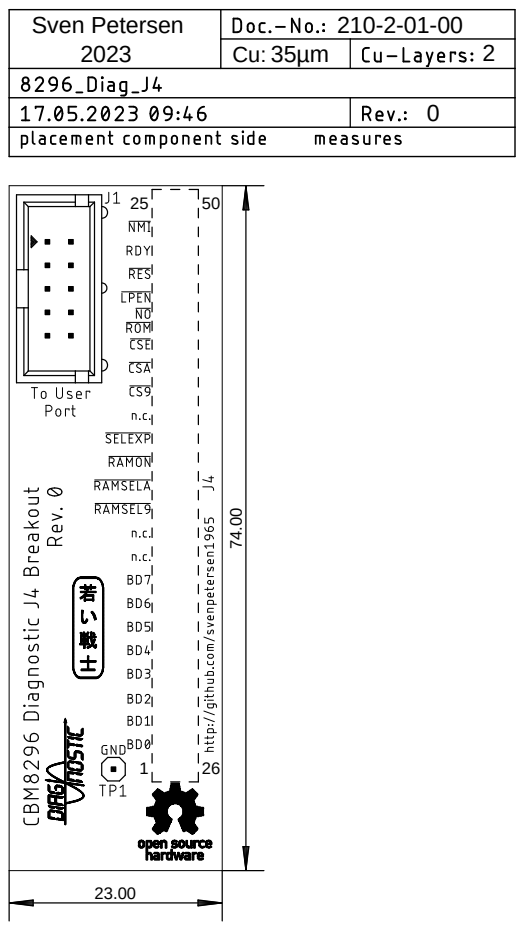
[picture p234: page 12]

Pos. Qty Value Footprint Ref.-No. Comment

1 1 210-2-01-00 2 Layer PCB Rev. 0 2 layer, Cu 35µ, HASL, 74.0 x 32.0, 1.6mm FR4

2 1 box connector, 2x5,

2.54mm

2X05WV J1 e.g. Reichelt WSL 10G

3 1 pin header, 1 pin 1X01 TP1 optional ground pin for debugging, e.g. Distrelec 300-93-

642 (RND 205-00622)

4 1 2x25 female, pitch

2.54mm

2x25 female J4 female socket connector for 0.65sq pins, 2x25 pins, pitch

2.54mm. E.g. MPE 094-2-050, e.g. Reichelt.de MPE 094-2-

050

## Commodore CBM8296 Diagnostic: J4 Breakout Board Rev. 0

## Bill of Material Rev. 0.0

8299diag_J4BrOut_BOM_v0_0.xlsx

Drafted by Sven Petersen Page 1 of 1

18.05.2023 12:05
Doc.No.: 210-5-01-00.0
