svenpetersen1965/PET-Diagnostic-Clip/CBM8296_Harness/CBM8296 Diagnostic Cassette Dongle/Rev. 0/pdf/8296diag_CP_v0_prelim.pdf

# Project Documentation

## Commodore CBM8296 Diagnostic: Cassette Dongle

## Project number: 211

## Revision: 0

## Date: 16.05.2023

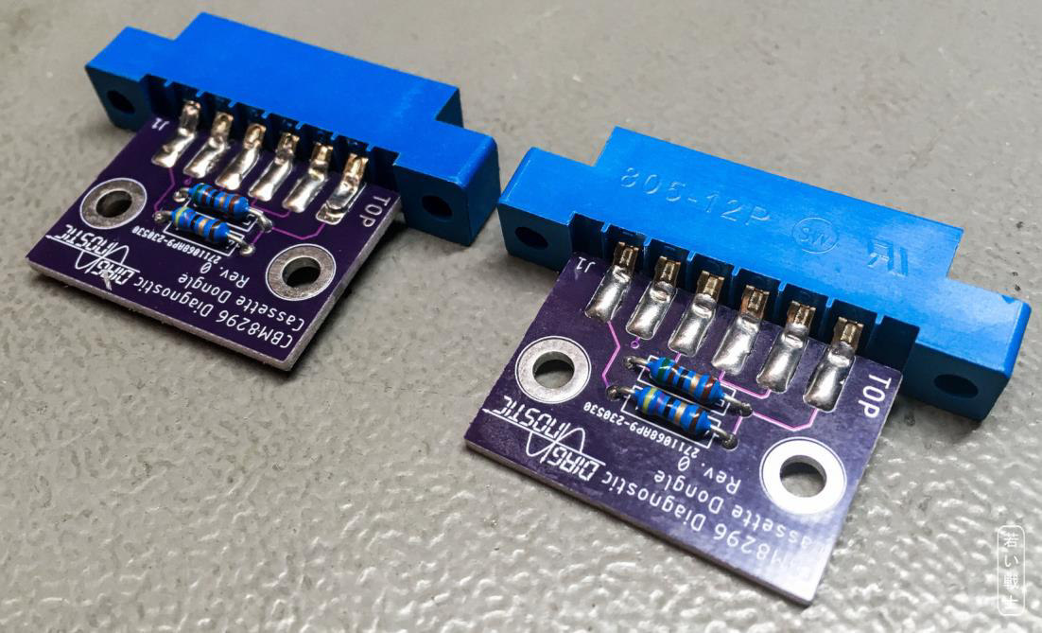
[picture p235: figure]


8296diag_CP_ModD.docx | | 11.06.2023 20:53
Drafted by Sven Petersen | Page 1 of 3 | Doc.-No.: 211-6-01-00

### Commodore CBM8296 Diagnostic: Cassette Dongle Rev. 0

### Module Description

## Introduction

This Cassette Dongle is part of the diagnostic clip set for the Commodore CBM8296. The original Commodore part number is 324804-01. The feedback signals are directly wired to an edge connector. This Cassette Dongle is based on a PCB.

The diagnostic setup requires two cassette dongles.

Figure 1: Dimensions of the Cassette Dongle

## Soldering The Edge Connector

To provide a defined position of the edge connector, it is recommended to solder it flat on the bottom side of the PCB. Then bending the top solder latches towards the board on the top side, so that a part lays flat. A suitable tool for this is a screw driver or tweezers. Finally soldering the latches to the top solder pads while holding them down until the solder joint has cooled down. It is best to do this before any through hole component is installed.

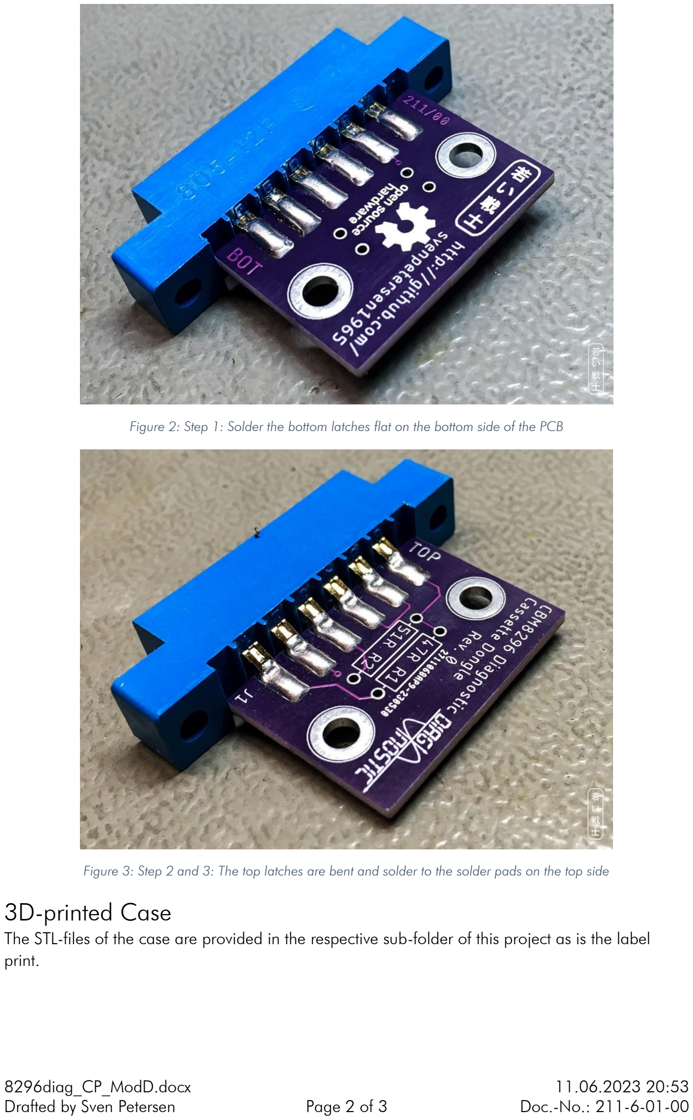
[picture p236: page 3]

8296diag_CP_ModD.docx | | 11.06.2023 20:53
Drafted by Sven Petersen | Page 2 of 3 | Doc.-No.: 211-6-01-00

Figure 2: Step 1: Solder the bottom latches flat on the bottom side of the PCB

Figure 3: Step 2 and 3: The top latches are bent and solder to the solder pads on the top side

## 3D-printed Case

The STL-files of the case are provided in the respective sub-folder of this project as is the label print.

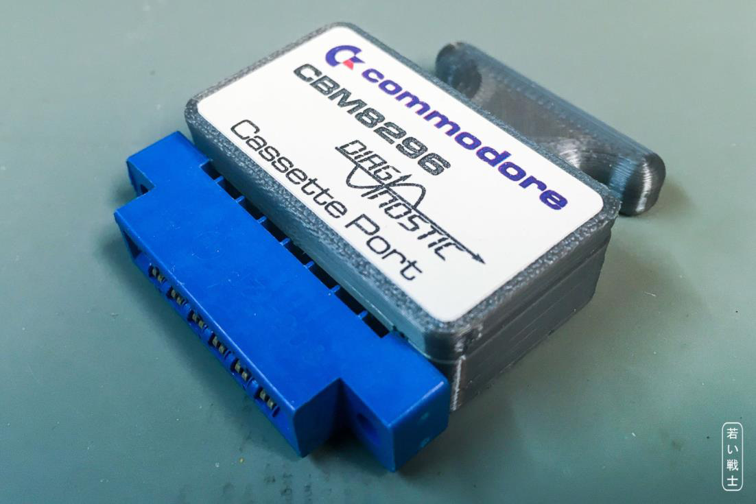
[picture p237: figure]

8296diag_CP_ModD.docx | | 11.06.2023 20:53
Drafted by Sven Petersen | Page 3 of 3 | Doc.-No.: 211-6-01-00

Figure 4: CBM8296 User Port dongle in a 3D printed case with label

Recommended screws: 2 each of C2.9x9.5 self-tapping screws for sheet metal (C 2,9x9,5H, DIN 7981).

## Connections

Connection | Signals
1 - (47Ω) - 6 | GND - SENSE
3 – (51Ω) - 6 | MOTOR - SENSE
4 - 5 | READ – WRITE

R1 and R2 serve as a voltage divider for the motor voltage (appr. 6V).

## Revision History

### Rev. 0

- Prototype, not yet tested.

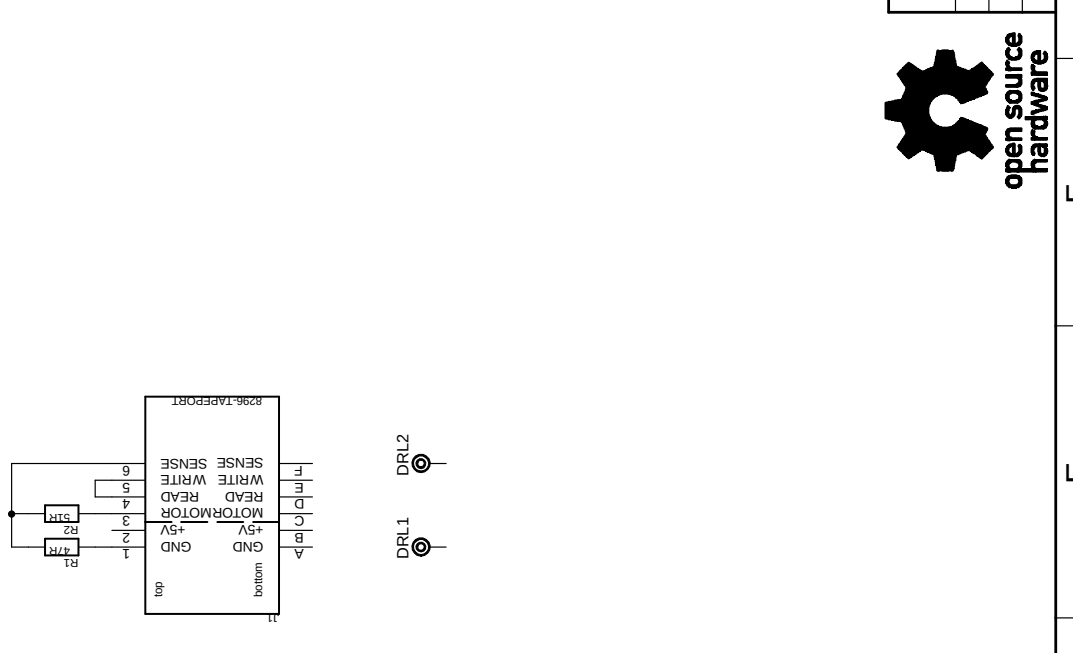
[picture p238: page 5]
CBM8296 Diagnostic; Sven Petersen; DRL1 DRL2; Title:; Date:; Draft.:; Page; KHGFEDCBA; File:; Doc.-No.:; Rev.: 1/1 17.05.2023 10:50; 8296 Diag CP; top; bottom

http://github.com/svenpetersen1965

Cassette Port Dongle

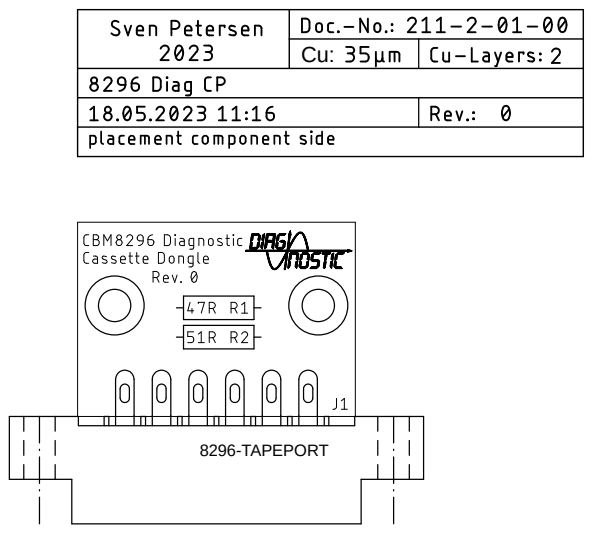
[picture p239: page 6]
8296-TAPEPORT

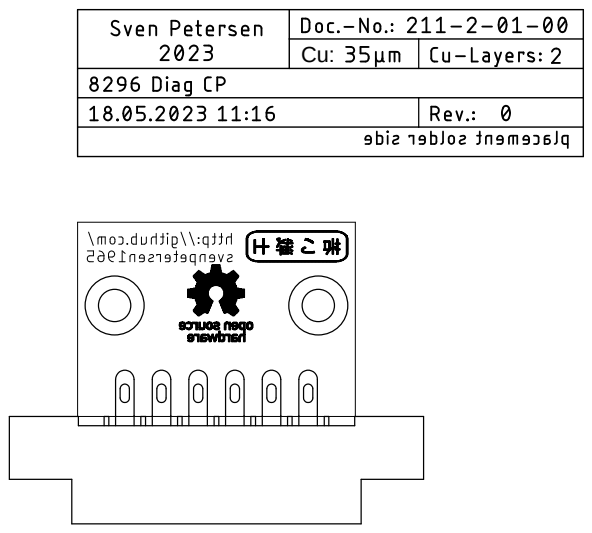
[picture p240: page 7]

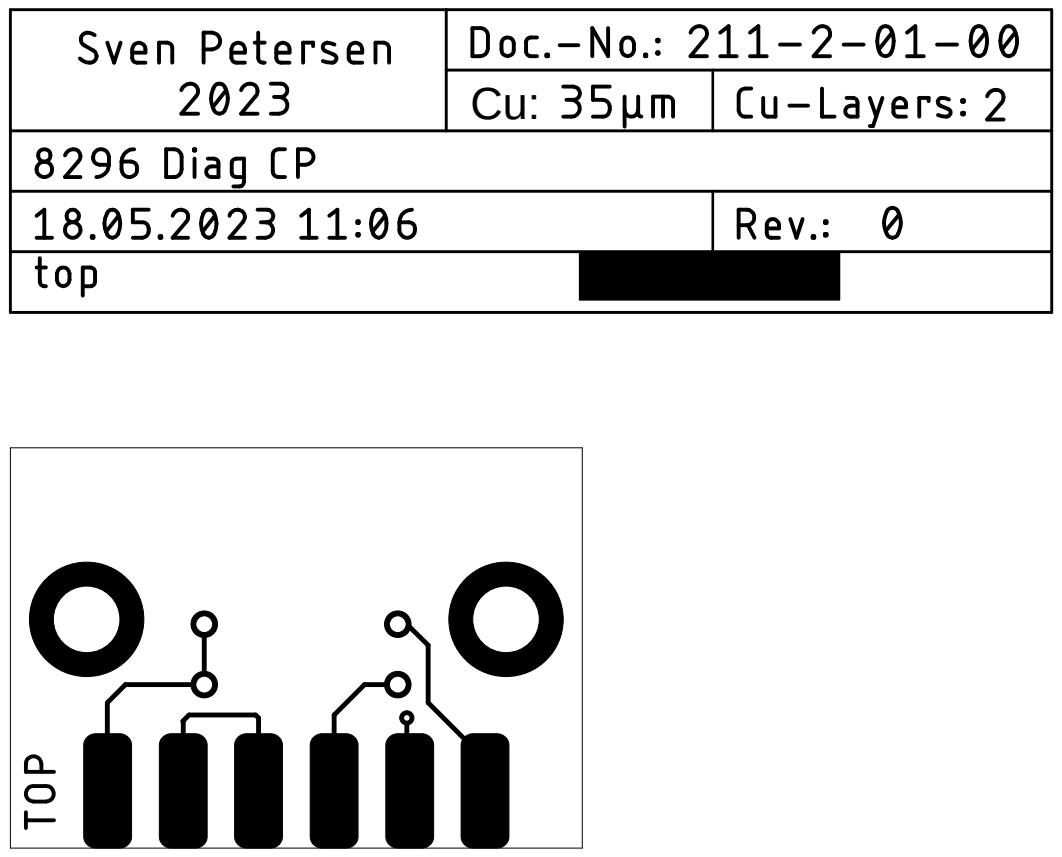
[picture p241: page 8]

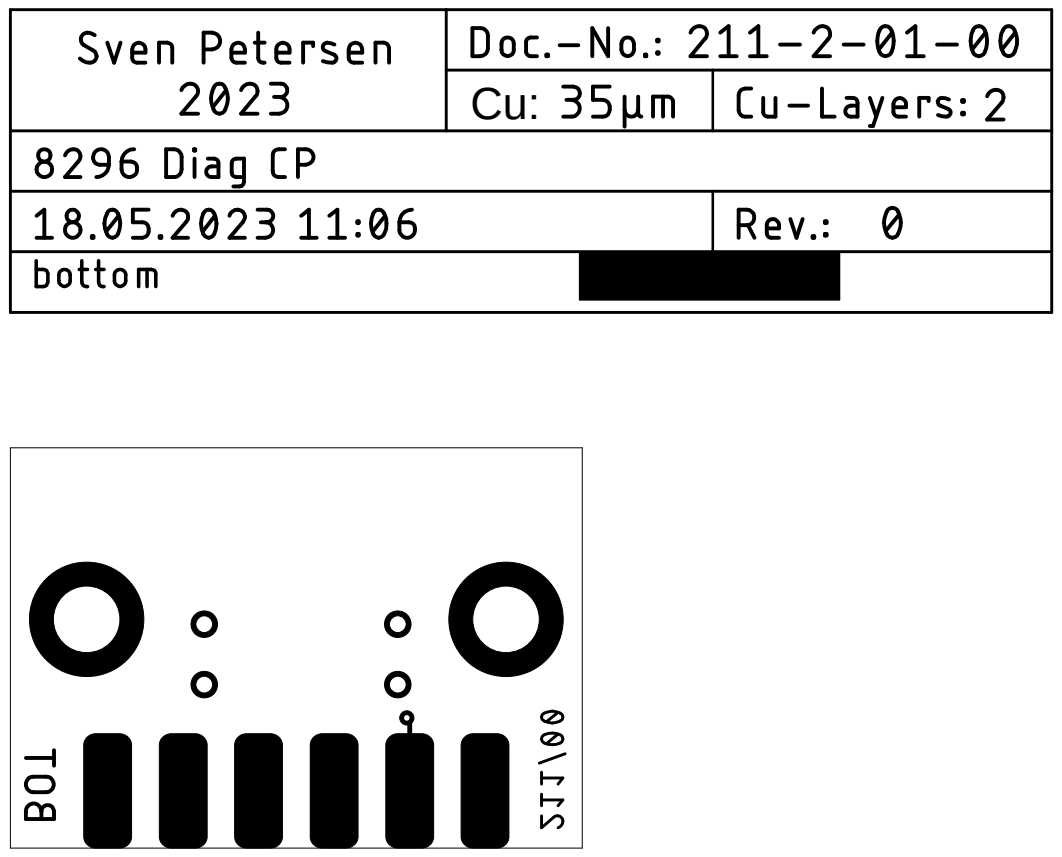
[picture p242: page 9]

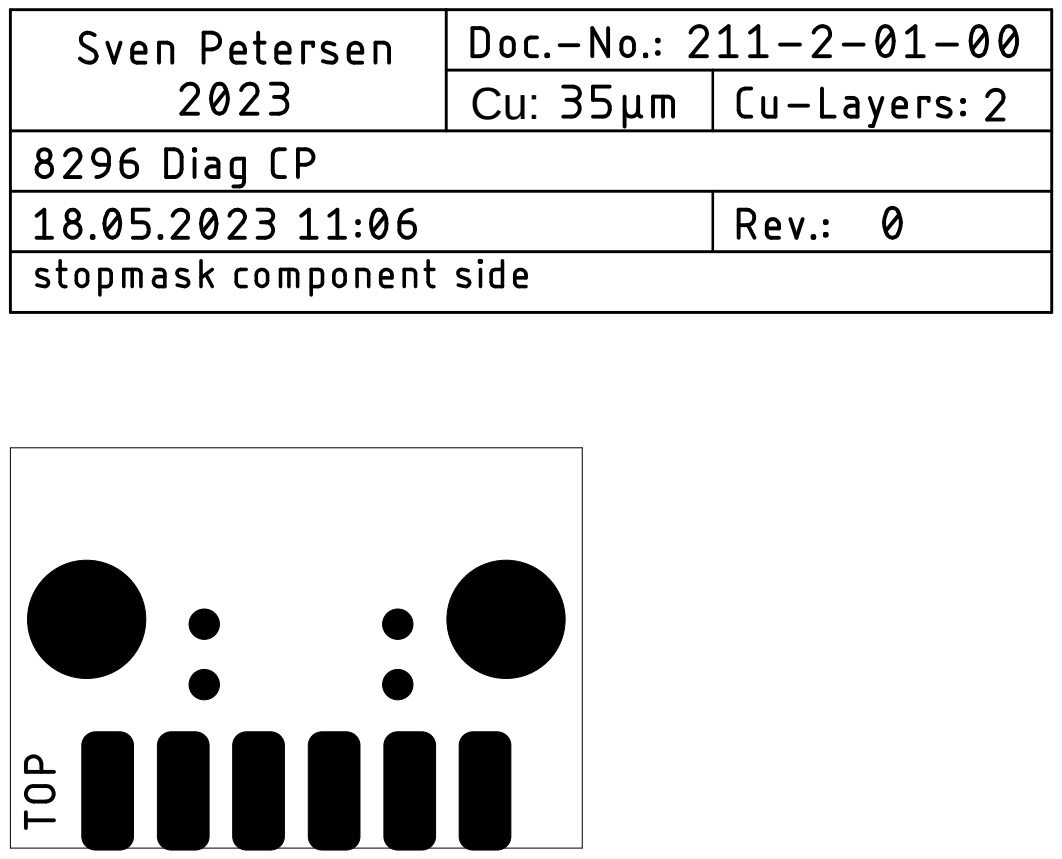
[picture p243: page 10]

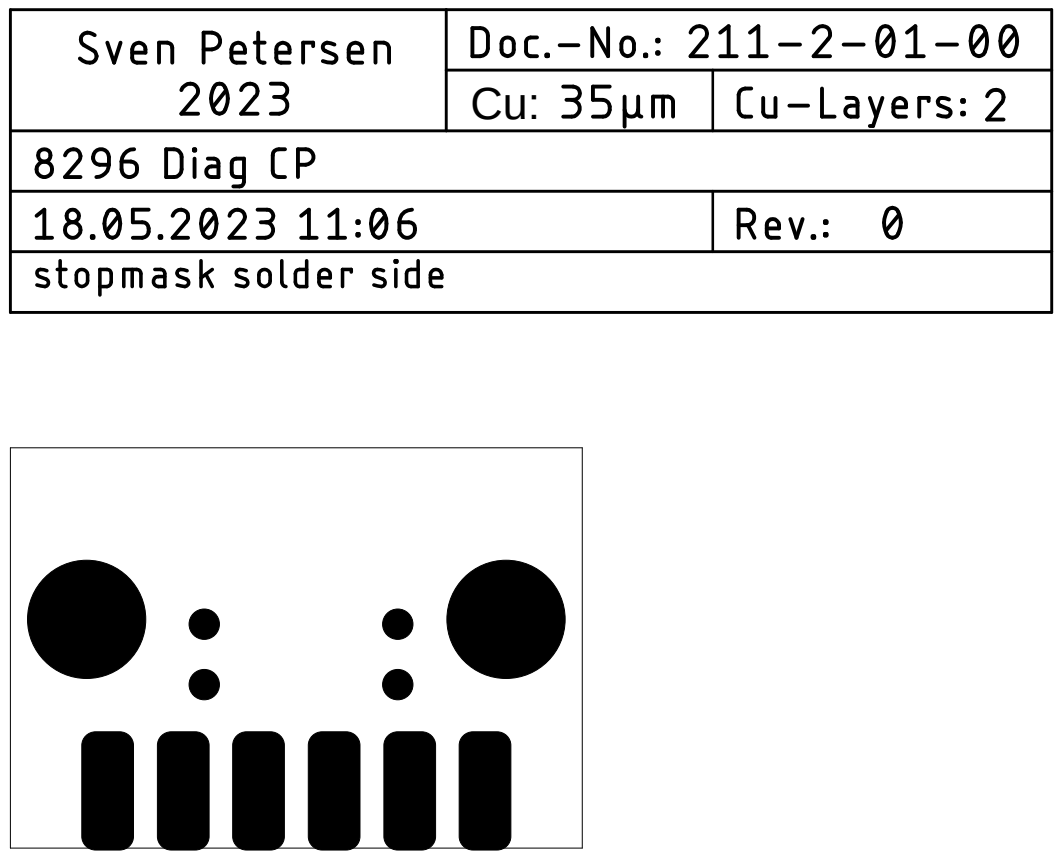
[picture p244: page 11]

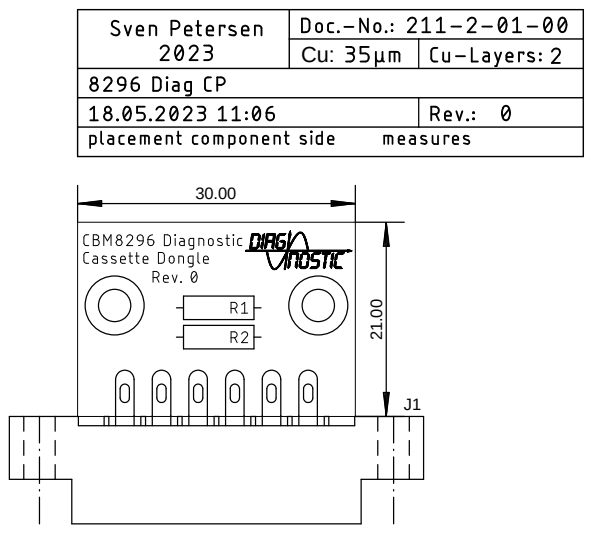
[picture p245: page 12]

Pos. Qty Value Footprint Ref.-No. Comment

1 1 211-2-01-00 2 Layer PCB Rev. 0 2 layer, Cu 35µ, HASL, 30.0mm x 21.0mm, 1.6mm FR4

2 1 47R R-10 R1 1/4 Watt, 5%

3 1 51R R-10 R2 1/4 Watt, 5%

4 1 2x6, 3.96mm pitch TAPEPORT J1 edge connector, C64 cassette port. AliExpress: "Series 805"

## Commodore CBM8296 Diagnostic: Cassette Dongle Rev. 0

## Bill of Material Rev. 0.0

8296diag_CP_BOM_v0_0.xlsx

Drafted by Sven Petersen Page 1 of 1

18.05.2023 11:51
Doc.No.: 211-5-01-00.0
