svenpetersen1965/PET-Diagnostic-Clip/PET_Diagnostic_Clip/Rev. 0/pdf/sch_brd.pdf

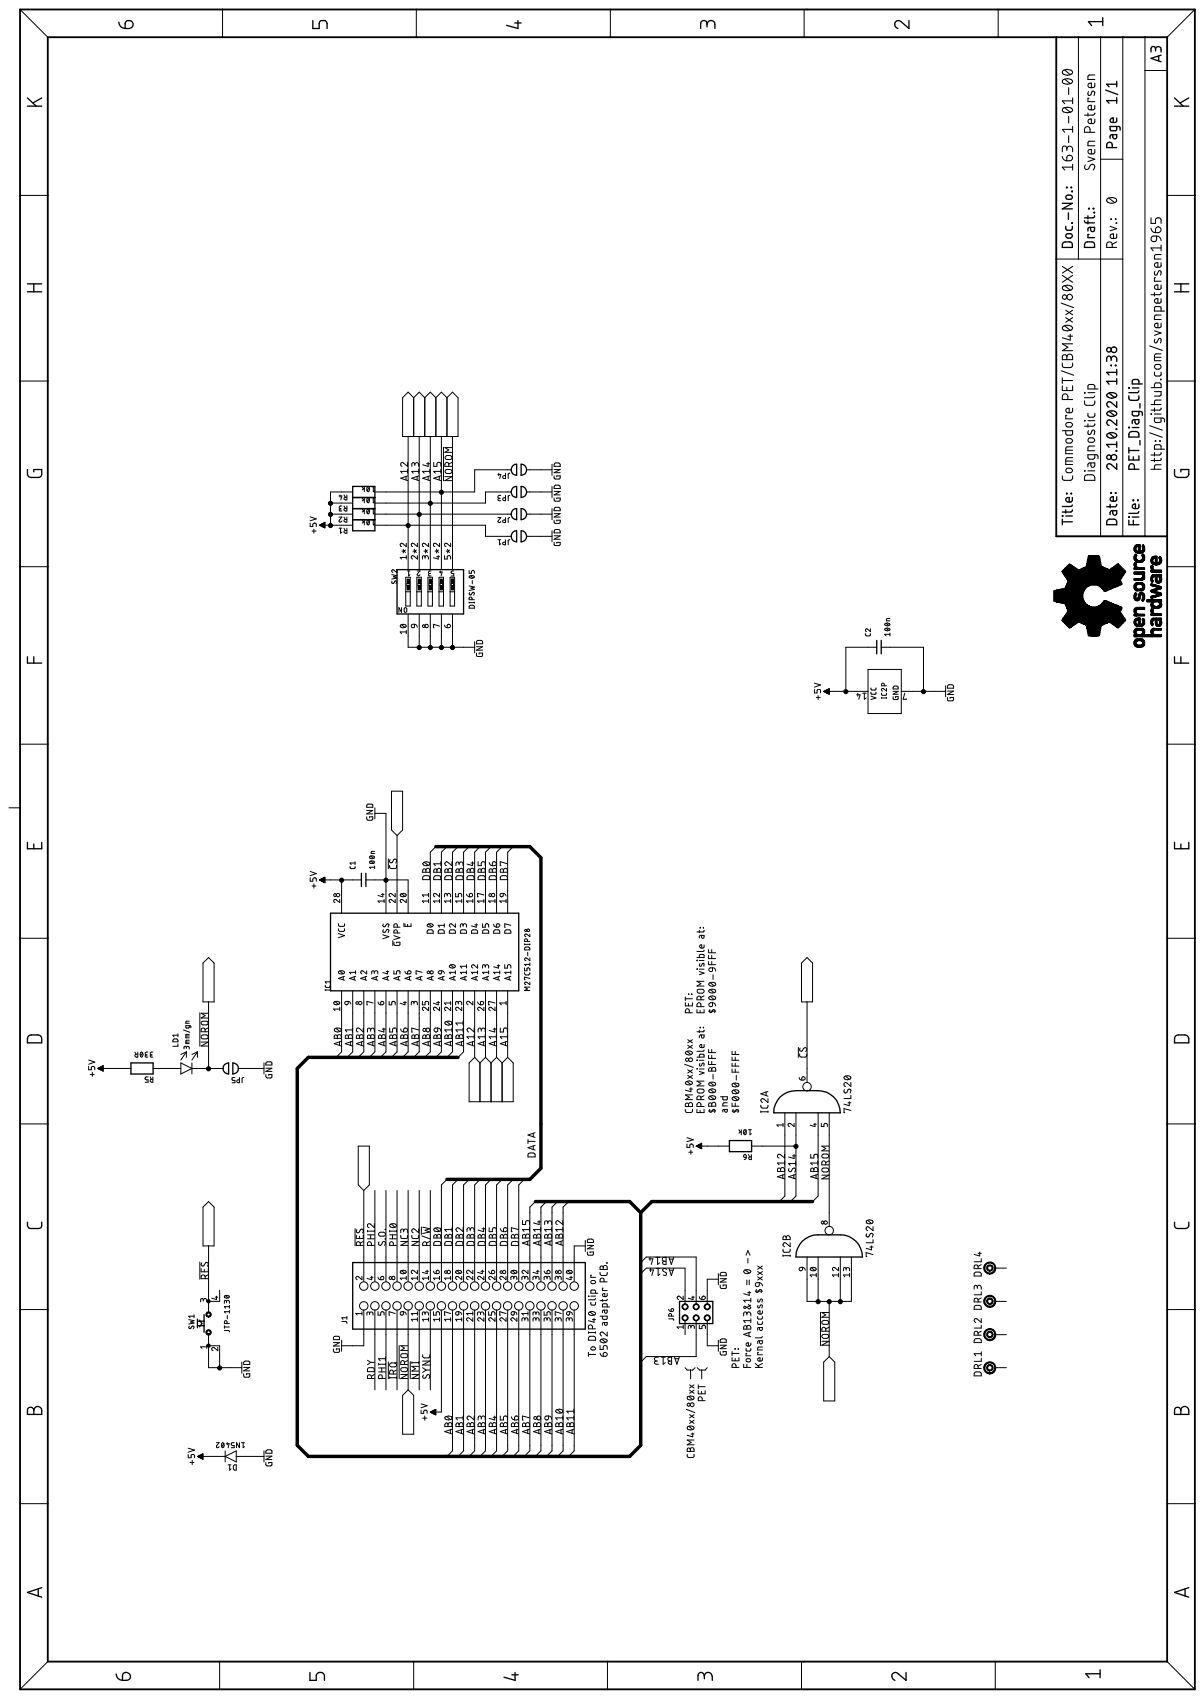
[picture p262: page 1]

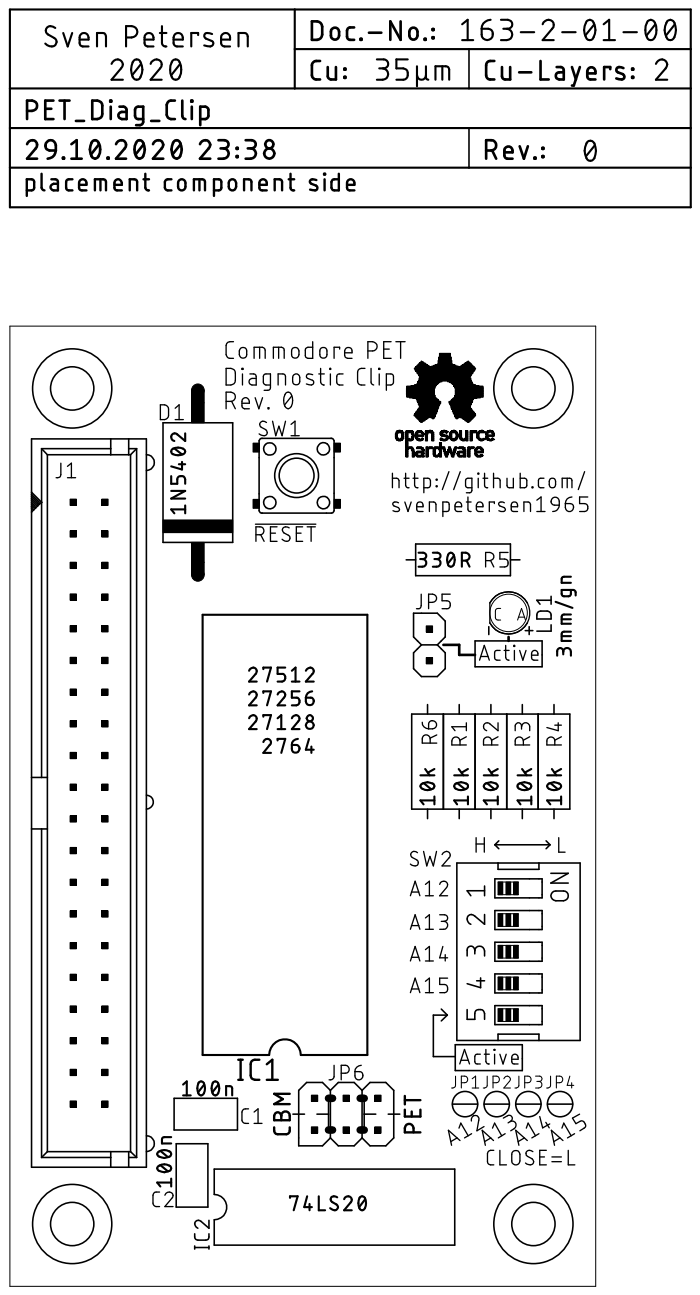
[picture p263: page 2]

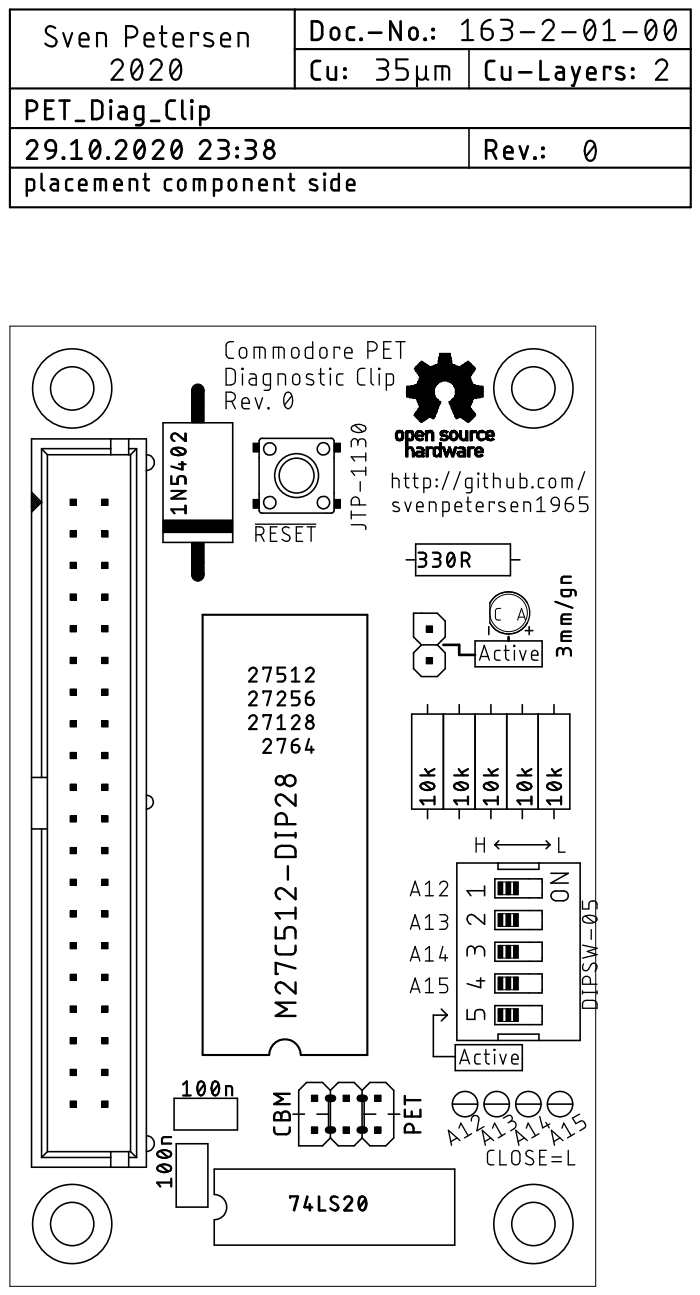
[picture p264: page 3]

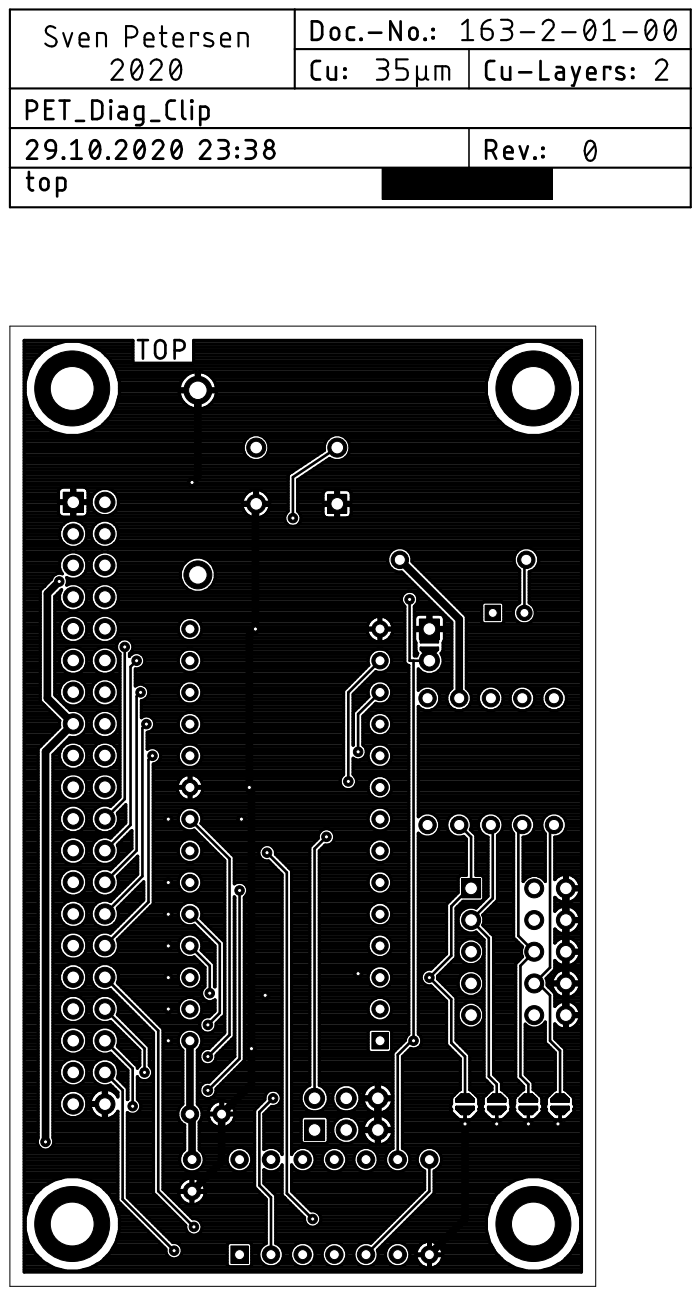
[picture p265: page 4]

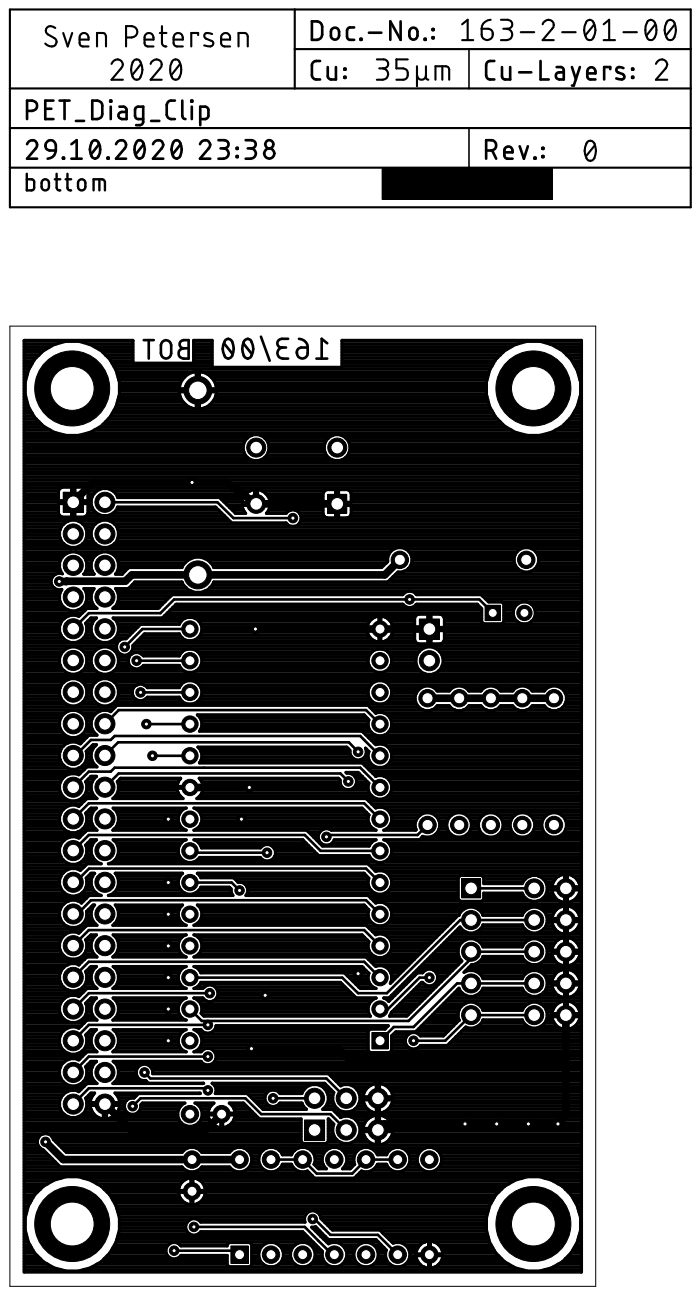
[picture p266: page 5]

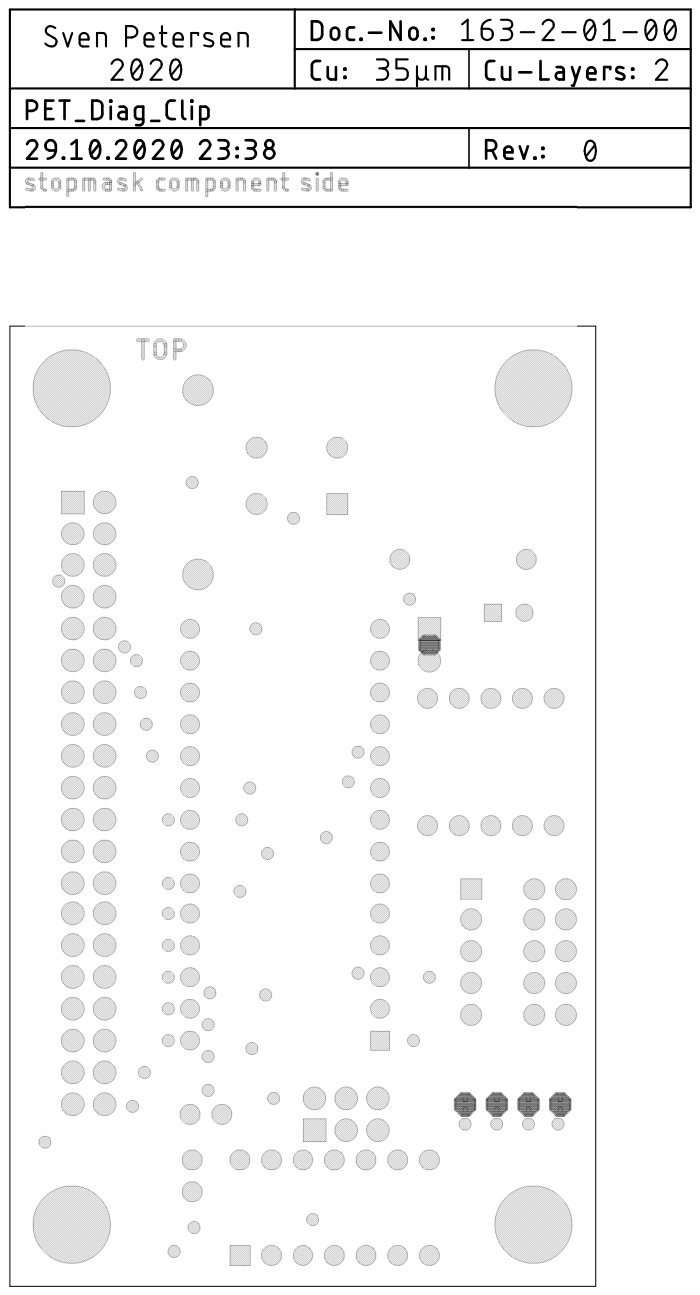
[picture p267: page 6]

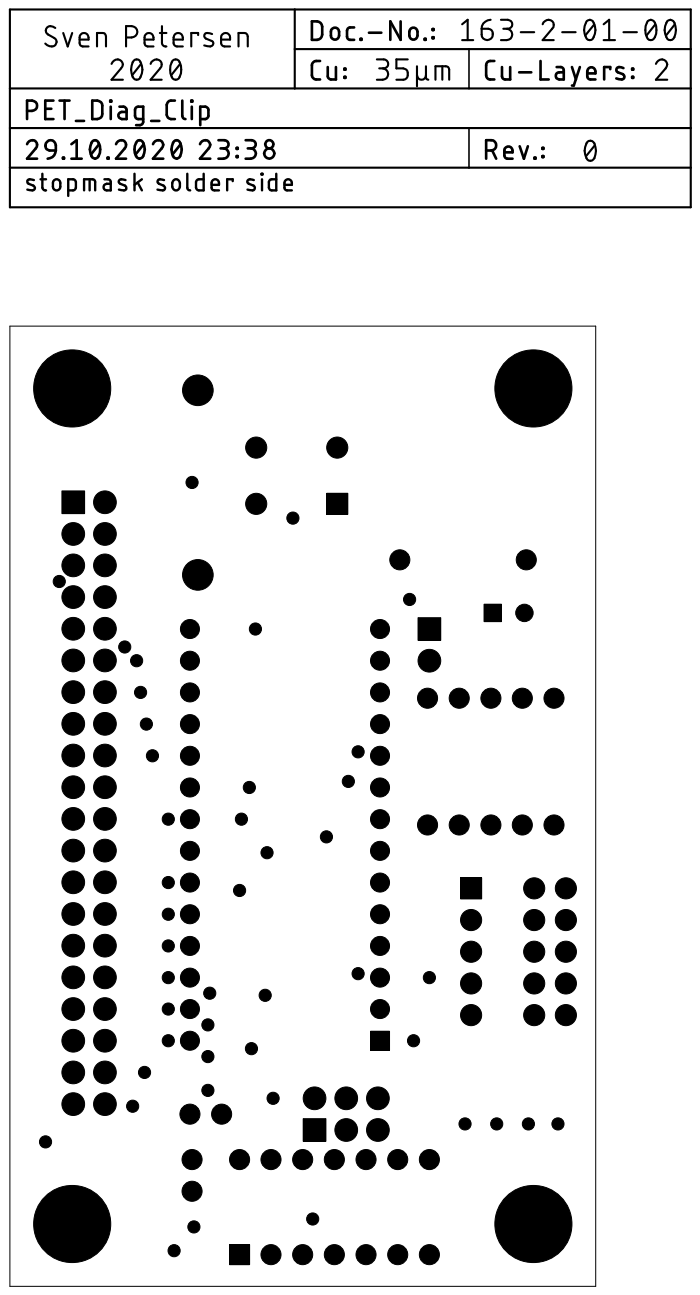
[picture p268: page 7]

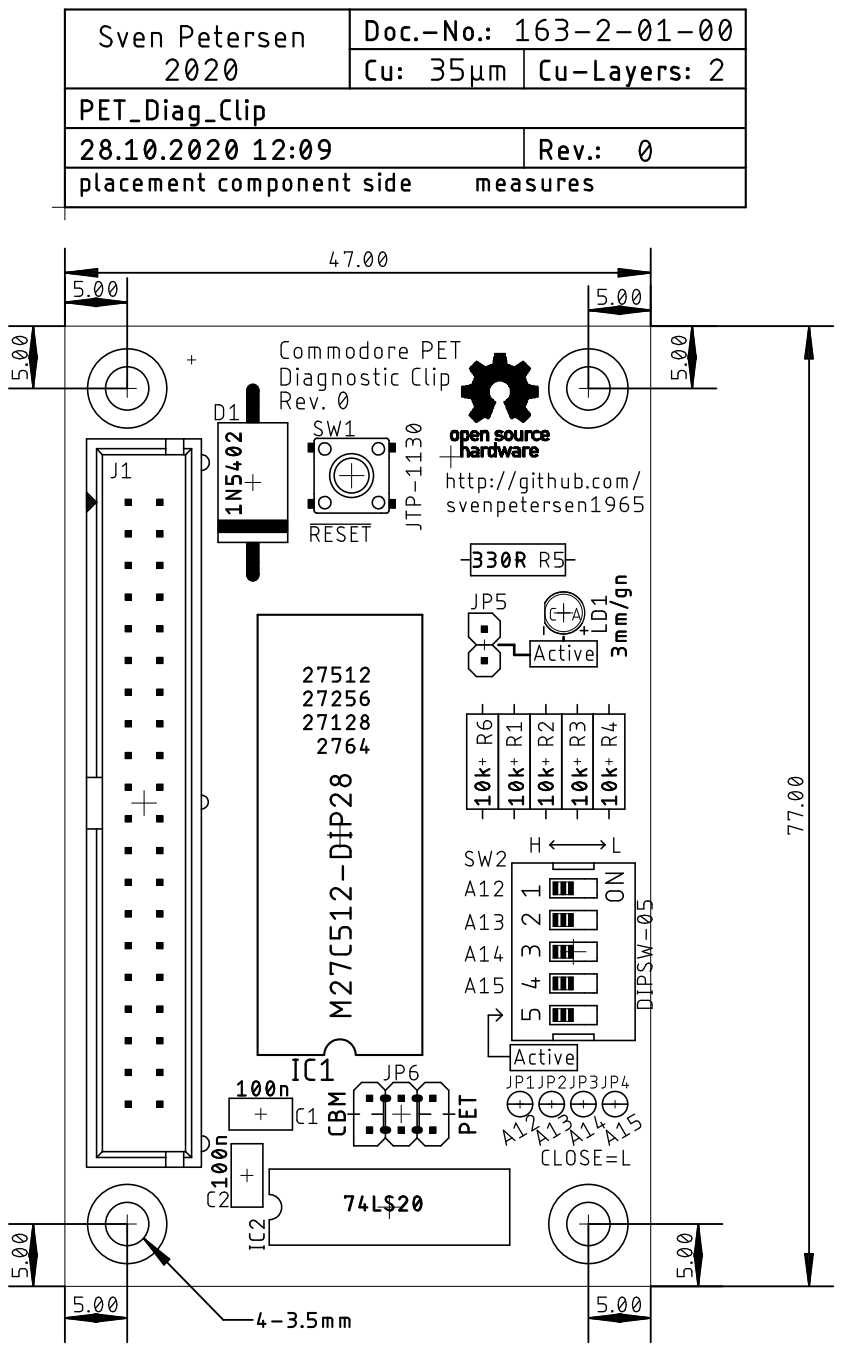
[picture p269: page 8]
